stanley-fork/sol-1/general_docs/5.25_floppy_drive/5.25_pinout.png

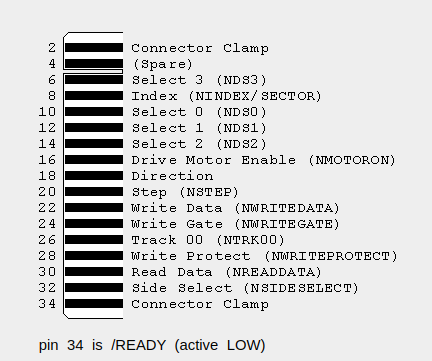
general_docs/5.25_floppy_drive/5.25_pinout.png
