stanley-fork/sol-1/general_docs/5.25_floppy_drive/bbc_master2_floppy_wd1770.gif

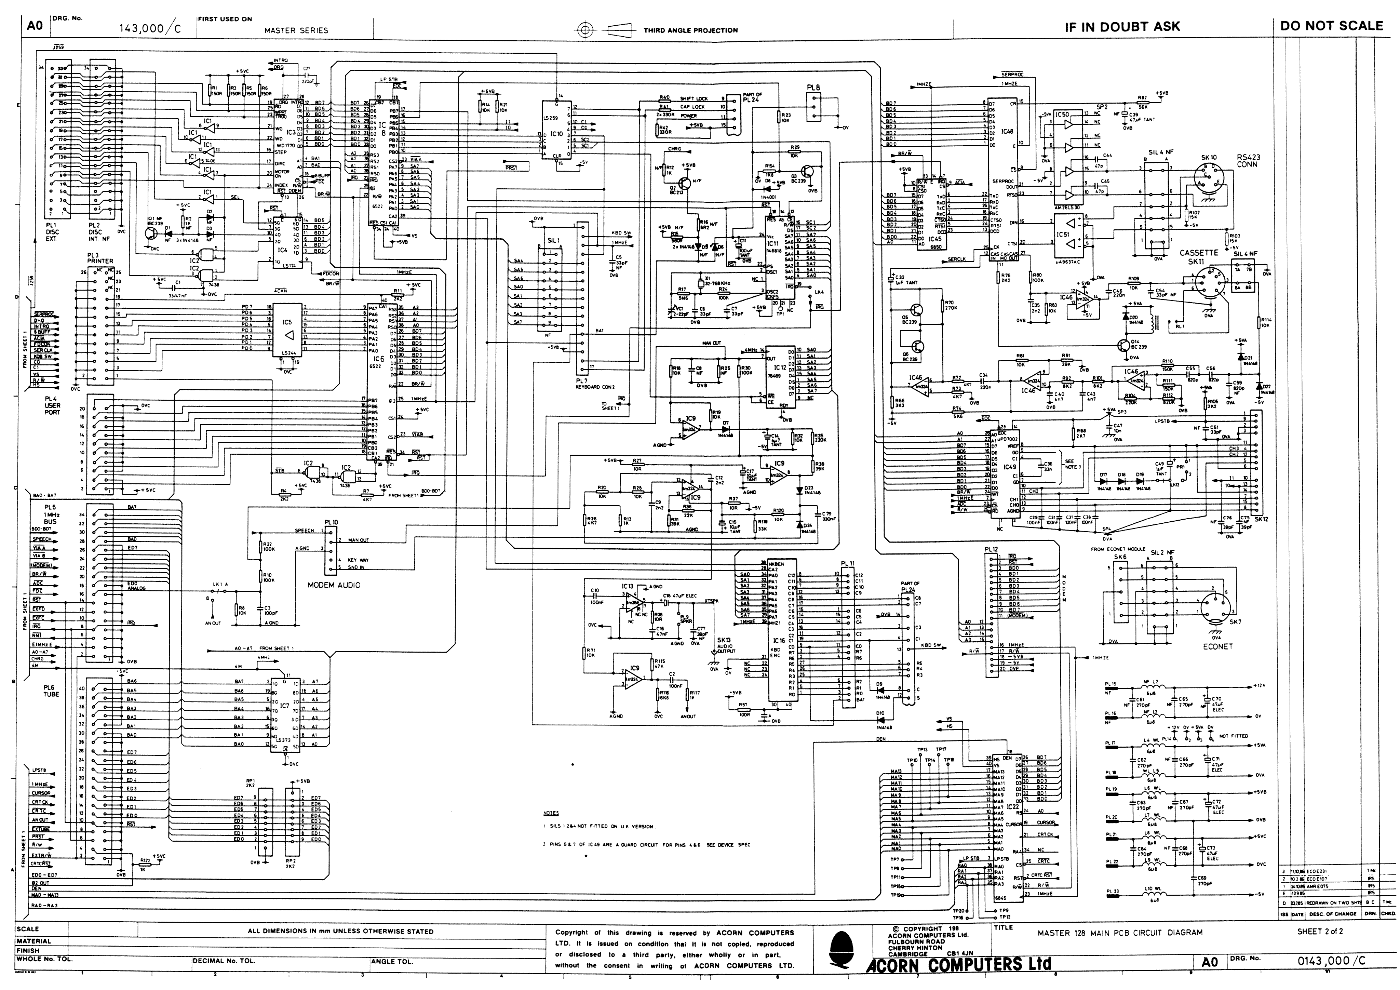
general_docs/5.25_floppy_drive/bbc_master2_floppy_wd1770.gif
