stanley-fork/sol-1/general_docs/5.25_floppy_drive/bbc_wd1772.gif

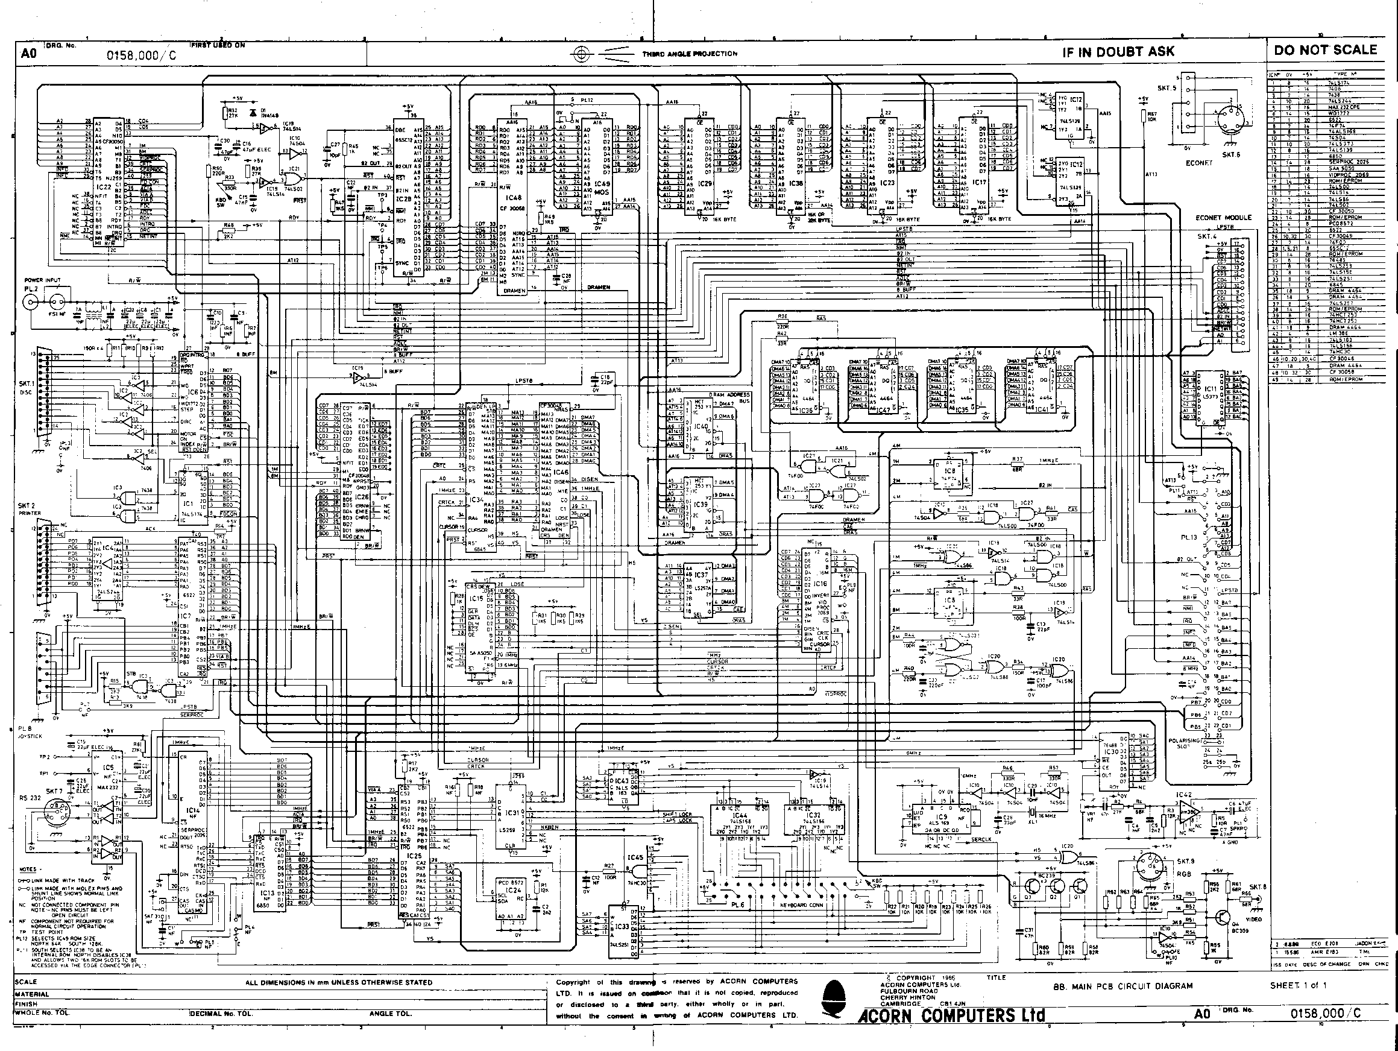
general_docs/5.25_floppy_drive/bbc_wd1772.gif
