stanley-fork/sol-1/general_docs/5.25_floppy_drive/chinon_jumpers.jpg

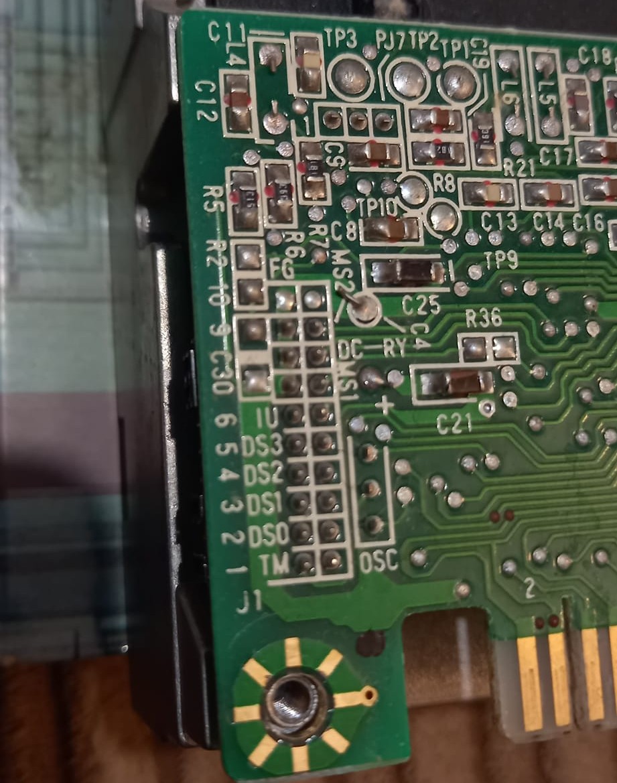
general_docs/5.25_floppy_drive/chinon_jumpers.jpg
