stanley-fork/sol-1/general_docs/5.25_floppy_drive/Floppy Disk Formats_files/hddrive.gif

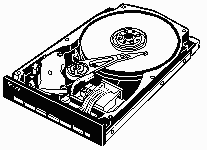
general_docs/5.25_floppy_drive/Floppy Disk Formats_files/hddrive.gif
