stanley-fork/sol-1/general_docs/5.25_floppy_drive/Low-level disk storage_files/disk-1mb.jpg

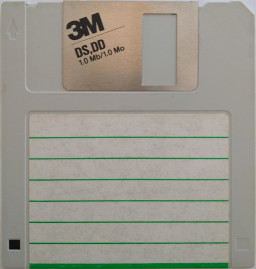
general_docs/5.25_floppy_drive/Low-level disk storage_files/disk-1mb.jpg
