stanley-fork/sol-1/general_docs/5.25_floppy_drive/Low-level disk storage_files/ibm-track-layout.png

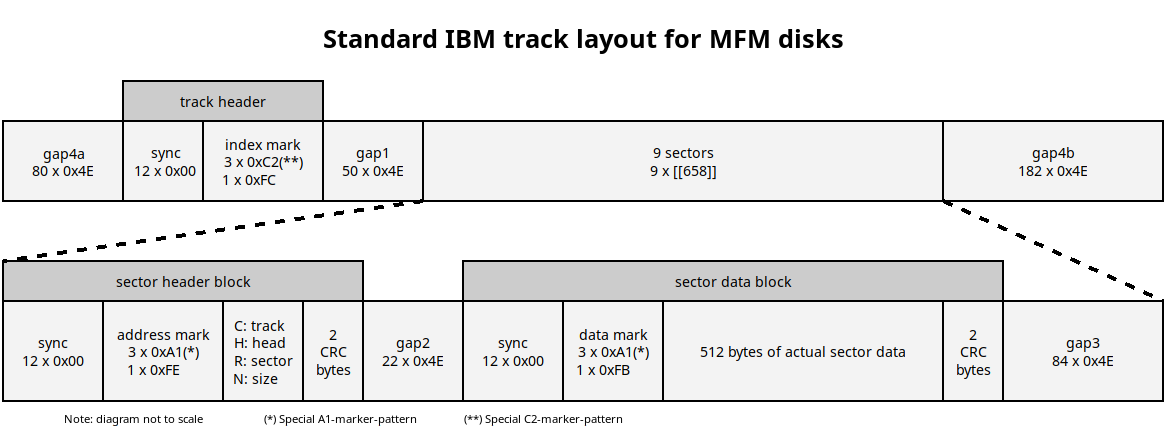
general_docs/5.25_floppy_drive/Low-level disk storage_files/ibm-track-layout.png
