stanley-fork/sol-1/general_docs/5.25_floppy_drive/master1.gif

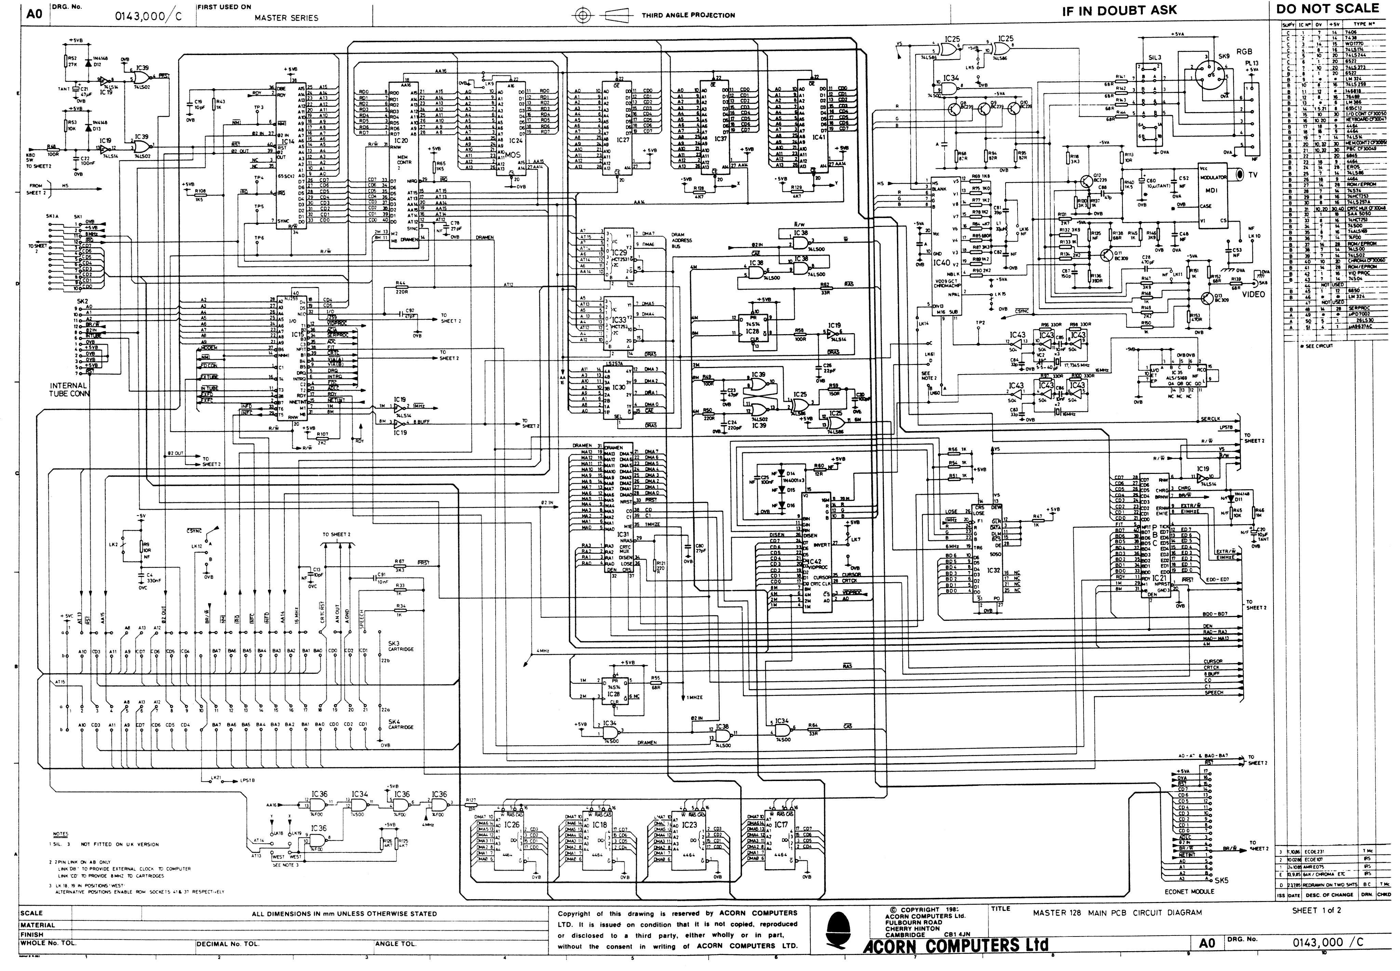
general_docs/5.25_floppy_drive/master1.gif
