stanley-fork/sol-1/general_docs/5.25_floppy_drive/pi-fdc-schematic-0.3.jpg

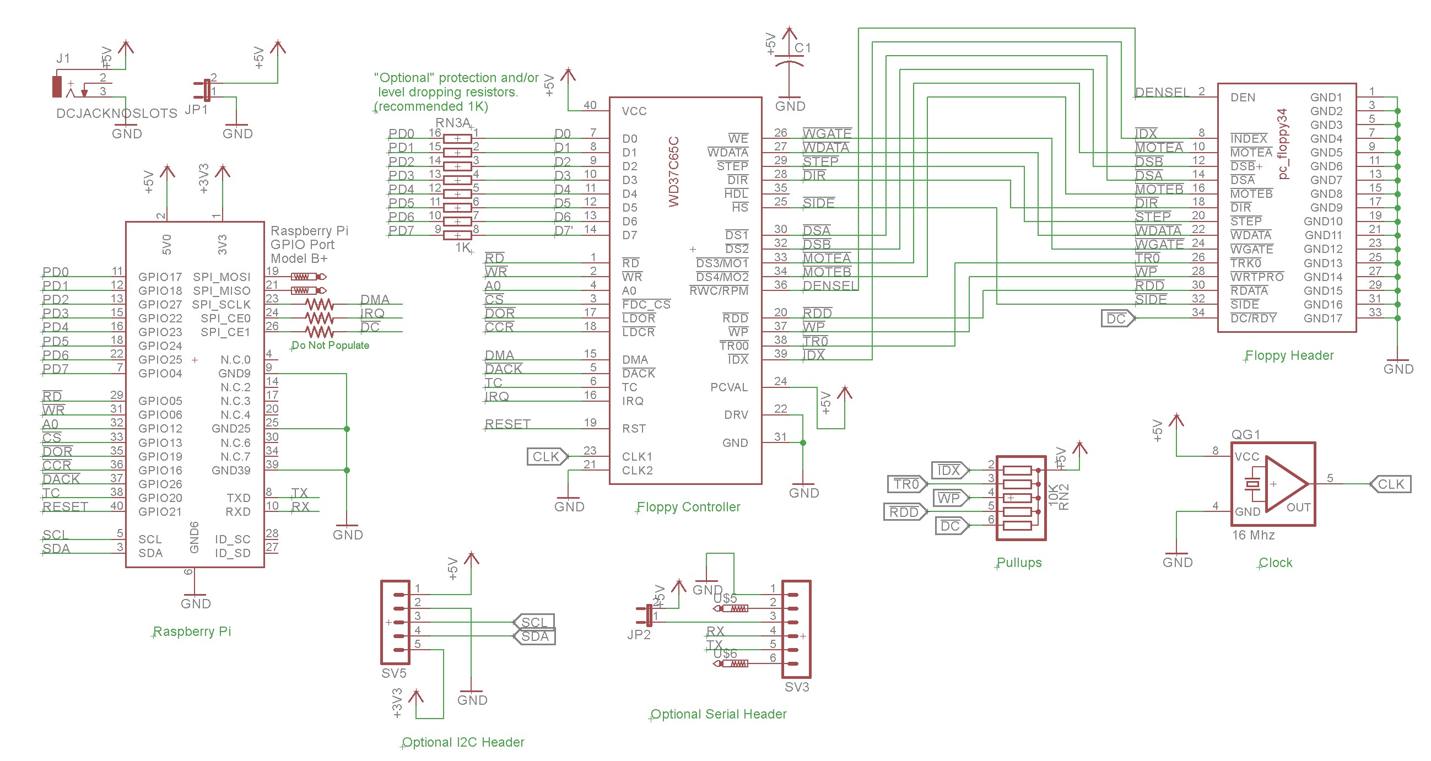
general_docs/5.25_floppy_drive/pi-fdc-schematic-0.3.jpg
