stanley-fork/sol-1/general_docs/5.25_floppy_drive/power_pinout.jpg

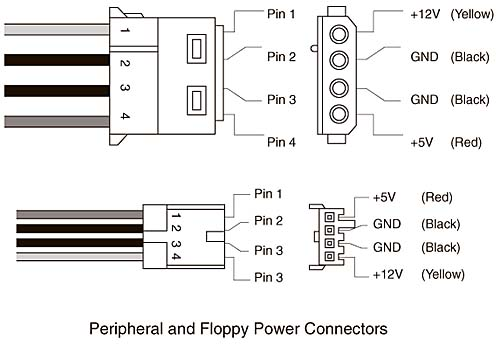
general_docs/5.25_floppy_drive/power_pinout.jpg
