stanley-fork/sol-1/general_docs/5.25_floppy_drive/rc2014-floppy-wd-sch.png

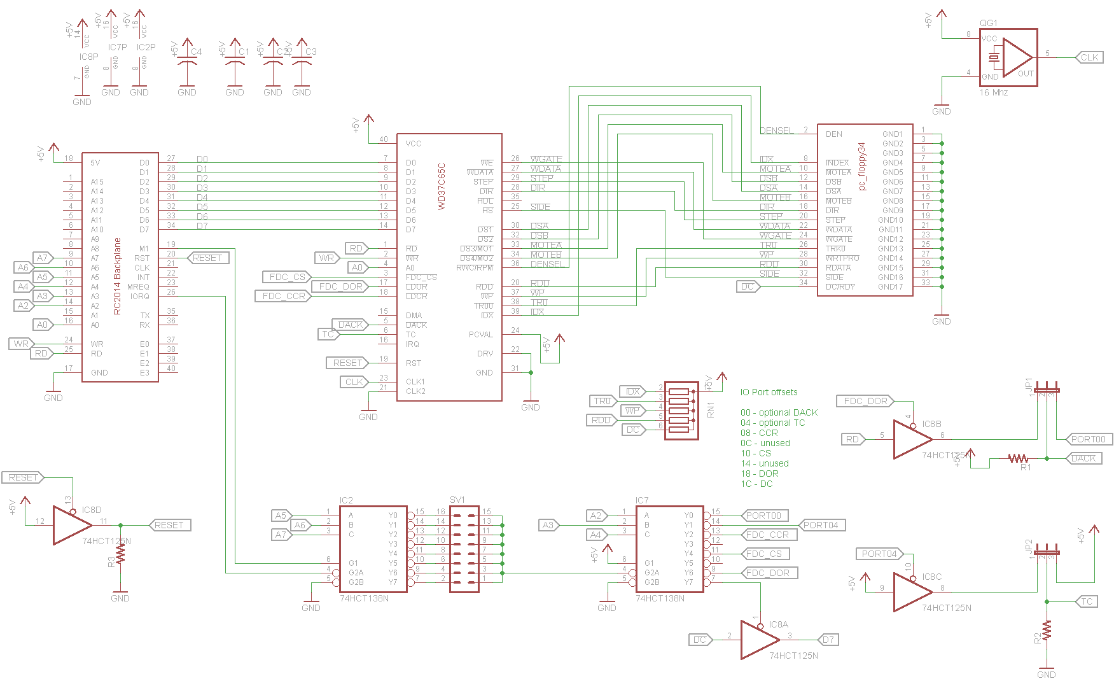
general_docs/5.25_floppy_drive/rc2014-floppy-wd-sch.png
