stanley-fork/sol-1/general_docs/5.25_floppy_drive/S100 Computers  wd1771_files/VersafloppyII RevC.jpg

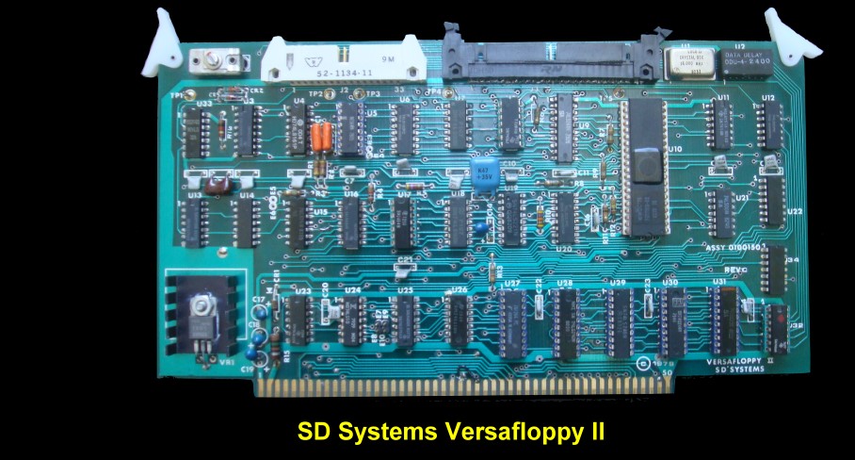
general_docs/5.25_floppy_drive/S100 Computers wd1771_files/VersafloppyII RevC.jpg
