stanley-fork/sol-1/general_docs/5.25_floppy_drive/sol-1_floppy_drives/s-l1600 (5).webp

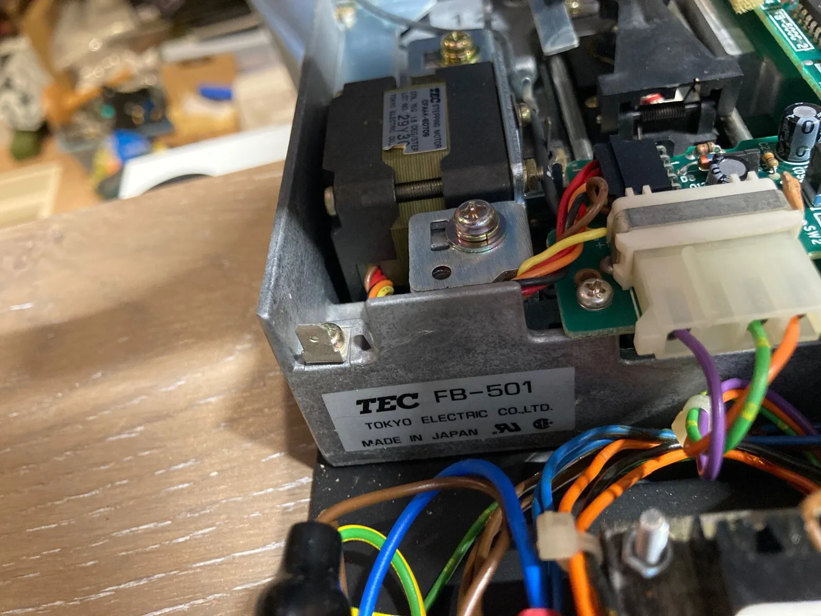
general_docs/5.25_floppy_drive/sol-1_floppy_drives/s-l1600 (5).webp
