stanley-fork/sol-1/general_docs/5.25_floppy_drive/track_format.png

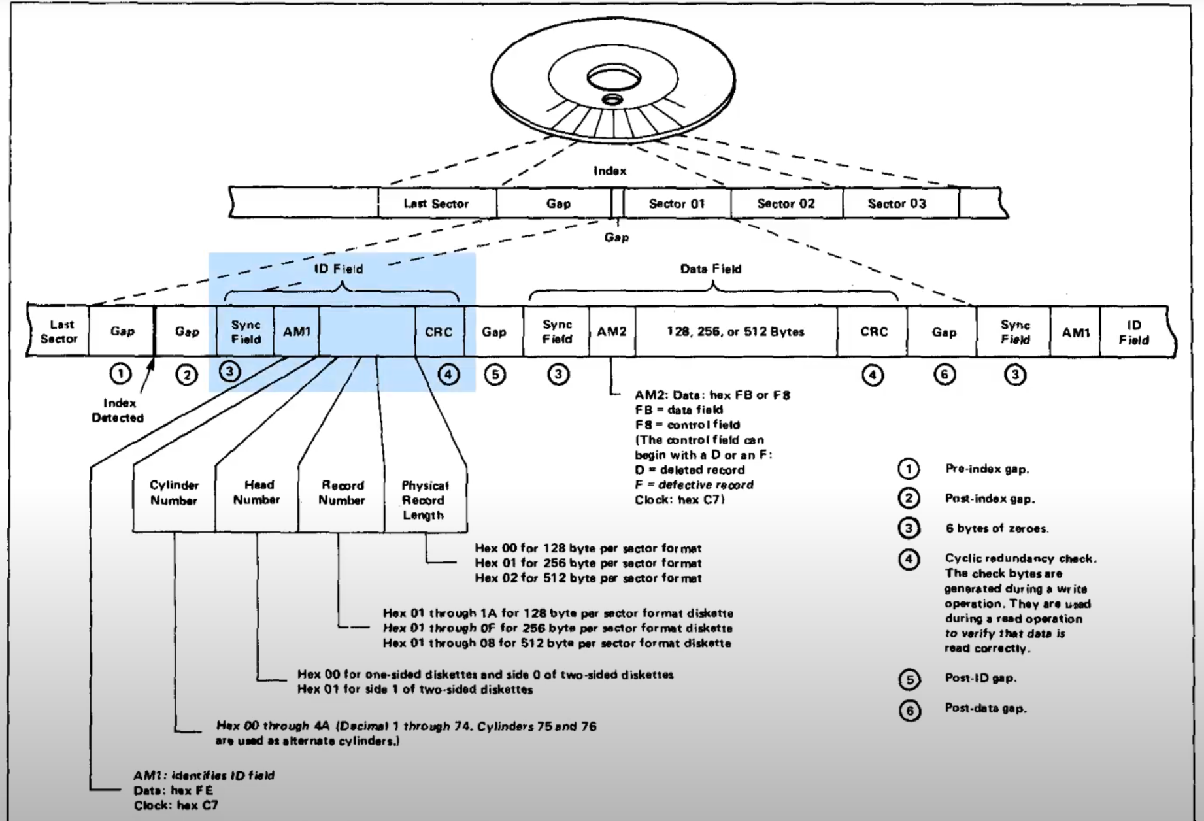
general_docs/5.25_floppy_drive/track_format.png
