stanley-fork/sol-1/general_docs/5.25_floppy_drive/wd1770_formatting.png

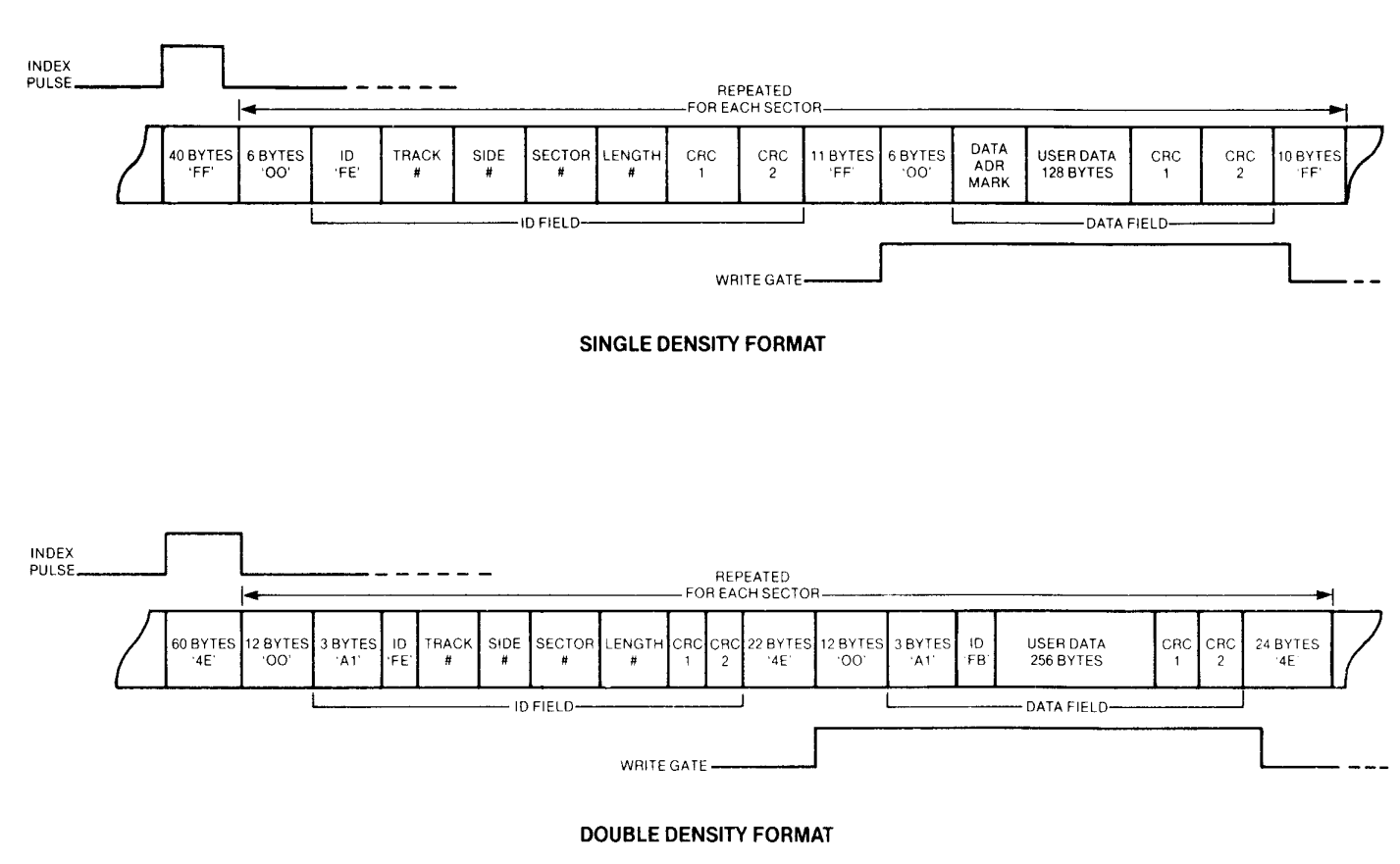
general_docs/5.25_floppy_drive/wd1770_formatting.png
