stanley-fork/sol-1/general_docs/division2.png

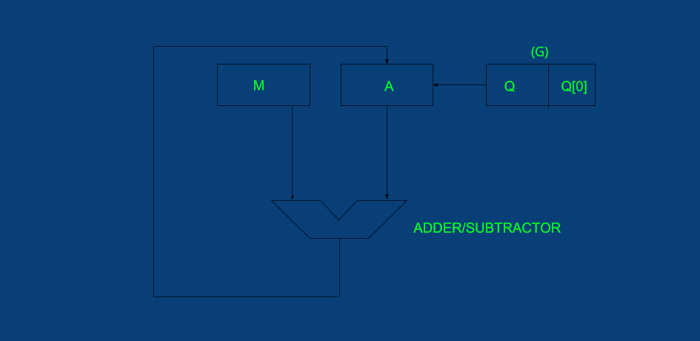
general_docs/division2.png
