stanley-fork/sol-1/hardware/board-images/frontpanel/front_panel_orange.jpg

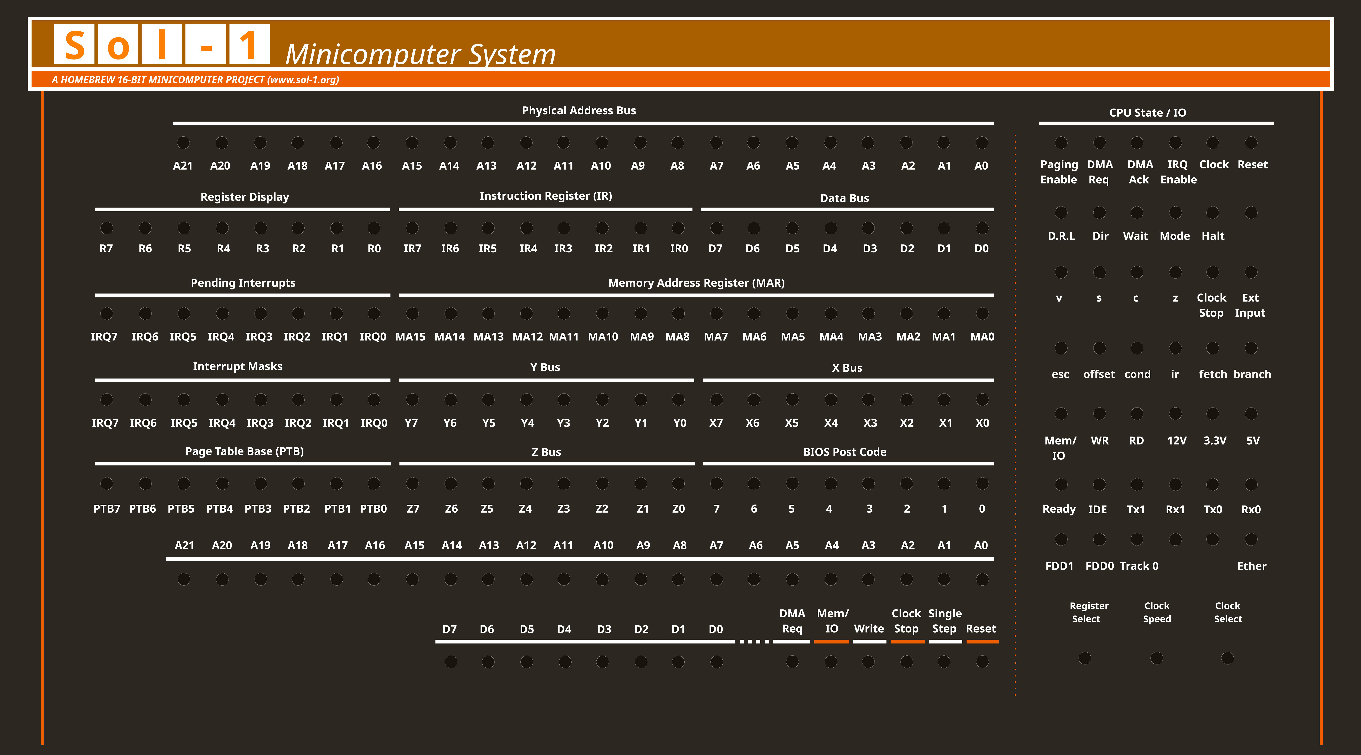
hardware/board-images/frontpanel/front_panel_orange.jpg
