stanley-fork/sol-1/images/513552633_754775293648044_8493645903438543306_n.jpg

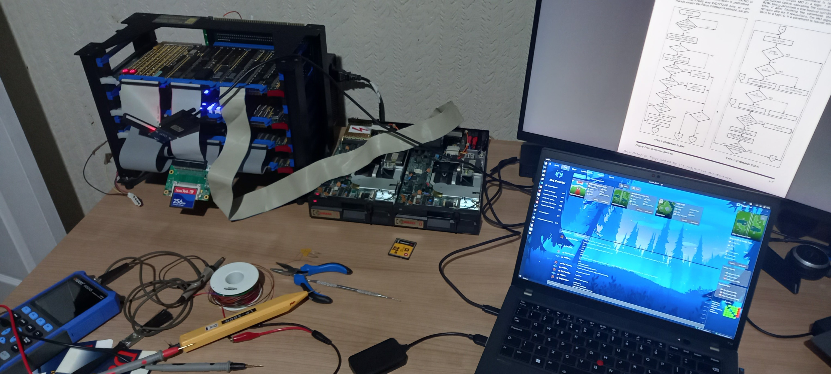
images/513552633_754775293648044_8493645903438543306_n.jpg
