stanley-fork/sol-1/web/images/bg/background.jpg

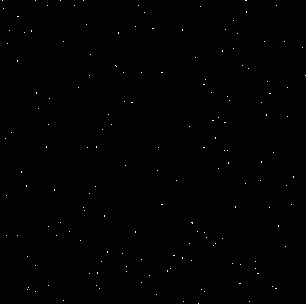
web/images/bg/background.jpg
