stanley-fork/sol-1/general_docs/5.25_floppy_drive/flock-v2-main/images/Flock-V2-Assembled_Board_in_Backplane.jpg

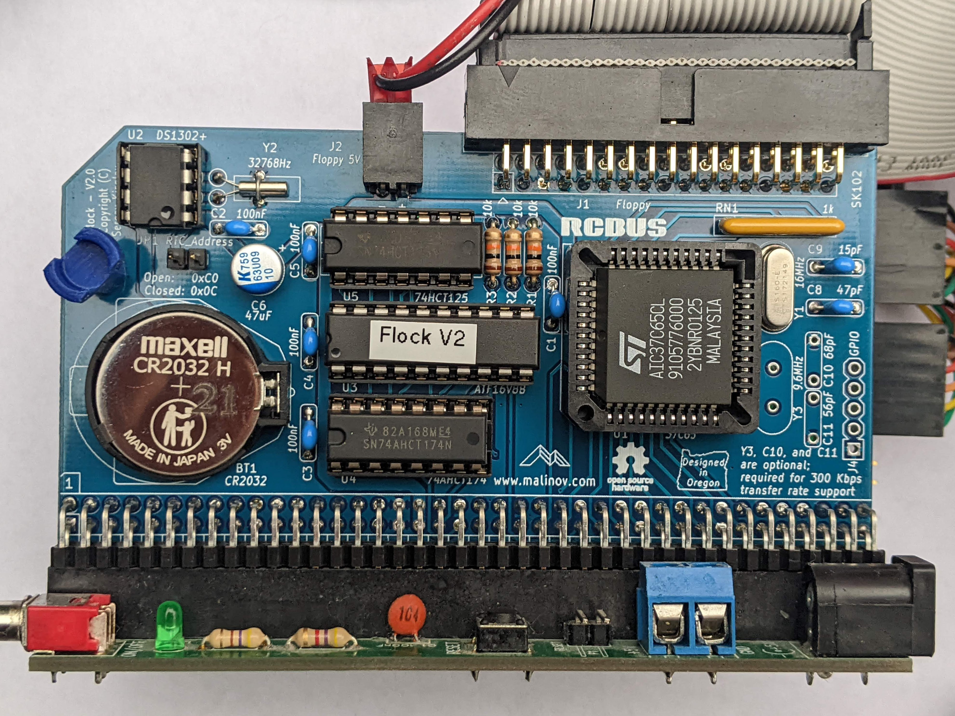
general_docs/5.25_floppy_drive/flock-v2-main/images/Flock-V2-Assembled_Board_in_Backplane.jpg
