stanley-fork/sol-1/general_docs/5.25_floppy_drive/Operating Systems Development Series_files/flpy.png

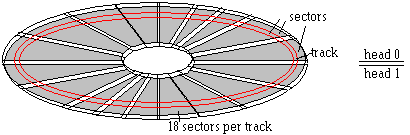
general_docs/5.25_floppy_drive/Operating Systems Development Series_files/flpy.png
