stanley-fork/sol-1/hardware/schematics/kicad/registers_paging_irq.kicad_sch

## KiCad design hardware/schematics/kicad/registers_paging_irq.kicad_sch (2025-10-18)

Schematic: registers_paging_irq.kicad_sch

Parts:
IC43, IC113: 7404N; DIP-14_W7.62mm
IC46, IC52: 7400N; DIP-14_W7.62mm
IC53, IC54, IC55, IC56, IC57, IC58, IC59, IC60, IC61, IC62, IC63, IC64, IC71, IC72, IC73, IC74, IC75, IC84, IC85, IC87, IC88, IC90, IC93, IC191: 74377N; DIP-20_W7.62mm
IC70: 7432N; DIP-14_W7.62mm
IC109: 7427N; DIP-14_W7.62mm
IC111, IC112, IC157, IC158, IC159, IC160, IC180, IC190: 74257N; DIP-16_W7.62mm
IC117, IC118, IC119, IC120, IC178, IC179: 74244N; DIP-20_W7.62mm
IC123, IC124, IC125, IC126, IC127, IC128, IC129, IC130, IC131, IC132, IC133, IC134, IC135, IC136, IC137, IC138, IC141, IC142, IC143, IC144, IC145, IC146, IC147, IC148, IC149, IC150, IC151, IC152, IC153, IC154, IC166, IC167: 74151N; DIP-16_W7.62mm
IC139, IC140, IC168, IC169: 74153N; DIP-16_W7.62mm
IC163, IC177: 58C256P; DIP-28_W15.24mm
IC181, IC182, IC183, IC184: 74157N; DIP-16_W7.62mm
IRQ_0_DFF1, IRQ_1_DFF1, IRQ_2_DFF1, IRQ_3_DFF1: 7474N; DIP-14_W7.62mm
IRQ_AND_1, IRQ_AND_2: 7408N; DIP-14_W7.62mm
IRQ_CODE1: 74377N; DIP-20_W7.62mm
IRQ_ENCODER1: 74148N; DIP-16_W7.62mm
IRQ_RST_DECODER1: 74138N; DIP-16_W7.62mm
IRQ_STATUS_1: 74273N; DIP-20_W7.62mm
MARH1: 74377N; DIP-20_W7.62mm
MARL1: 74377N; DIP-20_W7.62mm
MDRH1: 74377N; DIP-20_W7.62mm
MDRL1: 74377N; DIP-20_W7.62mm
MDR_IN_MUX_1, MDR_IN_MUX_2: 74157N; DIP-16_W7.62mm
MDR_OUT_MUX_1, MDR_OUT_MUX_2: 74157N; DIP-16_W7.62mm
RN2: R_Pack08; DIP-16_W7.62mm
U19: 74HC04; DIP-14_W7.62mm

Connections:
GND: IC109.2 (I1), IC111.15 (G), IC112.5 (2A), IC112.6 (2B), IC112.10 (3B), IC112.11 (3A), IC112.13 (4B), IC112.14 (4A), IC112.15 (G), IC120.4 (A2), IC120.6 (A3), IC120.8 (A4), IC123.7 (G), IC124.7 (G), IC125.7 (G), IC126.7 (G), IC126.12 (D7), IC126.13 (D6), IC126.14 (D5), IC127.7 (G), IC128.7 (G), IC129.7 (G), IC130.7 (G), IC130.12 (D7), IC130.13 (D6), IC130.14 (D5), IC131.7 (G), IC132.7 (G), IC133.7 (G), IC134.7 (G), IC134.12 (D7), IC134.13 (D6), IC134.14 (D5), IC135.7 (G), IC136.7 (G), IC137.7 (G), IC138.7 (G), IC138.12 (D7), IC138.13 (D6), IC138.14 (D5), IC139.1 (1G), IC139.15 (2G), IC140.1 (1G), IC140.15 (2G), IC141.7 (G), IC142.7 (G), IC143.7 (G), IC144.7 (G), IC144.12 (D7), IC144.13 (D6), IC144.14 (D5), IC145.7 (G), IC146.7 (G), IC147.7 (G), IC148.7 (G), IC148.12 (D7), IC148.13 (D6), IC148.14 (D5), IC149.7 (G), IC150.7 (G), IC151.7 (G), IC152.7 (G), IC152.12 (D7), IC152.13 (D6), IC152.14 (D5), IC153.7 (G), IC154.7 (G), IC157.15 (G), IC158.5 (2A), IC158.11 (3A), IC158.14 (4A), IC158.15 (G), IC159.2 (1A), IC159.5 (2A), IC159.11 (3A), IC159.15 (G), IC160.11 (3A), IC160.14 (4A), IC160.15 (G), IC163.1 (A14), IC163.14 (VSS), IC163.20 (~CE), IC163.26 (A13), IC166.7 (G), IC167.7 (G), IC167.12 (D7), IC167.13 (D6), IC167.14 (D5), IC168.1 (1G), IC168.15 (2G), IC169.1 (1G), IC169.15 (2G), IC177.1 (A14), IC177.14 (VSS), IC177.20 (~CE), IC177.26 (A13), IC180.2 (1A), IC180.5 (2A), IC180.11 (3A), IC180.14 (4A), IC180.15 (G), IC181.15 (G), IC182.15 (G), IC183.15 (G), IC184.15 (G), IC190.2 (1A), IC190.5 (2A), IC190.11 (3A), IC190.14 (4A), IC190.15 (G), IRQ_CODE1.3 (1D), IRQ_CODE1.13 (5D), IRQ_CODE1.14 (6D), IRQ_CODE1.17 (7D), IRQ_CODE1.18 (8D), IRQ_ENCODER1.5 (EI), IRQ_RST_DECODER1.4 (G2A), IRQ_RST_DECODER1.5 (G2B), MDR_IN_MUX_1.15 (G), MDR_IN_MUX_2.15 (G), RN2.1 (R1.1), RN2.2 (R2.1), RN2.3 (R3.1), RN2.4 (R4.1), RN2.5 (R5.1), RN2.6 (R6.1), RN2.7 (R7.1), RN2.8 (R8.1)
unnamed: IC46.3 (O), IRQ_ENCODER1.4 (7)
unnamed: IC46.6 (O), IRQ_ENCODER1.3 (6)
unnamed: IC46.8 (O), IRQ_ENCODER1.2 (5)
unnamed: IC46.11 (O), IRQ_ENCODER1.1 (4)
unnamed: IC52.3 (O), IRQ_ENCODER1.13 (3)
unnamed: IC52.6 (O), IRQ_ENCODER1.12 (2)
unnamed: IC52.8 (O), IRQ_ENCODER1.11 (1)
unnamed: IC52.11 (O), IRQ_ENCODER1.10 (0)
unnamed: IC70.3 (O), IC90.1 (G)
unnamed: IC70.6 (O), IC93.1 (G)
unnamed: IC109.12 (O), IC111.1 (~A/B), IC112.1 (~A/B)
unnamed: IC113.8 (O), IC163.27 (~WE), IC177.27 (~WE)
unnamed: IC118.8 (A4), IC157.4 (1Y)
unnamed: IC118.11 (A1), IC157.7 (2Y)
unnamed: IC118.13 (A2), IC157.9 (3Y)
unnamed: IC118.15 (A3), IC157.12 (4Y)
unnamed: IC118.17 (A4), IC158.4 (1Y)
unnamed: IC119.2 (A1), IC158.7 (2Y)
unnamed: IC119.4 (A2), IC158.9 (3Y)
unnamed: IC119.6 (A3), IC158.12 (4Y)
unnamed: IC119.8 (A4), IC159.4 (1Y)
unnamed: IC119.11 (A1), IC159.7 (2Y)
unnamed: IC119.13 (A2), IC159.9 (3Y)
unnamed: IC119.15 (A3), IC159.12 (4Y)
unnamed: IC119.17 (A4), IC160.4 (1Y)
unnamed: IC120.2 (A1), IC160.7 (2Y)
unnamed: IC123.5 (Y), IC139.6 (1C0)
unnamed: IC124.5 (Y), IC139.5 (1C1)
unnamed: IC125.5 (Y), IC139.4 (1C2)
unnamed: IC126.5 (Y), IC139.3 (1C3)
unnamed: IC127.5 (Y), IC139.10 (2C0)
unnamed: IC128.5 (Y), IC139.11 (2C1)
unnamed: IC129.5 (Y), IC139.12 (2C2)
unnamed: IC130.5 (Y), IC139.13 (2C3)
unnamed: IC131.5 (Y), IC140.6 (1C0)
unnamed: IC132.5 (Y), IC140.5 (1C1)
unnamed: IC133.5 (Y), IC140.4 (1C2)
unnamed: IC134.5 (Y), IC140.3 (1C3)
unnamed: IC135.5 (Y), IC140.10 (2C0)
unnamed: IC136.5 (Y), IC140.11 (2C1)
unnamed: IC137.5 (Y), IC140.12 (2C2)
unnamed: IC138.5 (Y), IC140.13 (2C3)
unnamed: IC141.5 (Y), IC168.6 (1C0)
unnamed: IC142.5 (Y), IC168.5 (1C1)
unnamed: IC143.5 (Y), IC168.4 (1C2)
unnamed: IC144.5 (Y), IC168.3 (1C3)
unnamed: IC145.5 (Y), IC168.10 (2C0)
unnamed: IC146.5 (Y), IC168.11 (2C1)
unnamed: IC147.5 (Y), IC168.12 (2C2)
unnamed: IC148.5 (Y), IC168.13 (2C3)
unnamed: IC149.5 (Y), IC169.6 (1C0)
unnamed: IC150.5 (Y), IC169.5 (1C1)
unnamed: IC151.5 (Y), IC169.4 (1C2)
unnamed: IC152.5 (Y), IC169.3 (1C3)
unnamed: IC153.5 (Y), IC169.10 (2C0)
unnamed: IC154.5 (Y), IC169.11 (2C1)
unnamed: IC157.3 (1B), IC163.11 (I/O0), IC178.18 (Y1)
unnamed: IC157.6 (2B), IC163.12 (I/O1), IC178.16 (Y2)
unnamed: IC157.10 (3B), IC163.13 (I/O2), IC178.14 (Y3)
unnamed: IC157.13 (4B), IC163.15 (I/O3), IC178.12 (Y4)
unnamed: IC158.3 (1B), IC163.16 (I/O4), IC178.9 (Y1)
unnamed: IC158.6 (2B), IC163.17 (I/O5), IC178.7 (Y2)
unnamed: IC158.10 (3B), IC163.18 (I/O6), IC178.5 (Y3)
unnamed: IC158.13 (4B), IC163.19 (I/O7), IC178.3 (Y4)
unnamed: IC159.3 (1B), IC177.11 (I/O0), IC179.18 (Y1)
unnamed: IC159.6 (2B), IC177.12 (I/O1), IC179.16 (Y2)
unnamed: IC159.10 (3B), IC177.13 (I/O2), IC179.14 (Y3)
unnamed: IC159.13 (4B), IC177.15 (I/O3), IC179.12 (Y4)
unnamed: IC160.3 (1B), IC177.16 (I/O4), IC179.9 (Y1)
unnamed: IC160.6 (2B), IC177.17 (I/O5), IC179.7 (Y2)
unnamed: IC160.10 (3B), IC177.18 (I/O6), IC179.5 (Y3)
unnamed: IC160.13 (4B), IC177.19 (I/O7), IC179.3 (Y4)
unnamed: IC163.2 (A12), IC177.2 (A12), IC190.12 (4Y)
unnamed: IC163.3 (A7), IC177.3 (A7), IC180.9 (3Y)
unnamed: IC163.4 (A6), IC177.4 (A6), IC180.7 (2Y)
unnamed: IC163.5 (A5), IC177.5 (A5), IC180.4 (1Y)
unnamed: IC163.21 (A10), IC177.21 (A10), IC190.7 (2Y)
unnamed: IC163.23 (A11), IC177.23 (A11), IC190.9 (3Y)
unnamed: IC163.24 (A9), IC177.24 (A9), IC190.4 (1Y)
unnamed: IC163.25 (A8), IC177.25 (A8), IC180.12 (4Y)
unnamed: IC166.5 (Y), IC169.12 (2C2)
unnamed: IC167.5 (Y), IC169.13 (2C3)
unnamed: IC43.8 (O), IC178.1 (G), IC178.19 (G), IC179.1 (G), IC179.19 (G)
unnamed: IC180.3 (1B), IC191.2 (1Q)
unnamed: IC180.6 (2B), IC191.5 (2Q)
unnamed: IC180.10 (3B), IC191.6 (3Q)
unnamed: IC180.13 (4B), IC191.9 (4Q)
unnamed: IC181.4 (1Y), MARL1.3 (1D)
unnamed: IC181.7 (2Y), MARL1.4 (2D)
unnamed: IC181.9 (3Y), MARL1.7 (3D)
unnamed: IC181.12 (4Y), MARL1.8 (4D)
unnamed: IC182.4 (1Y), MARL1.13 (5D)
unnamed: IC182.7 (2Y), MARL1.14 (6D)
unnamed: IC182.9 (3Y), MARL1.17 (7D)
unnamed: IC182.12 (4Y), MARL1.18 (8D)
unnamed: IC183.4 (1Y), MARH1.3 (1D)
unnamed: IC183.7 (2Y), MARH1.4 (2D)
unnamed: IC183.9 (3Y), MARH1.7 (3D)
unnamed: IC183.12 (4Y), MARH1.8 (4D)
unnamed: IC184.4 (1Y), MARH1.13 (5D)
unnamed: IC184.7 (2Y), MARH1.14 (6D)
unnamed: IC184.9 (3Y), MARH1.17 (7D)
unnamed: IC184.12 (4Y), MARH1.18 (8D)
unnamed: IC190.3 (1B), IC191.12 (5Q)
unnamed: IC190.6 (2B), IC191.15 (6Q)
unnamed: IC190.10 (3B), IC191.16 (7Q)
unnamed: IC190.13 (4B), IC191.19 (8Q)
unnamed: IRQ_0_DFF1.1 (CLR), IRQ_AND_1.3 (O)
unnamed: IRQ_0_DFF1.5 (Q), IRQ_STATUS_1.3 (D1)
unnamed: IRQ_0_DFF1.9 (Q), IRQ_STATUS_1.4 (D2)
unnamed: IRQ_0_DFF1.13 (CLR), IRQ_AND_1.6 (O)
unnamed: IRQ_1_DFF1.1 (CLR), IRQ_AND_1.8 (O)
unnamed: IRQ_1_DFF1.5 (Q), IRQ_STATUS_1.7 (D3)
unnamed: IRQ_1_DFF1.9 (Q), IRQ_STATUS_1.8 (D4)
unnamed: IRQ_1_DFF1.13 (CLR), IRQ_AND_1.11 (O)
unnamed: IRQ_2_DFF1.1 (CLR), IRQ_AND_2.3 (O)
unnamed: IRQ_2_DFF1.5 (Q), IRQ_STATUS_1.13 (D5)
unnamed: IRQ_2_DFF1.9 (Q), IRQ_STATUS_1.14 (D6)
unnamed: IRQ_2_DFF1.13 (CLR), IRQ_AND_2.6 (O)
unnamed: IRQ_3_DFF1.1 (CLR), IRQ_AND_2.8 (O)
unnamed: IRQ_3_DFF1.5 (Q), IRQ_STATUS_1.17 (D7)
unnamed: IRQ_3_DFF1.9 (Q), IRQ_STATUS_1.18 (D8)
unnamed: IRQ_3_DFF1.13 (CLR), IRQ_AND_2.11 (O)
unnamed: IRQ_AND_1.2 (I1), IRQ_RST_DECODER1.15 (Y0)
unnamed: IRQ_CODE1.4 (2D), IRQ_ENCODER1.9 (A0)
unnamed: IRQ_CODE1.7 (3D), IRQ_ENCODER1.7 (A1)
unnamed: IRQ_CODE1.8 (4D), IRQ_ENCODER1.6 (A2)
unnamed: MDRH1.3 (1D), MDRL1.3 (1D), MDR_IN_MUX_1.4 (1Y)
unnamed: MDRH1.4 (2D), MDRL1.4 (2D), MDR_IN_MUX_1.7 (2Y)
unnamed: MDRH1.7 (3D), MDRL1.7 (3D), MDR_IN_MUX_1.9 (3Y)
unnamed: MDRH1.8 (4D), MDRL1.8 (4D), MDR_IN_MUX_1.12 (4Y)
unnamed: MDRH1.13 (5D), MDRL1.13 (5D), MDR_IN_MUX_2.4 (1Y)
unnamed: MDRH1.14 (6D), MDRL1.14 (6D), MDR_IN_MUX_2.7 (2Y)
unnamed: MDRH1.17 (7D), MDRL1.17 (7D), MDR_IN_MUX_2.9 (3Y)
unnamed: MDRH1.18 (8D), MDRL1.18 (8D), MDR_IN_MUX_2.12 (4Y)
unnamed: MDR_OUT_MUX_1.15 (G), MDR_OUT_MUX_2.15 (G), U19.2
address_bus0: IC117.18 (Y1)
address_bus1: IC117.16 (Y2)
address_bus2: IC117.14 (Y3)
address_bus3: IC117.12 (Y4)
address_bus4: IC117.9 (Y1)
address_bus5: IC117.7 (Y2)
address_bus6: IC117.5 (Y3)
address_bus7: IC117.3 (Y4)
address_bus8: IC118.18 (Y1)
address_bus9: IC118.16 (Y2)
address_bus10: IC118.14 (Y3)
address_bus11: IC118.12 (Y4)
address_bus12: IC118.9 (Y1)
address_bus13: IC118.7 (Y2)
address_bus14: IC118.5 (Y3)
address_bus15: IC118.3 (Y4)
address_bus16: IC119.18 (Y1)
address_bus17: IC119.16 (Y2)
address_bus18: IC119.14 (Y3)
address_bus19: IC119.12 (Y4)
address_bus20: IC119.9 (Y1)
address_bus21: IC119.7 (Y2)
ah0: IC54.2 (1Q), IC123.3 (D1)
ah1: IC54.5 (2Q), IC127.3 (D1)
ah2: IC54.6 (3Q), IC131.3 (D1)
ah3: IC54.9 (4Q), IC135.3 (D1)
ah4: IC54.12 (5Q), IC141.3 (D1)
ah5: IC54.15 (6Q), IC145.3 (D1)
ah6: IC54.16 (7Q), IC149.3 (D1)
ah7: IC54.19 (8Q), IC153.3 (D1)
ah_wrt: IC54.1 (G)
al0: IC53.2 (1Q), IC123.4 (D0)
al1: IC53.5 (2Q), IC127.4 (D0)
al2: IC53.6 (3Q), IC131.4 (D0)
al3: IC53.9 (4Q), IC135.4 (D0)
al4: IC53.12 (5Q), IC141.4 (D0)
al5: IC53.15 (6Q), IC145.4 (D0)
al6: IC53.16 (7Q), IC149.4 (D0)
al7: IC53.19 (8Q), IC153.4 (D0)
al_wrt: IC53.1 (G)
alu_a_src_0: IC111.3 (1B)
alu_a_src_0_muxed: IC111.4 (1Y), IC123.11 (A), IC124.11 (A), IC125.11 (A), IC126.11 (A), IC127.11 (A), IC128.11 (A), IC129.11 (A), IC130.11 (A), IC131.11 (A), IC132.11 (A), IC133.11 (A), IC134.11 (A), IC135.11 (A), IC136.11 (A), IC137.11 (A), IC138.11 (A), IC141.11 (A), IC142.11 (A), IC143.11 (A), IC144.11 (A), IC145.11 (A), IC146.11 (A), IC147.11 (A), IC148.11 (A), IC149.11 (A), IC150.11 (A), IC151.11 (A), IC152.11 (A), IC153.11 (A), IC154.11 (A), IC166.11 (A), IC167.11 (A)
alu_a_src_1: IC111.6 (2B)
alu_a_src_1_muxed: IC111.7 (2Y), IC123.10 (B), IC124.10 (B), IC125.10 (B), IC126.10 (B), IC127.10 (B), IC128.10 (B), IC129.10 (B), IC130.10 (B), IC131.10 (B), IC132.10 (B), IC133.10 (B), IC134.10 (B), IC135.10 (B), IC136.10 (B), IC137.10 (B), IC138.10 (B), IC141.10 (B), IC142.10 (B), IC143.10 (B), IC144.10 (B), IC145.10 (B), IC146.10 (B), IC147.10 (B), IC148.10 (B), IC149.10 (B), IC150.10 (B), IC151.10 (B), IC152.10 (B), IC153.10 (B), IC154.10 (B), IC166.10 (B), IC167.10 (B)
alu_a_src_2: IC111.10 (3B)
alu_a_src_2_muxed: IC111.9 (3Y), IC123.9 (C), IC124.9 (C), IC125.9 (C), IC126.9 (C), IC127.9 (C), IC128.9 (C), IC129.9 (C), IC130.9 (C), IC131.9 (C), IC132.9 (C), IC133.9 (C), IC134.9 (C), IC135.9 (C), IC136.9 (C), IC137.9 (C), IC138.9 (C), IC141.9 (C), IC142.9 (C), IC143.9 (C), IC144.9 (C), IC145.9 (C), IC146.9 (C), IC147.9 (C), IC148.9 (C), IC149.9 (C), IC150.9 (C), IC151.9 (C), IC152.9 (C), IC153.9 (C), IC154.9 (C), IC166.9 (C), IC167.9 (C)
alu_a_src_3: IC111.13 (4B)
alu_a_src_3_muxed: IC111.12 (4Y), IC139.14 (A), IC140.14 (A), IC168.14 (A), IC169.14 (A)
alu_a_src_4: IC112.3 (1B)
alu_a_src_4_muxed: IC112.4 (1Y), IC139.2 (B), IC140.2 (B), IC168.2 (B), IC169.2 (B)
bh0: IC56.2 (1Q), IC123.1 (D3)
bh1: IC56.5 (2Q), IC127.1 (D3)
bh2: IC56.6 (3Q), IC131.1 (D3)
bh3: IC56.9 (4Q), IC135.1 (D3)
bh4: IC56.12 (5Q), IC141.1 (D3)
bh5: IC56.15 (6Q), IC145.1 (D3)
bh6: IC56.16 (7Q), IC149.1 (D3)
bh7: IC56.19 (8Q), IC153.1 (D3)
bh_wrt: IC56.1 (G)
bl0: IC55.2 (1Q), IC123.2 (D2)
bl1: IC55.5 (2Q), IC127.2 (D2)
bl2: IC55.6 (3Q), IC131.2 (D2)
bl3: IC55.9 (4Q), IC135.2 (D2)
bl4: IC55.12 (5Q), IC141.2 (D2)
bl5: IC55.15 (6Q), IC145.2 (D2)
bl6: IC55.16 (7Q), IC149.2 (D2)
bl7: IC55.19 (8Q), IC153.2 (D2)
bl_wrt: IC55.1 (G)
bph0: IC72.2 (1Q), IC124.1 (D3)
bph1: IC72.5 (2Q), IC128.1 (D3)
bph2: IC72.6 (3Q), IC132.1 (D3)
bph3: IC72.9 (4Q), IC136.1 (D3)
bph4: IC72.12 (5Q), IC142.1 (D3)
bph5: IC72.15 (6Q), IC146.1 (D3)
bph6: IC72.16 (7Q), IC150.1 (D3)
bph7: IC72.19 (8Q), IC154.1 (D3)
bph_wrt: IC72.1 (G)
bpl0: IC71.2 (1Q), IC124.2 (D2)
bpl1: IC71.5 (2Q), IC128.2 (D2)
bpl2: IC71.6 (3Q), IC132.2 (D2)
bpl3: IC71.9 (4Q), IC136.2 (D2)
bpl4: IC71.12 (5Q), IC142.2 (D2)
bpl5: IC71.15 (6Q), IC146.2 (D2)
bpl6: IC71.16 (7Q), IC150.2 (D2)
bpl7: IC71.19 (8Q), IC154.2 (D2)
bpl_wrt: IC71.1 (G)
bus_mem_io: IC119.5 (Y3)
bus_tristate: IC109.1 (I0), IC117.1 (G), IC117.19 (G), IC118.1 (G), IC118.19 (G), IC119.1 (G), IC119.19 (G), IC120.1 (G)
ch0: IC58.2 (1Q), IC123.14 (D5)
ch1: IC58.5 (2Q), IC127.14 (D5)
ch2: IC58.6 (3Q), IC131.14 (D5)
ch3: IC58.9 (4Q), IC135.14 (D5)
ch4: IC58.12 (5Q), IC141.14 (D5)
ch5: IC58.15 (6Q), IC145.14 (D5)
ch6: IC58.16 (7Q), IC149.14 (D5)
ch7: IC58.19 (8Q), IC153.14 (D5)
ch_wrt: IC58.1 (G)
cl0: IC57.2 (1Q), IC123.15 (D4)
cl1: IC57.5 (2Q), IC127.15 (D4)
cl2: IC57.6 (3Q), IC131.15 (D4)
cl3: IC57.9 (4Q), IC135.15 (D4)
cl4: IC57.12 (5Q), IC141.15 (D4)
cl5: IC57.15 (6Q), IC145.15 (D4)
cl6: IC57.16 (7Q), IC149.15 (D4)
cl7: IC57.19 (8Q), IC153.15 (D4)
cl_wrt: IC57.1 (G)
clear_all_irqs: IC43.1 (I)
clk: IC53.11 (CLK), IC54.11 (CLK), IC55.11 (CLK), IC56.11 (CLK), IC57.11 (CLK), IC58.11 (CLK), IC59.11 (CLK), IC60.11 (CLK), IC61.11 (CLK), IC62.11 (CLK), IC63.11 (CLK), IC64.11 (CLK), IC71.11 (CLK), IC72.11 (CLK), IC73.11 (CLK), IC74.11 (CLK), IC75.11 (CLK), IC84.11 (CLK), IC85.11 (CLK), IC87.11 (CLK), IC88.11 (CLK), IC90.11 (CLK), IC93.11 (CLK), IC191.11 (CLK), IRQ_CODE1.11 (CLK), IRQ_STATUS_1.11 (CLK), MARH1.11 (CLK), MARL1.11 (CLK), MDRH1.11 (CLK), MDRL1.11 (CLK)
data_bus0: MDR_IN_MUX_1.3 (1B), MDR_OUT_MUX_1.4 (1Y)
data_bus1: MDR_IN_MUX_1.6 (2B), MDR_OUT_MUX_1.7 (2Y)
data_bus2: MDR_IN_MUX_1.10 (3B), MDR_OUT_MUX_1.9 (3Y)
data_bus3: MDR_IN_MUX_1.13 (4B), MDR_OUT_MUX_1.12 (4Y)
data_bus4: MDR_IN_MUX_2.3 (1B), MDR_OUT_MUX_2.4 (1Y)
data_bus5: MDR_IN_MUX_2.6 (2B), MDR_OUT_MUX_2.7 (2Y)
data_bus6: MDR_IN_MUX_2.10 (3B), MDR_OUT_MUX_2.9 (3Y)
data_bus7: MDR_IN_MUX_2.13 (4B), MDR_OUT_MUX_2.12 (4Y)
dh0: IC60.2 (1Q), IC123.12 (D7)
dh1: IC60.5 (2Q), IC127.12 (D7)
dh2: IC60.6 (3Q), IC131.12 (D7)
dh3: IC60.9 (4Q), IC135.12 (D7)
dh4: IC60.12 (5Q), IC141.12 (D7)
dh5: IC60.15 (6Q), IC145.12 (D7)
dh6: IC60.16 (7Q), IC149.12 (D7)
dh7: IC60.19 (8Q), IC153.12 (D7)
dh_wrt: IC60.1 (G)
dih0: IC84.2 (1Q), IC124.12 (D7)
dih1: IC84.5 (2Q), IC128.12 (D7)
dih2: IC84.6 (3Q), IC132.12 (D7)
dih3: IC84.9 (4Q), IC136.12 (D7)
dih4: IC84.12 (5Q), IC142.12 (D7)
dih5: IC84.15 (6Q), IC146.12 (D7)
dih6: IC84.16 (7Q), IC150.12 (D7)
dih7: IC84.19 (8Q), IC154.12 (D7)
dih_wrt: IC84.1 (G)
dil0: IC75.2 (1Q), IC124.13 (D6)
dil1: IC75.5 (2Q), IC128.13 (D6)
dil2: IC75.6 (3Q), IC132.13 (D6)
dil3: IC75.9 (4Q), IC136.13 (D6)
dil4: IC75.12 (5Q), IC142.13 (D6)
dil5: IC75.15 (6Q), IC146.13 (D6)
dil6: IC75.16 (7Q), IC150.13 (D6)
dil7: IC75.19 (8Q), IC154.13 (D6)
dil_wrt: IC75.1 (G)
display_reg_load: IC109.13 (I2)
dl0: IC59.2 (1Q), IC123.13 (D6)
dl1: IC59.5 (2Q), IC127.13 (D6)
dl2: IC59.6 (3Q), IC131.13 (D6)
dl3: IC59.9 (4Q), IC135.13 (D6)
dl4: IC59.12 (5Q), IC141.13 (D6)
dl5: IC59.15 (6Q), IC145.13 (D6)
dl6: IC59.16 (7Q), IC149.13 (D6)
dl7: IC59.19 (8Q), IC153.13 (D6)
dl_wrt: IC59.1 (G)
int_request: IRQ_ENCODER1.15 (EO)
int_status_0: IC46.2 (I1), IC126.15 (D4), IRQ_STATUS_1.2 (Q1)
int_status_1: IC46.5 (I1), IC130.15 (D4), IRQ_STATUS_1.5 (Q2)
int_status_2: IC46.10 (I1), IC134.15 (D4), IRQ_STATUS_1.6 (Q3)
int_status_3: IC46.13 (I1), IC138.15 (D4), IRQ_STATUS_1.9 (Q4)
int_status_4: IC52.2 (I1), IC144.15 (D4), IRQ_STATUS_1.12 (Q5)
int_status_5: IC52.5 (I1), IC148.15 (D4), IRQ_STATUS_1.15 (Q6)
int_status_6: IC52.10 (I1), IC152.15 (D4), IRQ_STATUS_1.16 (Q7)
int_status_7: IC52.13 (I1), IC167.15 (D4), IRQ_STATUS_1.19 (Q8)
irq0: RN2.16 (R1.2)
irq0_fdc: IRQ_0_DFF1.3 (CLK)
irq1: IRQ_0_DFF1.11 (CLK), RN2.15 (R2.2)
irq2: IRQ_1_DFF1.3 (CLK), RN2.14 (R3.2)
irq3: IRQ_1_DFF1.11 (CLK), RN2.13 (R4.2)
irq4: IRQ_2_DFF1.3 (CLK), RN2.12 (R5.2)
irq5: IRQ_2_DFF1.11 (CLK), RN2.11 (R6.2)
irq6: IRQ_3_DFF1.3 (CLK), RN2.10 (R7.2)
irq7_uart0: IRQ_3_DFF1.11 (CLK), RN2.9 (R8.2)
irq_ack: IRQ_RST_DECODER1.6 (G1)
irq_masks0: IC46.1 (I0), IC88.2 (1Q), IC126.1 (D3)
irq_masks1: IC46.4 (I0), IC88.5 (2Q), IC130.1 (D3)
irq_masks2: IC46.9 (I0), IC88.6 (3Q), IC134.1 (D3)
irq_masks3: IC46.12 (I0), IC88.9 (4Q), IC138.1 (D3)
irq_masks4: IC52.1 (I0), IC88.12 (5Q), IC144.1 (D3)
irq_masks5: IC52.4 (I0), IC88.15 (6Q), IC148.1 (D3)
irq_masks6: IC52.9 (I0), IC88.16 (7Q), IC152.1 (D3)
irq_masks7: IC52.12 (I0), IC88.19 (8Q), IC167.1 (D3)
irq_masks_wrt: IC88.1 (G)
irq_vector_0: IC126.2 (D2), IRQ_CODE1.2 (1Q)
irq_vector_1: IC130.2 (D2), IRQ_CODE1.5 (2Q), IRQ_RST_DECODER1.1 (A)
irq_vector_2: IC134.2 (D2), IRQ_CODE1.6 (3Q), IRQ_RST_DECODER1.2 (B)
irq_vector_3: IC138.2 (D2), IRQ_CODE1.9 (4Q), IRQ_RST_DECODER1.3 (C)
irq_vector_4: IC144.2 (D2), IRQ_CODE1.12 (5Q)
irq_vector_5: IC148.2 (D2), IRQ_CODE1.15 (6Q)
irq_vector_6: IC152.2 (D2), IRQ_CODE1.16 (7Q)
irq_vector_7: IC167.2 (D2), IRQ_CODE1.19 (8Q)
irq_vector_wrt: IRQ_CODE1.1 (G)
ksph0: IC93.2 (1Q), IC126.3 (D1)
ksph1: IC93.5 (2Q), IC130.3 (D1)
ksph2: IC93.6 (3Q), IC134.3 (D1)
ksph3: IC93.9 (4Q), IC138.3 (D1)
ksph4: IC93.12 (5Q), IC144.3 (D1)
ksph5: IC93.15 (6Q), IC148.3 (D1)
ksph6: IC93.16 (7Q), IC152.3 (D1)
ksph7: IC93.19 (8Q), IC167.3 (D1)
kspl0: IC90.2 (1Q), IC126.4 (D0)
kspl1: IC90.5 (2Q), IC130.4 (D0)
kspl2: IC90.6 (3Q), IC134.4 (D0)
kspl3: IC90.9 (4Q), IC138.4 (D0)
kspl4: IC90.12 (5Q), IC144.4 (D0)
kspl5: IC90.15 (6Q), IC148.4 (D0)
kspl6: IC90.16 (7Q), IC152.4 (D0)
kspl7: IC90.19 (8Q), IC167.4 (D0)
mar_in_src: IC181.1 (~A/B), IC182.1 (~A/B), IC183.1 (~A/B), IC184.1 (~A/B)
marh_0: IC118.2 (A1), IC125.1 (D3), MARH1.2 (1Q)
marh_1: IC118.4 (A2), IC129.1 (D3), MARH1.5 (2Q)
marh_2: IC118.6 (A3), IC133.1 (D3), MARH1.6 (3Q)
marh_3: IC137.1 (D3), IC157.2 (1A), IC163.10 (A0), IC177.10 (A0), MARH1.9 (4Q)
marh_4: IC143.1 (D3), IC157.5 (2A), IC163.9 (A1), IC177.9 (A1), MARH1.12 (5Q)
marh_5: IC147.1 (D3), IC157.11 (3A), IC163.8 (A2), IC177.8 (A2), MARH1.15 (6Q)
marh_6: IC151.1 (D3), IC157.14 (4A), IC163.7 (A3), IC177.7 (A3), MARH1.16 (7Q)
marh_7: IC158.2 (1A), IC163.6 (A4), IC166.1 (D3), IC177.6 (A4), MARH1.19 (8Q)
marh_wrt: MARH1.1 (G)
marl_0: IC117.2 (A1), IC125.2 (D2), MARL1.2 (1Q)
marl_1: IC117.4 (A2), IC129.2 (D2), MARL1.5 (2Q)
marl_2: IC117.6 (A3), IC133.2 (D2), MARL1.6 (3Q)
marl_3: IC117.8 (A4), IC137.2 (D2), MARL1.9 (4Q)
marl_4: IC117.11 (A1), IC143.2 (D2), MARL1.12 (5Q)
marl_5: IC117.13 (A2), IC147.2 (D2), MARL1.15 (6Q)
marl_6: IC117.15 (A3), IC151.2 (D2), MARL1.16 (7Q)
marl_7: IC117.17 (A4), IC166.2 (D2), MARL1.19 (8Q)
marl_wrt: MARL1.1 (G)
mdr_in_src: MDR_IN_MUX_1.1 (~A/B), MDR_IN_MUX_2.1 (~A/B)
mdr_out_en: U19.1
mdr_out_src: MDR_OUT_MUX_1.1 (~A/B), MDR_OUT_MUX_2.1 (~A/B)
mdr_to_pagetable_buffer_en: IC43.9 (I), IC163.22 (~OE), IC177.22 (~OE)
mdrh_0: IC125.14 (D5), IC179.2 (A1), MDRH1.2 (1Q), MDR_OUT_MUX_1.3 (1B)
mdrh_1: IC129.14 (D5), IC179.4 (A2), MDRH1.5 (2Q), MDR_OUT_MUX_1.6 (2B)
mdrh_2: IC133.14 (D5), IC179.6 (A3), MDRH1.6 (3Q), MDR_OUT_MUX_1.10 (3B)
mdrh_3: IC137.14 (D5), IC179.8 (A4), MDRH1.9 (4Q), MDR_OUT_MUX_1.13 (4B)
mdrh_4: IC143.14 (D5), IC179.11 (A1), MDRH1.12 (5Q), MDR_OUT_MUX_2.3 (1B)
mdrh_5: IC147.14 (D5), IC179.13 (A2), MDRH1.15 (6Q), MDR_OUT_MUX_2.6 (2B)
mdrh_6: IC151.14 (D5), IC179.15 (A3), MDRH1.16 (7Q), MDR_OUT_MUX_2.10 (3B)
mdrh_7: IC166.14 (D5), IC179.17 (A4), MDRH1.19 (8Q), MDR_OUT_MUX_2.13 (4B)
mdrh_wrt: MDRH1.1 (G)
mdrl_0: IC125.15 (D4), IC178.2 (A1), MDRL1.2 (1Q), MDR_OUT_MUX_1.2 (1A)
mdrl_1: IC129.15 (D4), IC178.4 (A2), MDRL1.5 (2Q), MDR_OUT_MUX_1.5 (2A)
mdrl_2: IC133.15 (D4), IC178.6 (A3), MDRL1.6 (3Q), MDR_OUT_MUX_1.11 (3A)
mdrl_3: IC137.15 (D4), IC178.8 (A4), MDRL1.9 (4Q), MDR_OUT_MUX_1.14 (4A)
mdrl_4: IC143.15 (D4), IC178.11 (A1), MDRL1.12 (5Q), MDR_OUT_MUX_2.2 (1A)
mdrl_5: IC147.15 (D4), IC178.13 (A2), MDRL1.15 (6Q), MDR_OUT_MUX_2.5 (2A)
mdrl_6: IC151.15 (D4), IC178.15 (A3), MDRL1.16 (7Q), MDR_OUT_MUX_2.11 (3A)
mdrl_7: IC166.15 (D4), IC178.17 (A4), MDRL1.19 (8Q), MDR_OUT_MUX_2.14 (4A)
mdrl_wrt: MDRL1.1 (G)
page_present: IC119.3 (Y4)
page_table_addr_source: IC180.1 (~A/B), IC190.1 (~A/B)
page_table_we: IC113.9 (I)
page_writeable: IC120.18 (Y1)
panel_regsel_0: IC111.2 (1A)
panel_regsel_1: IC111.5 (2A)
panel_regsel_2: IC111.11 (3A)
panel_regsel_3: IC111.14 (4A)
panel_regsel_4: IC112.2 (1A)
pch0: IC62.2 (1Q), IC125.3 (D1), IC183.3 (1B)
pch1: IC62.5 (2Q), IC129.3 (D1), IC183.6 (2B)
pch2: IC62.6 (3Q), IC133.3 (D1), IC183.10 (3B)
pch3: IC62.9 (4Q), IC137.3 (D1), IC183.13 (4B)
pch4: IC62.12 (5Q), IC143.3 (D1), IC184.3 (1B)
pch5: IC62.15 (6Q), IC147.3 (D1), IC184.6 (2B)
pch6: IC62.16 (7Q), IC151.3 (D1), IC184.10 (3B)
pch7: IC62.19 (8Q), IC166.3 (D1), IC184.13 (4B)
pch_wrt: IC62.1 (G)
pcl0: IC61.2 (1Q), IC125.4 (D0), IC181.3 (1B)
pcl1: IC61.5 (2Q), IC129.4 (D0), IC181.6 (2B)
pcl2: IC61.6 (3Q), IC133.4 (D0), IC181.10 (3B)
pcl3: IC61.9 (4Q), IC137.4 (D0), IC181.13 (4B)
pcl4: IC61.12 (5Q), IC143.4 (D0), IC182.3 (1B)
pcl5: IC61.15 (6Q), IC147.4 (D0), IC182.6 (2B)
pcl6: IC61.16 (7Q), IC151.4 (D0), IC182.10 (3B)
pcl7: IC61.19 (8Q), IC166.4 (D0), IC182.13 (4B)
pcl_wrt: IC61.1 (G)
ptb_wrt: IC191.1 (G)
sih0: IC74.2 (1Q), IC124.14 (D5)
sih1: IC74.5 (2Q), IC128.14 (D5)
sih2: IC74.6 (3Q), IC132.14 (D5)
sih3: IC74.9 (4Q), IC136.14 (D5)
sih4: IC74.12 (5Q), IC142.14 (D5)
sih5: IC74.15 (6Q), IC146.14 (D5)
sih6: IC74.16 (7Q), IC150.14 (D5)
sih7: IC74.19 (8Q), IC154.14 (D5)
sih_wrt: IC74.1 (G)
sil0: IC73.2 (1Q), IC124.15 (D4)
sil1: IC73.5 (2Q), IC128.15 (D4)
sil2: IC73.6 (3Q), IC132.15 (D4)
sil3: IC73.9 (4Q), IC136.15 (D4)
sil4: IC73.12 (5Q), IC142.15 (D4)
sil5: IC73.15 (6Q), IC146.15 (D4)
sil6: IC73.16 (7Q), IC150.15 (D4)
sil7: IC73.19 (8Q), IC154.15 (D4)
sil_wrt: IC73.1 (G)
sph0: IC64.2 (1Q), IC124.3 (D1)
sph1: IC64.5 (2Q), IC128.3 (D1)
sph2: IC64.6 (3Q), IC132.3 (D1)
sph3: IC64.9 (4Q), IC136.3 (D1)
sph4: IC64.12 (5Q), IC142.3 (D1)
sph5: IC64.15 (6Q), IC146.3 (D1)
sph6: IC64.16 (7Q), IC150.3 (D1)
sph7: IC64.19 (8Q), IC154.3 (D1)
sph_wrt: IC64.1 (G), IC70.5 (I1)
spl0: IC63.2 (1Q), IC124.4 (D0)
spl1: IC63.5 (2Q), IC128.4 (D0)
spl2: IC63.6 (3Q), IC132.4 (D0)
spl3: IC63.9 (4Q), IC136.4 (D0)
spl4: IC63.12 (5Q), IC142.4 (D0)
spl5: IC63.15 (6Q), IC146.4 (D0)
spl6: IC63.16 (7Q), IC150.4 (D0)
spl7: IC63.19 (8Q), IC154.4 (D0)
spl_wrt: IC63.1 (G), IC70.2 (I1)
status_cpu_mode: IC70.1 (I0), IC70.4 (I0)
status_paging_en: IC157.1 (~A/B), IC158.1 (~A/B), IC159.1 (~A/B), IC160.1 (~A/B)
tdrh0: IC87.2 (1Q), IC125.12 (D7)
tdrh1: IC87.5 (2Q), IC129.12 (D7)
tdrh2: IC87.6 (3Q), IC133.12 (D7)
tdrh3: IC87.9 (4Q), IC137.12 (D7)
tdrh4: IC87.12 (5Q), IC143.12 (D7)
tdrh5: IC87.15 (6Q), IC147.12 (D7)
tdrh6: IC87.16 (7Q), IC151.12 (D7)
tdrh7: IC87.19 (8Q), IC166.12 (D7)
tdrh_wrt: IC87.1 (G)
tdrl0: IC85.2 (1Q), IC125.13 (D6)
tdrl1: IC85.5 (2Q), IC129.13 (D6)
tdrl2: IC85.6 (3Q), IC133.13 (D6)
tdrl3: IC85.9 (4Q), IC137.13 (D6)
tdrl4: IC85.12 (5Q), IC143.13 (D6)
tdrl5: IC85.15 (6Q), IC147.13 (D6)
tdrl6: IC85.16 (7Q), IC151.13 (D6)
tdrl7: IC85.19 (8Q), IC166.13 (D6)
tdrl_wrt: IC85.1 (G)
vcc: IC159.14 (4A), IC160.2 (1A), IC160.5 (2A), IC163.28 (VCC), IC177.28 (VCC), IRQ_0_DFF1.2 (D), IRQ_0_DFF1.4 (PRE), IRQ_0_DFF1.10 (PRE), IRQ_0_DFF1.12 (D), IRQ_1_DFF1.2 (D), IRQ_1_DFF1.4 (PRE), IRQ_1_DFF1.10 (PRE), IRQ_1_DFF1.12 (D), IRQ_2_DFF1.2 (D), IRQ_2_DFF1.4 (PRE), IRQ_2_DFF1.10 (PRE), IRQ_2_DFF1.12 (D), IRQ_3_DFF1.2 (D), IRQ_3_DFF1.4 (PRE), IRQ_3_DFF1.10 (PRE), IRQ_3_DFF1.12 (D), IRQ_STATUS_1.1 (CLR)
w0: IC139.7 (1Y)
w1: IC139.9 (2Y)
w2: IC140.7 (1Y)
w3: IC140.9 (2Y)
w4: IC168.7 (1Y)
w5: IC168.9 (2Y)
w6: IC169.7 (1Y)
w7: IC169.9 (2Y)
zbus0: IC53.3 (1D), IC54.3 (1D), IC55.3 (1D), IC56.3 (1D), IC57.3 (1D), IC58.3 (1D), IC59.3 (1D), IC60.3 (1D), IC61.3 (1D), IC62.3 (1D), IC63.3 (1D), IC64.3 (1D), IC71.3 (1D), IC72.3 (1D), IC73.3 (1D), IC74.3 (1D), IC75.3 (1D), IC84.3 (1D), IC85.3 (1D), IC87.3 (1D), IC88.3 (1D), IC90.3 (1D), IC93.3 (1D), IC181.2 (1A), IC183.2 (1A), IC191.3 (1D), MDR_IN_MUX_1.2 (1A)
zbus1: IC53.4 (2D), IC54.4 (2D), IC55.4 (2D), IC56.4 (2D), IC57.4 (2D), IC58.4 (2D), IC59.4 (2D), IC60.4 (2D), IC61.4 (2D), IC62.4 (2D), IC63.4 (2D), IC64.4 (2D), IC71.4 (2D), IC72.4 (2D), IC73.4 (2D), IC74.4 (2D), IC75.4 (2D), IC84.4 (2D), IC85.4 (2D), IC87.4 (2D), IC88.4 (2D), IC90.4 (2D), IC93.4 (2D), IC181.5 (2A), IC183.5 (2A), IC191.4 (2D), MDR_IN_MUX_1.5 (2A)
zbus2: IC53.7 (3D), IC54.7 (3D), IC55.7 (3D), IC56.7 (3D), IC57.7 (3D), IC58.7 (3D), IC59.7 (3D), IC60.7 (3D), IC61.7 (3D), IC62.7 (3D), IC63.7 (3D), IC64.7 (3D), IC71.7 (3D), IC72.7 (3D), IC73.7 (3D), IC74.7 (3D), IC75.7 (3D), IC84.7 (3D), IC85.7 (3D), IC87.7 (3D), IC88.7 (3D), IC90.7 (3D), IC93.7 (3D), IC181.11 (3A), IC183.11 (3A), IC191.7 (3D), MDR_IN_MUX_1.11 (3A)
zbus3: IC53.8 (4D), IC54.8 (4D), IC55.8 (4D), IC56.8 (4D), IC57.8 (4D), IC58.8 (4D), IC59.8 (4D), IC60.8 (4D), IC61.8 (4D), IC62.8 (4D), IC63.8 (4D), IC64.8 (4D), IC71.8 (4D), IC72.8 (4D), IC73.8 (4D), IC74.8 (4D), IC75.8 (4D), IC84.8 (4D), IC85.8 (4D), IC87.8 (4D), IC88.8 (4D), IC90.8 (4D), IC93.8 (4D), IC181.14 (4A), IC183.14 (4A), IC191.8 (4D), MDR_IN_MUX_1.14 (4A)
zbus4: IC53.13 (5D), IC54.13 (5D), IC55.13 (5D), IC56.13 (5D), IC57.13 (5D), IC58.13 (5D), IC59.13 (5D), IC60.13 (5D), IC61.13 (5D), IC62.13 (5D), IC63.13 (5D), IC64.13 (5D), IC71.13 (5D), IC72.13 (5D), IC73.13 (5D), IC74.13 (5D), IC75.13 (5D), IC84.13 (5D), IC85.13 (5D), IC87.13 (5D), IC88.13 (5D), IC90.13 (5D), IC93.13 (5D), IC182.2 (1A), IC184.2 (1A), IC191.13 (5D), MDR_IN_MUX_2.2 (1A)
zbus5: IC53.14 (6D), IC54.14 (6D), IC55.14 (6D), IC56.14 (6D), IC57.14 (6D), IC58.14 (6D), IC59.14 (6D), IC60.14 (6D), IC61.14 (6D), IC62.14 (6D), IC63.14 (6D), IC64.14 (6D), IC71.14 (6D), IC72.14 (6D), IC73.14 (6D), IC74.14 (6D), IC75.14 (6D), IC84.14 (6D), IC85.14 (6D), IC87.14 (6D), IC88.14 (6D), IC90.14 (6D), IC93.14 (6D), IC182.5 (2A), IC184.5 (2A), IC191.14 (6D), MDR_IN_MUX_2.5 (2A)
zbus6: IC53.17 (7D), IC54.17 (7D), IC55.17 (7D), IC56.17 (7D), IC57.17 (7D), IC58.17 (7D), IC59.17 (7D), IC60.17 (7D), IC61.17 (7D), IC62.17 (7D), IC63.17 (7D), IC64.17 (7D), IC71.17 (7D), IC72.17 (7D), IC73.17 (7D), IC74.17 (7D), IC75.17 (7D), IC84.17 (7D), IC85.17 (7D), IC87.17 (7D), IC88.17 (7D), IC90.17 (7D), IC93.17 (7D), IC182.11 (3A), IC184.11 (3A), IC191.17 (7D), MDR_IN_MUX_2.11 (3A)
zbus7: IC53.18 (8D), IC54.18 (8D), IC55.18 (8D), IC56.18 (8D), IC57.18 (8D), IC58.18 (8D), IC59.18 (8D), IC60.18 (8D), IC61.18 (8D), IC62.18 (8D), IC63.18 (8D), IC64.18 (8D), IC71.18 (8D), IC72.18 (8D), IC73.18 (8D), IC74.18 (8D), IC75.18 (8D), IC84.18 (8D), IC85.18 (8D), IC87.18 (8D), IC88.18 (8D), IC90.18 (8D), IC93.18 (8D), IC182.14 (4A), IC184.14 (4A), IC191.18 (8D), MDR_IN_MUX_2.14 (4A)
~clear_all_irqs: IC43.2 (O), IRQ_AND_1.1 (I0), IRQ_AND_1.4 (I0), IRQ_AND_1.5 (I1), IRQ_AND_1.9 (I0), IRQ_AND_1.10 (I1), IRQ_AND_1.12 (I0), IRQ_AND_1.13 (I1), IRQ_AND_2.1 (I0), IRQ_AND_2.2 (I1), IRQ_AND_2.4 (I0), IRQ_AND_2.5 (I1), IRQ_AND_2.9 (I0), IRQ_AND_2.10 (I1), IRQ_AND_2.12 (I0), IRQ_AND_2.13 (I1), IRQ_RST_DECODER1.7 (Y7), IRQ_RST_DECODER1.9 (Y6), IRQ_RST_DECODER1.10 (Y5), IRQ_RST_DECODER1.11 (Y4), IRQ_RST_DECODER1.12 (Y3), IRQ_RST_DECODER1.13 (Y2), IRQ_RST_DECODER1.14 (Y1)

Notes on the sheet:
marl
dil
bpl
bph
244 microcode signals need inverter because they get reset to zero at beginning, and 244 are low active. this causes problems on reset.
this comes from the microcode board but is not a control bit. it is a combination of two bits.
irq masks
dih
ptb
pcl
spl
sih
tdr
pch
mdr mux
sil
might want to feed the external data bus directly into mar as well via a multiplexer. this is to speed-up ram operations
sph
marh
sspl
mdr
ssph
