stanley-fork/sol-1/ccompiler/out/startrek.asm

; --- FILENAME: games/startrek.c
; --- DATE:     08-07-2025 at 11:41:51
.include "lib/asm/kernel.exp"
.include "lib/asm/bios.exp"

; --- BEGIN TEXT SEGMENT
.org text_org
main:
  mov bp, $FFE0 ;
  mov sp, $FFE0 ; Make space for argc(2 bytes) and for 10 pointers in argv (local variables)
; intro(); 
; --- START FUNCTION CALL
  call intro
; new_game(); 
; --- START FUNCTION CALL
  call new_game
; return 0; 
  mov32 cb, $00000000
  leave
  syscall sys_terminate_proc

TO_FIXED:
  enter 0 ; (push bp; mov bp, sp)
; return x * 10; 
  lea d, [bp + 5] ; $x
  mov b, [d]
  mov c, 0
; --- START FACTORS
  push a
  push g
  mov a, b
  mov g, c
  mov32 cb, $0000000a
  push a     ; save left operand
  xor a, b   ; xor sign bits
  swp a      ; swap bytes
  mov cl, al ; save result of xor into 'dl'
  pop a      ; restore left side operator
  push cl    ; save result of xor above
  swp a  
  test al, $80  
  swp a  
  jz skip_invert_a_2  
  neg a 
skip_invert_a_2:   
  swp b
  test bl, $80  
  swp b
  jz skip_invert_b_2  
  neg b 
skip_invert_b_2:   
  mul a, b ; *
  mov g, a
  mov a, b
  pop bl
  test bl, $80
  jz _same_signs_2
  mov bl, al
  not a
  neg b
  adc a, 0
  mov g, a
  mov a, b
_same_signs_2:
  mov c, g
  mov b, a
  pop g
  pop a
; --- END FACTORS
  leave
  ret

FROM_FIXED:
  enter 0 ; (push bp; mov bp, sp)
; return x / 10; 
  lea d, [bp + 5] ; $x
  mov b, [d]
  mov c, 0
; --- START FACTORS
  push a
  push g
  mov a, b
  mov g, c
  mov32 cb, $0000000a
  push g ; save 'g' as the div instruction uses it
  div a, b ; /, a: quotient, b: remainder
  pop g
  mov c, g
  mov b, a
  pop g
  pop a
; --- END FACTORS
  leave
  ret

TO_FIXED00:
  enter 0 ; (push bp; mov bp, sp)
; return x * 100; 
  lea d, [bp + 5] ; $x
  mov b, [d]
  mov c, 0
; --- START FACTORS
  push a
  push g
  mov a, b
  mov g, c
  mov32 cb, $00000064
  push a     ; save left operand
  xor a, b   ; xor sign bits
  swp a      ; swap bytes
  mov cl, al ; save result of xor into 'dl'
  pop a      ; restore left side operator
  push cl    ; save result of xor above
  swp a  
  test al, $80  
  swp a  
  jz skip_invert_a_6  
  neg a 
skip_invert_a_6:   
  swp b
  test bl, $80  
  swp b
  jz skip_invert_b_6  
  neg b 
skip_invert_b_6:   
  mul a, b ; *
  mov g, a
  mov a, b
  pop bl
  test bl, $80
  jz _same_signs_6
  mov bl, al
  not a
  neg b
  adc a, 0
  mov g, a
  mov a, b
_same_signs_6:
  mov c, g
  mov b, a
  pop g
  pop a
; --- END FACTORS
  leave
  ret

FROM_FIXED00:
  enter 0 ; (push bp; mov bp, sp)
; return x / 100; 
  lea d, [bp + 5] ; $x
  mov b, [d]
  mov c, 0
; --- START FACTORS
  push a
  push g
  mov a, b
  mov g, c
  mov32 cb, $00000064
  push g ; save 'g' as the div instruction uses it
  div a, b ; /, a: quotient, b: remainder
  pop g
  mov c, g
  mov b, a
  pop g
  pop a
; --- END FACTORS
  leave
  ret

get_rand:
  enter 0 ; (push bp; mov bp, sp)
; unsigned int         r ; 
  sub sp, 2
; r = rand(); 
  lea d, [bp + -1] ; $r
  push d
; --- START FUNCTION CALL
  call rand
  pop d
  mov [d], b
; r = (r >> 8) | (r << 8); 
  lea d, [bp + -1] ; $r
  push d
  lea d, [bp + -1] ; $r
  mov b, [d]
  mov c, 0
; --- START SHIFT
  push a
  mov a, b
  mov32 cb, $00000008
  mov c, b
  shr a, cl
  mov b, a
  pop a
; --- END SHIFT
  push a
  mov a, b
  lea d, [bp + -1] ; $r
  mov b, [d]
  mov c, 0
; --- START SHIFT
  push a
  mov a, b
  mov32 cb, $00000008
  mov c, b
  shl a, cl
  mov b, a
  pop a
; --- END SHIFT
  or b, a ; |
  pop a
  pop d
  mov [d], b
; return ((r % spread) + 1); 
  lea d, [bp + -1] ; $r
  mov b, [d]
  mov c, 0
; --- START FACTORS
  push a
  push g
  mov a, b
  mov g, c
  lea d, [bp + 5] ; $spread
  mov b, [d]
  mov c, 0
  push g ; save 'g' as the div instruction uses it
  div a, b ; %, a: quotient, b: remainder
  mov a, b
  pop g
  mov c, g
  mov b, a
  pop g
  pop a
; --- END FACTORS
; --- START TERMS
  push a
  mov a, b
  mov32 cb, $00000001
  add b, a
  pop a
; --- END TERMS
  leave
  ret

rand8:
  enter 0 ; (push bp; mov bp, sp)
; return (get_rand(8)); 
; --- START FUNCTION CALL
  mov32 cb, $00000008
  swp b
  push b
  call get_rand
  add sp, 2
; --- END FUNCTION CALL
  leave
  ret

input:
  enter 0 ; (push bp; mov bp, sp)
; int c; 
  sub sp, 2
; while((c = getchar()) != '\n') { 
_while17_cond:
  lea d, [bp + -1] ; $c
  push d
; --- START FUNCTION CALL
  call getchar
  pop d
  mov [d], b
; --- START RELATIONAL
  push a
  mov a, b
  mov32 cb, $0000000a
  cmp a, b
  sneq ; !=
  pop a
; --- END RELATIONAL
  cmp b, 0
  je _while17_exit
_while17_block:
; if (c == -1) 
_if18_cond:
  lea d, [bp + -1] ; $c
  mov b, [d]
  mov c, 0
; --- START RELATIONAL
  push a
  mov a, b
  mov32 cb, $ffffffff
  cmp a, b
  seq ; ==
  pop a
; --- END RELATIONAL
  cmp b, 0
  je _if18_exit
_if18_TRUE:
; exit(1); 
; --- START FUNCTION CALL
  mov32 cb, $00000001
  swp b
  push b
  call exit
  add sp, 2
; --- END FUNCTION CALL
  jmp _if18_exit
_if18_exit:
; if (l > 1) { 
_if19_cond:
  lea d, [bp + 7] ; $l
  mov bl, [d]
  mov bh, 0
  mov c, 0
; --- START RELATIONAL
  push a
  mov a, b
  mov32 cb, $00000001
  cmp a, b
  sgu ; > (unsigned)
  pop a
; --- END RELATIONAL
  cmp b, 0
  je _if19_exit
_if19_TRUE:
; *b++ = c; 
  lea d, [bp + 5] ; $b
  mov b, [d]
  mov c, 0
  inc b
  lea d, [bp + 5] ; $b
  mov [d], b
  dec b
  push b
  lea d, [bp + -1] ; $c
  mov b, [d]
  mov c, 0
  pop d
  mov [d], bl
; l--; 
  lea d, [bp + 7] ; $l
  mov bl, [d]
  mov bh, 0
  mov c, 0
  dec b
  lea d, [bp + 7] ; $l
  mov [d], bl
  inc b
  jmp _if19_exit
_if19_exit:
  jmp _while17_cond
_while17_exit:
; *b = 0; 
  lea d, [bp + 5] ; $b
  mov b, [d]
  mov c, 0
  push b
  mov32 cb, $00000000
  pop d
  mov [d], bl
  leave
  ret

yesno:
  enter 0 ; (push bp; mov bp, sp)
; char b[2]; 
  sub sp, 2
; input(b,2); 
; --- START FUNCTION CALL
  mov32 cb, $00000002
  push bl
  lea d, [bp + -1] ; $b
  mov b, d
  mov c, 0
  swp b
  push b
  call input
  add sp, 3
; --- END FUNCTION CALL
; tolower(*b); 
; --- START FUNCTION CALL
  lea d, [bp + -1] ; $b
  mov b, d
  mov c, 0
  mov d, b
  mov bl, [d]
  mov bh, 0
  mov c, 0
  push bl
  call tolower
  add sp, 1
; --- END FUNCTION CALL
; return 1; 
  mov32 cb, $00000001
  leave
  ret
; return 0; 
  mov32 cb, $00000000
  leave
  ret

input_f00:
  enter 0 ; (push bp; mov bp, sp)
; int        v; 
  sub sp, 2
; char buf[8]; 
  sub sp, 8
; char *x; 
  sub sp, 2
; input(buf, 8); 
; --- START FUNCTION CALL
  mov32 cb, $00000008
  push bl
  lea d, [bp + -9] ; $buf
  mov b, d
  mov c, 0
  swp b
  push b
  call input
  add sp, 3
; --- END FUNCTION CALL
; x = buf; 
  lea d, [bp + -11] ; $x
  push d
  lea d, [bp + -9] ; $buf
  mov b, d
  mov c, 0
  pop d
  mov [d], b
; if (!is_digit(*x)) 
_if20_cond:
; --- START FUNCTION CALL
  lea d, [bp + -11] ; $x
  mov b, [d]
  mov c, 0
  mov d, b
  mov bl, [d]
  mov bh, 0
  mov c, 0
  push bl
  call is_digit
  add sp, 1
; --- END FUNCTION CALL
  cmp b, 0
  je _if20_exit
_if20_TRUE:
; return -1; 
  mov32 cb, $ffffffff
  leave
  ret
  jmp _if20_exit
_if20_exit:
; v = 100 * (*x++ - '0'); 
  lea d, [bp + -1] ; $v
  push d
  mov32 cb, $00000064
; --- START FACTORS
  push a
  push g
  mov a, b
  mov g, c
  lea d, [bp + -11] ; $x
  mov b, [d]
  mov c, 0
  inc b
  lea d, [bp + -11] ; $x
  mov [d], b
  dec b
  mov d, b
  mov bl, [d]
  mov bh, 0
  mov c, 0
; --- START TERMS
  push a
  mov a, b
  mov32 cb, $00000030
  sub a, b
  mov b, a
  pop a
; --- END TERMS
  push a     ; save left operand
  xor a, b   ; xor sign bits
  swp a      ; swap bytes
  mov cl, al ; save result of xor into 'dl'
  pop a      ; restore left side operator
  push cl    ; save result of xor above
  swp a  
  test al, $80  
  swp a  
  jz skip_invert_a_22  
  neg a 
skip_invert_a_22:   
  swp b
  test bl, $80  
  swp b
  jz skip_invert_b_22  
  neg b 
skip_invert_b_22:   
  mul a, b ; *
  mov g, a
  mov a, b
  pop bl
  test bl, $80
  jz _same_signs_22
  mov bl, al
  not a
  neg b
  adc a, 0
  mov g, a
  mov a, b
_same_signs_22:
  mov c, g
  mov b, a
  pop g
  pop a
; --- END FACTORS
  pop d
  mov [d], b
; if (*x == 0) 
_if23_cond:
  lea d, [bp + -11] ; $x
  mov b, [d]
  mov c, 0
  mov d, b
  mov bl, [d]
  mov bh, 0
  mov c, 0
; --- START RELATIONAL
  push a
  mov a, b
  mov32 cb, $00000000
  cmp a, b
  seq ; ==
  pop a
; --- END RELATIONAL
  cmp b, 0
  je _if23_exit
_if23_TRUE:
; return v; 
  lea d, [bp + -1] ; $v
  mov b, [d]
  mov c, 0
  leave
  ret
  jmp _if23_exit
_if23_exit:
; if (*x++ != '.') 
_if24_cond:
  lea d, [bp + -11] ; $x
  mov b, [d]
  mov c, 0
  inc b
  lea d, [bp + -11] ; $x
  mov [d], b
  dec b
  mov d, b
  mov bl, [d]
  mov bh, 0
  mov c, 0
; --- START RELATIONAL
  push a
  mov a, b
  mov32 cb, $0000002e
  cmp a, b
  sneq ; !=
  pop a
; --- END RELATIONAL
  cmp b, 0
  je _if24_exit
_if24_TRUE:
; return -1; 
  mov32 cb, $ffffffff
  leave
  ret
  jmp _if24_exit
_if24_exit:
; if (!is_digit(*x)) 
_if25_cond:
; --- START FUNCTION CALL
  lea d, [bp + -11] ; $x
  mov b, [d]
  mov c, 0
  mov d, b
  mov bl, [d]
  mov bh, 0
  mov c, 0
  push bl
  call is_digit
  add sp, 1
; --- END FUNCTION CALL
  cmp b, 0
  je _if25_exit
_if25_TRUE:
; return -1; 
  mov32 cb, $ffffffff
  leave
  ret
  jmp _if25_exit
_if25_exit:
; v = v + 10 * (*x++ - '0'); 
  lea d, [bp + -1] ; $v
  push d
  lea d, [bp + -1] ; $v
  mov b, [d]
  mov c, 0
; --- START TERMS
  push a
  mov a, b
  mov32 cb, $0000000a
; --- START FACTORS
  push a
  push g
  mov a, b
  mov g, c
  lea d, [bp + -11] ; $x
  mov b, [d]
  mov c, 0
  inc b
  lea d, [bp + -11] ; $x
  mov [d], b
  dec b
  mov d, b
  mov bl, [d]
  mov bh, 0
  mov c, 0
; --- START TERMS
  push a
  mov a, b
  mov32 cb, $00000030
  sub a, b
  mov b, a
  pop a
; --- END TERMS
  push a     ; save left operand
  xor a, b   ; xor sign bits
  swp a      ; swap bytes
  mov cl, al ; save result of xor into 'dl'
  pop a      ; restore left side operator
  push cl    ; save result of xor above
  swp a  
  test al, $80  
  swp a  
  jz skip_invert_a_27  
  neg a 
skip_invert_a_27:   
  swp b
  test bl, $80  
  swp b
  jz skip_invert_b_27  
  neg b 
skip_invert_b_27:   
  mul a, b ; *
  mov g, a
  mov a, b
  pop bl
  test bl, $80
  jz _same_signs_27
  mov bl, al
  not a
  neg b
  adc a, 0
  mov g, a
  mov a, b
_same_signs_27:
  mov c, g
  mov b, a
  pop g
  pop a
; --- END FACTORS
  add b, a
  pop a
; --- END TERMS
  pop d
  mov [d], b
; if (!*x) 
_if28_cond:
  lea d, [bp + -11] ; $x
  mov b, [d]
  mov c, 0
  mov d, b
  mov bl, [d]
  mov bh, 0
  mov c, 0
  cmp b, 0
  seq ; !
  cmp b, 0
  je _if28_exit
_if28_TRUE:
; return v; 
  lea d, [bp + -1] ; $v
  mov b, [d]
  mov c, 0
  leave
  ret
  jmp _if28_exit
_if28_exit:
; if (!is_digit(*x)) 
_if29_cond:
; --- START FUNCTION CALL
  lea d, [bp + -11] ; $x
  mov b, [d]
  mov c, 0
  mov d, b
  mov bl, [d]
  mov bh, 0
  mov c, 0
  push bl
  call is_digit
  add sp, 1
; --- END FUNCTION CALL
  cmp b, 0
  je _if29_exit
_if29_TRUE:
; return -1; 
  mov32 cb, $ffffffff
  leave
  ret
  jmp _if29_exit
_if29_exit:
; v = v + *x++ - '0'; 
  lea d, [bp + -1] ; $v
  push d
  lea d, [bp + -1] ; $v
  mov b, [d]
  mov c, 0
; --- START TERMS
  push a
  mov a, b
  lea d, [bp + -11] ; $x
  mov b, [d]
  mov c, 0
  inc b
  lea d, [bp + -11] ; $x
  mov [d], b
  dec b
  mov d, b
  mov bl, [d]
  mov bh, 0
  mov c, 0
  add b, a
  mov a, b
  mov32 cb, $00000030
  sub a, b
  mov b, a
  pop a
; --- END TERMS
  pop d
  mov [d], b
; return v; 
  lea d, [bp + -1] ; $v
  mov b, [d]
  mov c, 0
  leave
  ret

input_int:
  enter 0 ; (push bp; mov bp, sp)
; char x[8]; 
  sub sp, 8
; input(x, 8); 
; --- START FUNCTION CALL
  mov32 cb, $00000008
  push bl
  lea d, [bp + -7] ; $x
  mov b, d
  mov c, 0
  swp b
  push b
  call input
  add sp, 3
; --- END FUNCTION CALL
; if (!is_digit(*x)) 
_if30_cond:
; --- START FUNCTION CALL
  lea d, [bp + -7] ; $x
  mov b, d
  mov c, 0
  mov d, b
  mov bl, [d]
  mov bh, 0
  mov c, 0
  push bl
  call is_digit
  add sp, 1
; --- END FUNCTION CALL
  cmp b, 0
  je _if30_exit
_if30_TRUE:
; return -1; 
  mov32 cb, $ffffffff
  leave
  ret
  jmp _if30_exit
_if30_exit:
; return atoi(x); 
; --- START FUNCTION CALL
  lea d, [bp + -7] ; $x
  mov b, d
  mov c, 0
  swp b
  push b
  call atoi
  add sp, 2
; --- END FUNCTION CALL
  leave
  ret

print100:
  enter 0 ; (push bp; mov bp, sp)
; static char buf[16]; 
  sub sp, 16
; char *p; 
  sub sp, 2
; *p = buf; 
  lea d, [bp + -1] ; $p
  mov b, [d]
  mov c, 0
  push b
  mov d, st_print100_buf_dt ; static buf
  mov b, d
  mov c, 0
  pop d
  mov [d], bl
; if (v < 0) { 
_if31_cond:
  lea d, [bp + 5] ; $v
  mov b, [d]
  mov c, 0
; --- START RELATIONAL
  push a
  mov a, b
  mov32 cb, $00000000
  cmp a, b
  slt ; < (signed)
  pop a
; --- END RELATIONAL
  cmp b, 0
  je _if31_exit
_if31_TRUE:
; v = -v; 
  lea d, [bp + 5] ; $v
  push d
  lea d, [bp + 5] ; $v
  mov b, [d]
  mov c, 0
  neg b
  pop d
  mov [d], b
; *p++ = '-'; 
  lea d, [bp + -1] ; $p
  mov b, [d]
  mov c, 0
  inc b
  lea d, [bp + -1] ; $p
  mov [d], b
  dec b
  push b
  mov32 cb, $0000002d
  pop d
  mov [d], bl
  jmp _if31_exit
_if31_exit:
; return buf; 
  mov d, st_print100_buf_dt ; static buf
  mov b, d
  mov c, 0
  leave
  ret

inoperable:
  enter 0 ; (push bp; mov bp, sp)
; if (damage[u] < 0) { 
_if32_cond:
  mov d, _damage_data ; $damage
  push a
  push d
  lea d, [bp + 5] ; $u
  mov bl, [d]
  mov bh, 0
  mov c, 0
  pop d
  mma 2 ; mov a, 2; mul a, b; add d, b
  pop a
  mov b, [d]
  mov c, 0
; --- START RELATIONAL
  push a
  mov a, b
  mov32 cb, $00000000
  cmp a, b
  slt ; < (signed)
  pop a
; --- END RELATIONAL
  cmp b, 0
  je _if32_exit
_if32_TRUE:
; printf("%s %s inoperable.\n", 
; --- START FUNCTION CALL
_ternary34_cond:
  lea d, [bp + 5] ; $u
  mov bl, [d]
  mov bh, 0
  mov c, 0
; --- START RELATIONAL
  push a
  mov a, b
  mov32 cb, $00000005
  cmp a, b
  seq ; ==
  pop a
; --- END RELATIONAL
  cmp b, 0
  je _ternary34_FALSE
_ternary34_TRUE:
  mov b, _s30 ; "are"
  jmp _ternary34_exit
_ternary34_FALSE:
  mov b, _s31 ; "is"
_ternary34_exit:
  swp b
  push b
; --- START FUNCTION CALL
  lea d, [bp + 5] ; $u
  mov bl, [d]
  mov bh, 0
  mov c, 0
  snex b
  swp b
  push b
  call get_device_name
  add sp, 2
; --- END FUNCTION CALL
  swp b
  push b
  mov b, _s32 ; "%s %s inoperable.\n"
  swp b
  push b
  call printf
  add sp, 6
; --- END FUNCTION CALL
; return 1; 
  mov32 cb, $00000001
  leave
  ret
  jmp _if32_exit
_if32_exit:
; return 0; 
  mov32 cb, $00000000
  leave
  ret

intro:
  enter 0 ; (push bp; mov bp, sp)
; showfile("startrek.intro"); 
; --- START FUNCTION CALL
  mov b, _s33 ; "startrek.intro"
  swp b
  push b
  call showfile
  add sp, 2
; --- END FUNCTION CALL
; if (yesno()) 
_if35_cond:
; --- START FUNCTION CALL
  call yesno
  cmp b, 0
  je _if35_exit
_if35_TRUE:
; showfile("startrek.doc"); 
; --- START FUNCTION CALL
  mov b, _s34 ; "startrek.doc"
  swp b
  push b
  call showfile
  add sp, 2
; --- END FUNCTION CALL
  jmp _if35_exit
_if35_exit:
; showfile("startrek.logo"); 
; --- START FUNCTION CALL
  mov b, _s35 ; "startrek.logo"
  swp b
  push b
  call showfile
  add sp, 2
; --- END FUNCTION CALL
; stardate = TO_FIXED((get_rand(20) + 20) * 100); 
  mov d, _stardate ; $stardate
  push d
; --- START FUNCTION CALL
; --- START FUNCTION CALL
  mov32 cb, $00000014
  swp b
  push b
  call get_rand
  add sp, 2
; --- END FUNCTION CALL
; --- START TERMS
  push a
  mov a, b
  mov32 cb, $00000014
  add b, a
  pop a
; --- END TERMS
; --- START FACTORS
  push a
  push g
  mov a, b
  mov g, c
  mov32 cb, $00000064
  push a     ; save left operand
  xor a, b   ; xor sign bits
  swp a      ; swap bytes
  mov cl, al ; save result of xor into 'dl'
  pop a      ; restore left side operator
  push cl    ; save result of xor above
  swp a  
  test al, $80  
  swp a  
  jz skip_invert_a_39  
  neg a 
skip_invert_a_39:   
  swp b
  test bl, $80  
  swp b
  jz skip_invert_b_39  
  neg b 
skip_invert_b_39:   
  mul a, b ; *
  mov g, a
  mov a, b
  pop bl
  test bl, $80
  jz _same_signs_39
  mov bl, al
  not a
  neg b
  adc a, 0
  mov g, a
  mov a, b
_same_signs_39:
  mov c, g
  mov b, a
  pop g
  pop a
; --- END FACTORS
  swp b
  push b
  call TO_FIXED
  add sp, 2
; --- END FUNCTION CALL
  pop d
  mov [d], b
  leave
  ret

new_game:
  enter 0 ; (push bp; mov bp, sp)
; char cmd[4]; 
  sub sp, 4
; initialize(); 
; --- START FUNCTION CALL
  call initialize
; new_quadrant(); 
; --- START FUNCTION CALL
  call new_quadrant
; short_range_scan(); 
; --- START FUNCTION CALL
  call short_range_scan
; while (1) { 
_while40_cond:
  mov32 cb, $00000001
  cmp b, 0
  je _while40_exit
_while40_block:
; if (shield + energy <= 10 && (energy < 10 || damage[7] < 0)) { 
_if41_cond:
  mov d, _shield ; $shield
  mov b, [d]
  mov c, 0
; --- START TERMS
  push a
  mov a, b
  mov d, _energy ; $energy
  mov b, [d]
  mov c, 0
  add b, a
  pop a
; --- END TERMS
; --- START RELATIONAL
  push a
  mov a, b
  mov32 cb, $0000000a
  cmp a, b
  sle ; <= (signed)
  pop a
; --- END RELATIONAL
; --- START LOGICAL AND
  push a
  mov a, b
  mov d, _energy ; $energy
  mov b, [d]
  mov c, 0
; --- START RELATIONAL
  push a
  mov a, b
  mov32 cb, $0000000a
  cmp a, b
  slt ; < (signed)
  pop a
; --- END RELATIONAL
; --- START LOGICAL OR
  push a
  mov a, b
  mov d, _damage_data ; $damage
  push a
  push d
  mov32 cb, $00000007
  pop d
  mma 2 ; mov a, 2; mul a, b; add d, b
  pop a
  mov b, [d]
  mov c, 0
; --- START RELATIONAL
  push a
  mov a, b
  mov32 cb, $00000000
  cmp a, b
  slt ; < (signed)
  pop a
; --- END RELATIONAL
  sor a, b ; ||
  pop a
; --- END LOGICAL OR
  sand a, b
  pop a
; --- END LOGICAL AND
  cmp b, 0
  je _if41_exit
_if41_TRUE:
; showfile("startrek.fatal"); 
; --- START FUNCTION CALL
  mov b, _s36 ; "startrek.fatal"
  swp b
  push b
  call showfile
  add sp, 2
; --- END FUNCTION CALL
; end_of_time(); 
; --- START FUNCTION CALL
  call end_of_time
  jmp _if41_exit
_if41_exit:
; puts("Command? "); 
; --- START FUNCTION CALL
  mov b, _s37 ; "Command? "
  swp b
  push b
  call puts
  add sp, 2
; --- END FUNCTION CALL
; input(cmd, 4); 
; --- START FUNCTION CALL
  mov32 cb, $00000004
  push bl
  lea d, [bp + -3] ; $cmd
  mov b, d
  mov c, 0
  swp b
  push b
  call input
  add sp, 3
; --- END FUNCTION CALL
; putchar('\n'); 
; --- START FUNCTION CALL
  mov32 cb, $0000000a
  push bl
  call putchar
  add sp, 1
; --- END FUNCTION CALL
; if (!strncmp(cmd, "nav", 3)) 
_if42_cond:
; --- START FUNCTION CALL
  mov32 cb, $00000003
  swp b
  push b
  mov b, _s38 ; "nav"
  swp b
  push b
  lea d, [bp + -3] ; $cmd
  mov b, d
  mov c, 0
  swp b
  push b
  call strncmp
  add sp, 6
; --- END FUNCTION CALL
  cmp b, 0
  je _if42_else
_if42_TRUE:
; course_control(); 
; --- START FUNCTION CALL
  call course_control
  jmp _if42_exit
_if42_else:
; if (!strncmp(cmd, "srs", 3)) 
_if43_cond:
; --- START FUNCTION CALL
  mov32 cb, $00000003
  swp b
  push b
  mov b, _s39 ; "srs"
  swp b
  push b
  lea d, [bp + -3] ; $cmd
  mov b, d
  mov c, 0
  swp b
  push b
  call strncmp
  add sp, 6
; --- END FUNCTION CALL
  cmp b, 0
  je _if43_else
_if43_TRUE:
; short_range_scan(); 
; --- START FUNCTION CALL
  call short_range_scan
  jmp _if43_exit
_if43_else:
; if (!strncmp(cmd, "lrs", 3)) 
_if44_cond:
; --- START FUNCTION CALL
  mov32 cb, $00000003
  swp b
  push b
  mov b, _s40 ; "lrs"
  swp b
  push b
  lea d, [bp + -3] ; $cmd
  mov b, d
  mov c, 0
  swp b
  push b
  call strncmp
  add sp, 6
; --- END FUNCTION CALL
  cmp b, 0
  je _if44_else
_if44_TRUE:
; long_range_scan(); 
; --- START FUNCTION CALL
  call long_range_scan
  jmp _if44_exit
_if44_else:
; if (!strncmp(cmd, "pha", 3)) 
_if45_cond:
; --- START FUNCTION CALL
  mov32 cb, $00000003
  swp b
  push b
  mov b, _s41 ; "pha"
  swp b
  push b
  lea d, [bp + -3] ; $cmd
  mov b, d
  mov c, 0
  swp b
  push b
  call strncmp
  add sp, 6
; --- END FUNCTION CALL
  cmp b, 0
  je _if45_else
_if45_TRUE:
; phaser_control(); 
; --- START FUNCTION CALL
  call phaser_control
  jmp _if45_exit
_if45_else:
; if (!strncmp(cmd, "tor", 3)) 
_if46_cond:
; --- START FUNCTION CALL
  mov32 cb, $00000003
  swp b
  push b
  mov b, _s42 ; "tor"
  swp b
  push b
  lea d, [bp + -3] ; $cmd
  mov b, d
  mov c, 0
  swp b
  push b
  call strncmp
  add sp, 6
; --- END FUNCTION CALL
  cmp b, 0
  je _if46_else
_if46_TRUE:
; photon_torpedoes(); 
; --- START FUNCTION CALL
  call photon_torpedoes
  jmp _if46_exit
_if46_else:
; if (!strncmp(cmd, "shi", 3)) 
_if47_cond:
; --- START FUNCTION CALL
  mov32 cb, $00000003
  swp b
  push b
  mov b, _s43 ; "shi"
  swp b
  push b
  lea d, [bp + -3] ; $cmd
  mov b, d
  mov c, 0
  swp b
  push b
  call strncmp
  add sp, 6
; --- END FUNCTION CALL
  cmp b, 0
  je _if47_else
_if47_TRUE:
; shield_control(); 
; --- START FUNCTION CALL
  call shield_control
  jmp _if47_exit
_if47_else:
; if (!strncmp(cmd, "dam", 3)) 
_if48_cond:
; --- START FUNCTION CALL
  mov32 cb, $00000003
  swp b
  push b
  mov b, _s44 ; "dam"
  swp b
  push b
  lea d, [bp + -3] ; $cmd
  mov b, d
  mov c, 0
  swp b
  push b
  call strncmp
  add sp, 6
; --- END FUNCTION CALL
  cmp b, 0
  je _if48_else
_if48_TRUE:
; damage_control(); 
; --- START FUNCTION CALL
  call damage_control
  jmp _if48_exit
_if48_else:
; if (!strncmp(cmd, "com", 3)) 
_if49_cond:
; --- START FUNCTION CALL
  mov32 cb, $00000003
  swp b
  push b
  mov b, _s45 ; "com"
  swp b
  push b
  lea d, [bp + -3] ; $cmd
  mov b, d
  mov c, 0
  swp b
  push b
  call strncmp
  add sp, 6
; --- END FUNCTION CALL
  cmp b, 0
  je _if49_else
_if49_TRUE:
; library_computer(); 
; --- START FUNCTION CALL
  call library_computer
  jmp _if49_exit
_if49_else:
; if (!strncmp(cmd, "xxx", 3)) 
_if50_cond:
; --- START FUNCTION CALL
  mov32 cb, $00000003
  swp b
  push b
  mov b, _s46 ; "xxx"
  swp b
  push b
  lea d, [bp + -3] ; $cmd
  mov b, d
  mov c, 0
  swp b
  push b
  call strncmp
  add sp, 6
; --- END FUNCTION CALL
  cmp b, 0
  je _if50_else
_if50_TRUE:
; resign_commision(); 
; --- START FUNCTION CALL
  call resign_commision
  jmp _if50_exit
_if50_else:
; puts("Enter one of the following:\n"); 
; --- START FUNCTION CALL
  mov b, _s47 ; "Enter one of the following:\n"
  swp b
  push b
  call puts
  add sp, 2
; --- END FUNCTION CALL
; puts("  nav - To Set Course"); 
; --- START FUNCTION CALL
  mov b, _s48 ; "  nav - To Set Course"
  swp b
  push b
  call puts
  add sp, 2
; --- END FUNCTION CALL
; puts("  srs - Short Range Sensors"); 
; --- START FUNCTION CALL
  mov b, _s49 ; "  srs - Short Range Sensors"
  swp b
  push b
  call puts
  add sp, 2
; --- END FUNCTION CALL
; puts("  lrs - Long Range Sensors"); 
; --- START FUNCTION CALL
  mov b, _s50 ; "  lrs - Long Range Sensors"
  swp b
  push b
  call puts
  add sp, 2
; --- END FUNCTION CALL
; puts("  pha - Phasers"); 
; --- START FUNCTION CALL
  mov b, _s51 ; "  pha - Phasers"
  swp b
  push b
  call puts
  add sp, 2
; --- END FUNCTION CALL
; puts("  tor - Photon Torpedoes"); 
; --- START FUNCTION CALL
  mov b, _s52 ; "  tor - Photon Torpedoes"
  swp b
  push b
  call puts
  add sp, 2
; --- END FUNCTION CALL
; puts("  shi - Shield Control"); 
; --- START FUNCTION CALL
  mov b, _s53 ; "  shi - Shield Control"
  swp b
  push b
  call puts
  add sp, 2
; --- END FUNCTION CALL
; puts("  dam - Damage Control"); 
; --- START FUNCTION CALL
  mov b, _s54 ; "  dam - Damage Control"
  swp b
  push b
  call puts
  add sp, 2
; --- END FUNCTION CALL
; puts("  com - Library Computer"); 
; --- START FUNCTION CALL
  mov b, _s55 ; "  com - Library Computer"
  swp b
  push b
  call puts
  add sp, 2
; --- END FUNCTION CALL
; puts("  xxx - Resign Command\n"); 
; --- START FUNCTION CALL
  mov b, _s56 ; "  xxx - Resign Command\n"
  swp b
  push b
  call puts
  add sp, 2
; --- END FUNCTION CALL
_if50_exit:
_if49_exit:
_if48_exit:
_if47_exit:
_if46_exit:
_if45_exit:
_if44_exit:
_if43_exit:
_if42_exit:
  jmp _while40_cond
_while40_exit:
  leave
  ret

initialize:
  enter 0 ; (push bp; mov bp, sp)
; int i, j; 
  sub sp, 2
  sub sp, 2
; unsigned char        yp, xp; 
  sub sp, 1
  sub sp, 1
; unsigned char        r; 
  sub sp, 1
; time_start = FROM_FIXED(stardate); 
  mov d, _time_start ; $time_start
  push d
; --- START FUNCTION CALL
  mov d, _stardate ; $stardate
  mov b, [d]
  mov c, 0
  swp b
  push b
  call FROM_FIXED
  add sp, 2
; --- END FUNCTION CALL
  pop d
  mov [d], b
; time_up = 25 + get_rand(10); 
  mov d, _time_up ; $time_up
  push d
  mov32 cb, $00000019
; --- START TERMS
  push a
  mov a, b
; --- START FUNCTION CALL
  mov32 cb, $0000000a
  swp b
  push b
  call get_rand
  add sp, 2
; --- END FUNCTION CALL
  add b, a
  pop a
; --- END TERMS
  pop d
  mov [d], b
; docked = 0; 
  mov d, _docked ; $docked
  push d
  mov32 cb, $00000000
  pop d
  mov [d], bl
; energy = energy0; 
  mov d, _energy ; $energy
  push d
  mov d, _energy0 ; $energy0
  mov b, [d]
  mov c, 0
  pop d
  mov [d], b
; torps = torps0; 
  mov d, _torps ; $torps
  push d
  mov d, _torps0 ; $torps0
  mov bl, [d]
  mov bh, 0
  mov c, 0
  pop d
  mov [d], bl
; shield = 0; 
  mov d, _shield ; $shield
  push d
  mov32 cb, $00000000
  pop d
  mov [d], b
; quad_y = rand8(); 
  mov d, _quad_y ; $quad_y
  push d
; --- START FUNCTION CALL
  call rand8
  pop d
  mov [d], b
; quad_x = rand8(); 
  mov d, _quad_x ; $quad_x
  push d
; --- START FUNCTION CALL
  call rand8
  pop d
  mov [d], b
; ship_y = TO_FIXED00(rand8()); 
  mov d, _ship_y ; $ship_y
  push d
; --- START FUNCTION CALL
; --- START FUNCTION CALL
  call rand8
  snex b
  swp b
  push b
  call TO_FIXED00
  add sp, 2
; --- END FUNCTION CALL
  pop d
  mov [d], b
; ship_x = TO_FIXED00(rand8()); 
  mov d, _ship_x ; $ship_x
  push d
; --- START FUNCTION CALL
; --- START FUNCTION CALL
  call rand8
  snex b
  swp b
  push b
  call TO_FIXED00
  add sp, 2
; --- END FUNCTION CALL
  pop d
  mov [d], b
; for (i = 1; i <= 8; i++) 
_for51_init:
  lea d, [bp + -1] ; $i
  push d
  mov32 cb, $00000001
  pop d
  mov [d], b
_for51_cond:
  lea d, [bp + -1] ; $i
  mov b, [d]
  mov c, 0
; --- START RELATIONAL
  push a
  mov a, b
  mov32 cb, $00000008
  cmp a, b
  sle ; <= (signed)
  pop a
; --- END RELATIONAL
  cmp b, 0
  je _for51_exit
_for51_block:
; damage[i] = 0; 
  mov d, _damage_data ; $damage
  push a
  push d
  lea d, [bp + -1] ; $i
  mov b, [d]
  mov c, 0
  pop d
  mma 2 ; mov a, 2; mul a, b; add d, b
  pop a
  push d
  mov32 cb, $00000000
  pop d
  mov [d], b
_for51_update:
  lea d, [bp + -1] ; $i
  mov b, [d]
  mov c, 0
  mov a, b
  inc b
  lea d, [bp + -1] ; $i
  mov [d], b
  mov b, a
  jmp _for51_cond
_for51_exit:
; for (i = 1; i <= 8; i++) { 
_for52_init:
  lea d, [bp + -1] ; $i
  push d
  mov32 cb, $00000001
  pop d
  mov [d], b
_for52_cond:
  lea d, [bp + -1] ; $i
  mov b, [d]
  mov c, 0
; --- START RELATIONAL
  push a
  mov a, b
  mov32 cb, $00000008
  cmp a, b
  sle ; <= (signed)
  pop a
; --- END RELATIONAL
  cmp b, 0
  je _for52_exit
_for52_block:
; for (j = 1; j <= 8; j++) { 
_for53_init:
  lea d, [bp + -3] ; $j
  push d
  mov32 cb, $00000001
  pop d
  mov [d], b
_for53_cond:
  lea d, [bp + -3] ; $j
  mov b, [d]
  mov c, 0
; --- START RELATIONAL
  push a
  mov a, b
  mov32 cb, $00000008
  cmp a, b
  sle ; <= (signed)
  pop a
; --- END RELATIONAL
  cmp b, 0
  je _for53_exit
_for53_block:
; r = get_rand(100); 
  lea d, [bp + -6] ; $r
  push d
; --- START FUNCTION CALL
  mov32 cb, $00000064
  swp b
  push b
  call get_rand
  add sp, 2
; --- END FUNCTION CALL
  pop d
  mov [d], bl
; klingons = 0; 
  mov d, _klingons ; $klingons
  push d
  mov32 cb, $00000000
  pop d
  mov [d], bl
; if (r > 98) 
_if54_cond:
  lea d, [bp + -6] ; $r
  mov bl, [d]
  mov bh, 0
  mov c, 0
; --- START RELATIONAL
  push a
  mov a, b
  mov32 cb, $00000062
  cmp a, b
  sgu ; > (unsigned)
  pop a
; --- END RELATIONAL
  cmp b, 0
  je _if54_else
_if54_TRUE:
; klingons = 3; 
  mov d, _klingons ; $klingons
  push d
  mov32 cb, $00000003
  pop d
  mov [d], bl
  jmp _if54_exit
_if54_else:
; if (r > 95) 
_if55_cond:
  lea d, [bp + -6] ; $r
  mov bl, [d]
  mov bh, 0
  mov c, 0
; --- START RELATIONAL
  push a
  mov a, b
  mov32 cb, $0000005f
  cmp a, b
  sgu ; > (unsigned)
  pop a
; --- END RELATIONAL
  cmp b, 0
  je _if55_else
_if55_TRUE:
; klingons = 2; 
  mov d, _klingons ; $klingons
  push d
  mov32 cb, $00000002
  pop d
  mov [d], bl
  jmp _if55_exit
_if55_else:
; if (r > 80) 
_if56_cond:
  lea d, [bp + -6] ; $r
  mov bl, [d]
  mov bh, 0
  mov c, 0
; --- START RELATIONAL
  push a
  mov a, b
  mov32 cb, $00000050
  cmp a, b
  sgu ; > (unsigned)
  pop a
; --- END RELATIONAL
  cmp b, 0
  je _if56_exit
_if56_TRUE:
; klingons = 1; 
  mov d, _klingons ; $klingons
  push d
  mov32 cb, $00000001
  pop d
  mov [d], bl
  jmp _if56_exit
_if56_exit:
_if55_exit:
_if54_exit:
; klingons_left = klingons_left + klingons; 
  mov d, _klingons_left ; $klingons_left
  push d
  mov d, _klingons_left ; $klingons_left
  mov bl, [d]
  mov bh, 0
  mov c, 0
; --- START TERMS
  push a
  mov a, b
  mov d, _klingons ; $klingons
  mov bl, [d]
  mov bh, 0
  mov c, 0
  add b, a
  pop a
; --- END TERMS
  pop d
  mov [d], bl
; starbases = 0; 
  mov d, _starbases ; $starbases
  push d
  mov32 cb, $00000000
  pop d
  mov [d], bl
; if (get_rand(100) > 96) 
_if57_cond:
; --- START FUNCTION CALL
  mov32 cb, $00000064
  swp b
  push b
  call get_rand
  add sp, 2
; --- END FUNCTION CALL
; --- START RELATIONAL
  push a
  mov a, b
  mov32 cb, $00000060
  cmp a, b
  sgt ; >
  pop a
; --- END RELATIONAL
  cmp b, 0
  je _if57_exit
_if57_TRUE:
; starbases = 1; 
  mov d, _starbases ; $starbases
  push d
  mov32 cb, $00000001
  pop d
  mov [d], bl
  jmp _if57_exit
_if57_exit:
; starbases_left = starbases_left + starbases; 
  mov d, _starbases_left ; $starbases_left
  push d
  mov d, _starbases_left ; $starbases_left
  mov bl, [d]
  mov bh, 0
  mov c, 0
; --- START TERMS
  push a
  mov a, b
  mov d, _starbases ; $starbases
  mov bl, [d]
  mov bh, 0
  mov c, 0
  add b, a
  pop a
; --- END TERMS
  pop d
  mov [d], bl
; map[i][j] = (klingons << 8) + (starbases << 4) + rand8(); 
  mov d, _map_data ; $map
  push a
  push d
  lea d, [bp + -1] ; $i
  mov b, [d]
  mov c, 0
  pop d
  mma 18 ; mov a, 18; mul a, b; add d, b
  push d
  lea d, [bp + -3] ; $j
  mov b, [d]
  mov c, 0
  pop d
  mma 2 ; mov a, 2; mul a, b; add d, b
  pop a
  push d
  mov d, _klingons ; $klingons
  mov bl, [d]
  mov bh, 0
  mov c, 0
; --- START SHIFT
  push a
  mov a, b
  mov32 cb, $00000008
  mov c, b
  shl a, cl
  mov b, a
  pop a
; --- END SHIFT
; --- START TERMS
  push a
  mov a, b
  mov d, _starbases ; $starbases
  mov bl, [d]
  mov bh, 0
  mov c, 0
; --- START SHIFT
  push a
  mov a, b
  mov32 cb, $00000004
  mov c, b
  shl a, cl
  mov b, a
  pop a
; --- END SHIFT
  add b, a
  mov a, b
; --- START FUNCTION CALL
  call rand8
  add b, a
  pop a
; --- END TERMS
  pop d
  mov [d], b
_for53_update:
  lea d, [bp + -3] ; $j
  mov b, [d]
  mov c, 0
  mov a, b
  inc b
  lea d, [bp + -3] ; $j
  mov [d], b
  mov b, a
  jmp _for53_cond
_for53_exit:
_for52_update:
  lea d, [bp + -1] ; $i
  mov b, [d]
  mov c, 0
  mov a, b
  inc b
  lea d, [bp + -1] ; $i
  mov [d], b
  mov b, a
  jmp _for52_cond
_for52_exit:
; if (klingons_left > time_up) 
_if58_cond:
  mov d, _klingons_left ; $klingons_left
  mov bl, [d]
  mov bh, 0
  mov c, 0
; --- START RELATIONAL
  push a
  mov a, b
  mov d, _time_up ; $time_up
  mov b, [d]
  mov c, 0
  cmp a, b
  sgu ; > (unsigned)
  pop a
; --- END RELATIONAL
  cmp b, 0
  je _if58_exit
_if58_TRUE:
; time_up = klingons_left + 1; 
  mov d, _time_up ; $time_up
  push d
  mov d, _klingons_left ; $klingons_left
  mov bl, [d]
  mov bh, 0
  mov c, 0
; --- START TERMS
  push a
  mov a, b
  mov32 cb, $00000001
  add b, a
  pop a
; --- END TERMS
  pop d
  mov [d], b
  jmp _if58_exit
_if58_exit:
; if (starbases_left == 0) { 
_if59_cond:
  mov d, _starbases_left ; $starbases_left
  mov bl, [d]
  mov bh, 0
  mov c, 0
; --- START RELATIONAL
  push a
  mov a, b
  mov32 cb, $00000000
  cmp a, b
  seq ; ==
  pop a
; --- END RELATIONAL
  cmp b, 0
  je _if59_exit
_if59_TRUE:
; yp = rand8(); 
  lea d, [bp + -4] ; $yp
  push d
; --- START FUNCTION CALL
  call rand8
  pop d
  mov [d], bl
; xp = rand8(); 
  lea d, [bp + -5] ; $xp
  push d
; --- START FUNCTION CALL
  call rand8
  pop d
  mov [d], bl
; if (map[yp][xp] < 0x200) { 
_if60_cond:
  mov d, _map_data ; $map
  push a
  push d
  lea d, [bp + -4] ; $yp
  mov bl, [d]
  mov bh, 0
  mov c, 0
  pop d
  mma 18 ; mov a, 18; mul a, b; add d, b
  push d
  lea d, [bp + -5] ; $xp
  mov bl, [d]
  mov bh, 0
  mov c, 0
  pop d
  mma 2 ; mov a, 2; mul a, b; add d, b
  pop a
  mov b, [d]
  mov c, 0
; --- START RELATIONAL
  push a
  mov a, b
  mov32 cb, $00000200
  cmp a, b
  slu ; < (unsigned)
  pop a
; --- END RELATIONAL
  cmp b, 0
  je _if60_exit
_if60_TRUE:
; map[yp][xp] = map[yp][xp] + (1 << 8); 
  mov d, _map_data ; $map
  push a
  push d
  lea d, [bp + -4] ; $yp
  mov bl, [d]
  mov bh, 0
  mov c, 0
  pop d
  mma 18 ; mov a, 18; mul a, b; add d, b
  push d
  lea d, [bp + -5] ; $xp
  mov bl, [d]
  mov bh, 0
  mov c, 0
  pop d
  mma 2 ; mov a, 2; mul a, b; add d, b
  pop a
  push d
  mov d, _map_data ; $map
  push a
  push d
  lea d, [bp + -4] ; $yp
  mov bl, [d]
  mov bh, 0
  mov c, 0
  pop d
  mma 18 ; mov a, 18; mul a, b; add d, b
  push d
  lea d, [bp + -5] ; $xp
  mov bl, [d]
  mov bh, 0
  mov c, 0
  pop d
  mma 2 ; mov a, 2; mul a, b; add d, b
  pop a
  mov b, [d]
  mov c, 0
; --- START TERMS
  push a
  mov a, b
  mov32 cb, $00000001
; --- START SHIFT
  push a
  mov a, b
  mov32 cb, $00000008
  mov c, b
  shl a, cl
  mov b, a
  pop a
; --- END SHIFT
  add b, a
  pop a
; --- END TERMS
  pop d
  mov [d], b
; klingons_left++; 
  mov d, _klingons_left ; $klingons_left
  mov bl, [d]
  mov bh, 0
  mov c, 0
  inc b
  mov d, _klingons_left ; $klingons_left
  mov [d], bl
  dec b
  jmp _if60_exit
_if60_exit:
; map[yp][xp] = map[yp][xp] + (1 << 4); 
  mov d, _map_data ; $map
  push a
  push d
  lea d, [bp + -4] ; $yp
  mov bl, [d]
  mov bh, 0
  mov c, 0
  pop d
  mma 18 ; mov a, 18; mul a, b; add d, b
  push d
  lea d, [bp + -5] ; $xp
  mov bl, [d]
  mov bh, 0
  mov c, 0
  pop d
  mma 2 ; mov a, 2; mul a, b; add d, b
  pop a
  push d
  mov d, _map_data ; $map
  push a
  push d
  lea d, [bp + -4] ; $yp
  mov bl, [d]
  mov bh, 0
  mov c, 0
  pop d
  mma 18 ; mov a, 18; mul a, b; add d, b
  push d
  lea d, [bp + -5] ; $xp
  mov bl, [d]
  mov bh, 0
  mov c, 0
  pop d
  mma 2 ; mov a, 2; mul a, b; add d, b
  pop a
  mov b, [d]
  mov c, 0
; --- START TERMS
  push a
  mov a, b
  mov32 cb, $00000001
; --- START SHIFT
  push a
  mov a, b
  mov32 cb, $00000004
  mov c, b
  shl a, cl
  mov b, a
  pop a
; --- END SHIFT
  add b, a
  pop a
; --- END TERMS
  pop d
  mov [d], b
; starbases_left++; 
  mov d, _starbases_left ; $starbases_left
  mov bl, [d]
  mov bh, 0
  mov c, 0
  inc b
  mov d, _starbases_left ; $starbases_left
  mov [d], bl
  dec b
  jmp _if59_exit
_if59_exit:
; total_klingons = klingons_left; 
  mov d, _total_klingons ; $total_klingons
  push d
  mov d, _klingons_left ; $klingons_left
  mov bl, [d]
  mov bh, 0
  mov c, 0
  pop d
  mov [d], bl
; if (starbases_left != 1) { 
_if61_cond:
  mov d, _starbases_left ; $starbases_left
  mov bl, [d]
  mov bh, 0
  mov c, 0
; --- START RELATIONAL
  push a
  mov a, b
  mov32 cb, $00000001
  cmp a, b
  sneq ; !=
  pop a
; --- END RELATIONAL
  cmp b, 0
  je _if61_exit
_if61_TRUE:
; strcpy(plural_2, "s"); 
; --- START FUNCTION CALL
  mov b, _s57 ; "s"
  swp b
  push b
  mov d, _plural_2_data ; $plural_2
  mov b, d
  mov c, 0
  swp b
  push b
  call strcpy
  add sp, 4
; --- END FUNCTION CALL
; strcpy(plural, "are"); 
; --- START FUNCTION CALL
  mov b, _s30 ; "are"
  swp b
  push b
  mov d, _plural_data ; $plural
  mov b, d
  mov c, 0
  swp b
  push b
  call strcpy
  add sp, 4
; --- END FUNCTION CALL
  jmp _if61_exit
_if61_exit:
; getchar(); 
; --- START FUNCTION CALL
  call getchar
  leave
  ret

place_ship:
  enter 0 ; (push bp; mov bp, sp)
; quad[FROM_FIXED00(ship_y) - 1][FROM_FIXED00(ship_x) - 1] = 		4      ; 
  mov d, _quad_data ; $quad
  push a
  push d
; --- START FUNCTION CALL
  mov d, _ship_y ; $ship_y
  mov b, [d]
  mov c, 0
  swp b
  push b
  call FROM_FIXED00
  add sp, 2
; --- END FUNCTION CALL
; --- START TERMS
  push a
  mov a, b
  mov32 cb, $00000001
  sub a, b
  mov b, a
  pop a
; --- END TERMS
  pop d
  mma 8 ; mov a, 8; mul a, b; add d, b
  push d
; --- START FUNCTION CALL
  mov d, _ship_x ; $ship_x
  mov b, [d]
  mov c, 0
  swp b
  push b
  call FROM_FIXED00
  add sp, 2
; --- END FUNCTION CALL
; --- START TERMS
  push a
  mov a, b
  mov32 cb, $00000001
  sub a, b
  mov b, a
  pop a
; --- END TERMS
  pop d
  add d, b
  pop a
  push d
  mov32 cb, $00000004
  pop d
  mov [d], bl
  leave
  ret

new_quadrant:
  enter 0 ; (push bp; mov bp, sp)
; int i; 
  sub sp, 2
; unsigned int         tmp; 
  sub sp, 2
; struct klingon *k; 
  sub sp, 2
; k = &kdata; 
  lea d, [bp + -5] ; $k
  push d
  mov d, _kdata_data ; $kdata
  mov b, d
  pop d
  mov [d], b
; klingons = 0; 
  mov d, _klingons ; $klingons
  push d
  mov32 cb, $00000000
  pop d
  mov [d], bl
; starbases = 0; 
  mov d, _starbases ; $starbases
  push d
  mov32 cb, $00000000
  pop d
  mov [d], bl
; stars = 0; 
  mov d, _stars ; $stars
  push d
  mov32 cb, $00000000
  pop d
  mov [d], bl
; d4 = get_rand(50) - 1; 
  mov d, _d4 ; $d4
  push d
; --- START FUNCTION CALL
  mov32 cb, $00000032
  swp b
  push b
  call get_rand
  add sp, 2
; --- END FUNCTION CALL
; --- START TERMS
  push a
  mov a, b
  mov32 cb, $00000001
  sub a, b
  mov b, a
  pop a
; --- END TERMS
  pop d
  mov [d], b
; map[quad_y][quad_x] = map[quad_y][quad_x] |  0x1000		           ; 
  mov d, _map_data ; $map
  push a
  push d
  mov d, _quad_y ; $quad_y
  mov b, [d]
  mov c, 0
  pop d
  mma 18 ; mov a, 18; mul a, b; add d, b
  push d
  mov d, _quad_x ; $quad_x
  mov b, [d]
  mov c, 0
  pop d
  mma 2 ; mov a, 2; mul a, b; add d, b
  pop a
  push d
  mov d, _map_data ; $map
  push a
  push d
  mov d, _quad_y ; $quad_y
  mov b, [d]
  mov c, 0
  pop d
  mma 18 ; mov a, 18; mul a, b; add d, b
  push d
  mov d, _quad_x ; $quad_x
  mov b, [d]
  mov c, 0
  pop d
  mma 2 ; mov a, 2; mul a, b; add d, b
  pop a
  mov b, [d]
  mov c, 0
  push a
  mov a, b
  mov32 cb, $00001000
  or b, a ; |
  pop a
  pop d
  mov [d], b
; if (quad_y >= 1 && quad_y <= 8 && quad_x >= 1 && quad_x <= 8) { 
_if62_cond:
  mov d, _quad_y ; $quad_y
  mov b, [d]
  mov c, 0
; --- START RELATIONAL
  push a
  mov a, b
  mov32 cb, $00000001
  cmp a, b
  sge ; >=
  pop a
; --- END RELATIONAL
; --- START LOGICAL AND
  push a
  mov a, b
  mov d, _quad_y ; $quad_y
  mov b, [d]
  mov c, 0
; --- START RELATIONAL
  push a
  mov a, b
  mov32 cb, $00000008
  cmp a, b
  sle ; <= (signed)
  pop a
; --- END RELATIONAL
  sand a, b
  mov a, b
  mov d, _quad_x ; $quad_x
  mov b, [d]
  mov c, 0
; --- START RELATIONAL
  push a
  mov a, b
  mov32 cb, $00000001
  cmp a, b
  sge ; >=
  pop a
; --- END RELATIONAL
  sand a, b
  mov a, b
  mov d, _quad_x ; $quad_x
  mov b, [d]
  mov c, 0
; --- START RELATIONAL
  push a
  mov a, b
  mov32 cb, $00000008
  cmp a, b
  sle ; <= (signed)
  pop a
; --- END RELATIONAL
  sand a, b
  pop a
; --- END LOGICAL AND
  cmp b, 0
  je _if62_exit
_if62_TRUE:
; quadrant_name(0, quad_y, quad_x); 
; --- START FUNCTION CALL
  mov d, _quad_x ; $quad_x
  mov b, [d]
  mov c, 0
  push bl
  mov d, _quad_y ; $quad_y
  mov b, [d]
  mov c, 0
  push bl
  mov32 cb, $00000000
  push bl
  call quadrant_name
  add sp, 3
; --- END FUNCTION CALL
; if (TO_FIXED(time_start) != stardate) 
_if63_cond:
; --- START FUNCTION CALL
  mov d, _time_start ; $time_start
  mov b, [d]
  mov c, 0
  swp b
  push b
  call TO_FIXED
  add sp, 2
; --- END FUNCTION CALL
; --- START RELATIONAL
  push a
  mov a, b
  mov d, _stardate ; $stardate
  mov b, [d]
  mov c, 0
  cmp a, b
  sneq ; !=
  pop a
; --- END RELATIONAL
  cmp b, 0
  je _if63_else
_if63_TRUE:
; printf("Now entering %s quadrant...\n\n", quadname); 
; --- START FUNCTION CALL
  mov d, _quadname_data ; $quadname
  mov b, d
  mov c, 0
  swp b
  push b
  mov b, _s58 ; "Now entering %s quadrant...\n\n"
  swp b
  push b
  call printf
  add sp, 4
; --- END FUNCTION CALL
  jmp _if63_exit
_if63_else:
; puts("\nYour mission begins with your starship located"); 
; --- START FUNCTION CALL
  mov b, _s59 ; "\nYour mission begins with your starship located"
  swp b
  push b
  call puts
  add sp, 2
; --- END FUNCTION CALL
; printf("in the galactic quadrant %s.\n\n", quadname); 
; --- START FUNCTION CALL
  mov d, _quadname_data ; $quadname
  mov b, d
  mov c, 0
  swp b
  push b
  mov b, _s60 ; "in the galactic quadrant %s.\n\n"
  swp b
  push b
  call printf
  add sp, 4
; --- END FUNCTION CALL
_if63_exit:
  jmp _if62_exit
_if62_exit:
; tmp = map[quad_y][quad_x]; 
  lea d, [bp + -3] ; $tmp
  push d
  mov d, _map_data ; $map
  push a
  push d
  mov d, _quad_y ; $quad_y
  mov b, [d]
  mov c, 0
  pop d
  mma 18 ; mov a, 18; mul a, b; add d, b
  push d
  mov d, _quad_x ; $quad_x
  mov b, [d]
  mov c, 0
  pop d
  mma 2 ; mov a, 2; mul a, b; add d, b
  pop a
  mov b, [d]
  mov c, 0
  pop d
  mov [d], b
; klingons = (tmp >> 8) & 0x0F; 
  mov d, _klingons ; $klingons
  push d
  lea d, [bp + -3] ; $tmp
  mov b, [d]
  mov c, 0
; --- START SHIFT
  push a
  mov a, b
  mov32 cb, $00000008
  mov c, b
  shr a, cl
  mov b, a
  pop a
; --- END SHIFT
  push a
  mov a, b
  mov32 cb, $0000000f
  and b, a ; &
  pop a
  pop d
  mov [d], bl
; starbases = (tmp >> 4) & 0x0F; 
  mov d, _starbases ; $starbases
  push d
  lea d, [bp + -3] ; $tmp
  mov b, [d]
  mov c, 0
; --- START SHIFT
  push a
  mov a, b
  mov32 cb, $00000004
  mov c, b
  shr a, cl
  mov b, a
  pop a
; --- END SHIFT
  push a
  mov a, b
  mov32 cb, $0000000f
  and b, a ; &
  pop a
  pop d
  mov [d], bl
; stars = tmp & 0x0F; 
  mov d, _stars ; $stars
  push d
  lea d, [bp + -3] ; $tmp
  mov b, [d]
  mov c, 0
  push a
  mov a, b
  mov32 cb, $0000000f
  and b, a ; &
  pop a
  pop d
  mov [d], bl
; if (klingons > 0) { 
_if64_cond:
  mov d, _klingons ; $klingons
  mov bl, [d]
  mov bh, 0
  mov c, 0
; --- START RELATIONAL
  push a
  mov a, b
  mov32 cb, $00000000
  cmp a, b
  sgu ; > (unsigned)
  pop a
; --- END RELATIONAL
  cmp b, 0
  je _if64_exit
_if64_TRUE:
; printf("Combat Area  Condition Red\n"); 
; --- START FUNCTION CALL
  mov b, _s61 ; "Combat Area  Condition Red\n"
  swp b
  push b
  call printf
  add sp, 2
; --- END FUNCTION CALL
; if (shield < 200) 
_if65_cond:
  mov d, _shield ; $shield
  mov b, [d]
  mov c, 0
; --- START RELATIONAL
  push a
  mov a, b
  mov32 cb, $000000c8
  cmp a, b
  slt ; < (signed)
  pop a
; --- END RELATIONAL
  cmp b, 0
  je _if65_exit
_if65_TRUE:
; printf("Shields Dangerously Low\n"); 
; --- START FUNCTION CALL
  mov b, _s62 ; "Shields Dangerously Low\n"
  swp b
  push b
  call printf
  add sp, 2
; --- END FUNCTION CALL
  jmp _if65_exit
_if65_exit:
  jmp _if64_exit
_if64_exit:
; for (i = 1; i <= 3; i++) { 
_for66_init:
  lea d, [bp + -1] ; $i
  push d
  mov32 cb, $00000001
  pop d
  mov [d], b
_for66_cond:
  lea d, [bp + -1] ; $i
  mov b, [d]
  mov c, 0
; --- START RELATIONAL
  push a
  mov a, b
  mov32 cb, $00000003
  cmp a, b
  sle ; <= (signed)
  pop a
; --- END RELATIONAL
  cmp b, 0
  je _for66_exit
_for66_block:
; k->y = 0; 
  lea d, [bp + -5] ; $k
  mov d, [d]
  add d, 0
  push d
  mov32 cb, $00000000
  pop d
  mov [d], bl
; k->x = 0; 
  lea d, [bp + -5] ; $k
  mov d, [d]
  add d, 1
  push d
  mov32 cb, $00000000
  pop d
  mov [d], bl
; k->energy = 0; 
  lea d, [bp + -5] ; $k
  mov d, [d]
  add d, 2
  push d
  mov32 cb, $00000000
  pop d
  mov [d], b
; k++; 
  lea d, [bp + -5] ; $k
  mov b, [d]
  mov c, 0
  mov a, b
  inc b
  inc b
  lea d, [bp + -5] ; $k
  mov [d], b
  mov b, a
_for66_update:
  lea d, [bp + -1] ; $i
  mov b, [d]
  mov c, 0
  mov a, b
  inc b
  lea d, [bp + -1] ; $i
  mov [d], b
  mov b, a
  jmp _for66_cond
_for66_exit:
; memset(quad, 		0       , 64); 
; --- START FUNCTION CALL
  mov32 cb, $00000040
  swp b
  push b
  mov32 cb, $00000000
  push bl
  mov d, _quad_data ; $quad
  mov b, d
  mov c, 0
  swp b
  push b
  call memset
  add sp, 5
; --- END FUNCTION CALL
; place_ship(); 
; --- START FUNCTION CALL
  call place_ship
; if (klingons > 0) { 
_if67_cond:
  mov d, _klingons ; $klingons
  mov bl, [d]
  mov bh, 0
  mov c, 0
; --- START RELATIONAL
  push a
  mov a, b
  mov32 cb, $00000000
  cmp a, b
  sgu ; > (unsigned)
  pop a
; --- END RELATIONAL
  cmp b, 0
  je _if67_exit
_if67_TRUE:
; k = kdata; 
  lea d, [bp + -5] ; $k
  push d
  mov d, _kdata_data ; $kdata
  mov b, d
  mov c, 0
  pop d
  mov [d], b
; for (i = 0; i < klingons; i++) { 
_for68_init:
  lea d, [bp + -1] ; $i
  push d
  mov32 cb, $00000000
  pop d
  mov [d], b
_for68_cond:
  lea d, [bp + -1] ; $i
  mov b, [d]
  mov c, 0
; --- START RELATIONAL
  push a
  mov a, b
  mov d, _klingons ; $klingons
  mov bl, [d]
  mov bh, 0
  mov c, 0
  cmp a, b
  slt ; < (signed)
  pop a
; --- END RELATIONAL
  cmp b, 0
  je _for68_exit
_for68_block:
; find_set_empty_place(	3         , k->y, k->x); 
; --- START FUNCTION CALL
  lea d, [bp + -5] ; $k
  mov d, [d]
  add d, 1
  mov bl, [d]
  mov bh, 0
  mov c, 0
  swp b
  push b
  lea d, [bp + -5] ; $k
  mov d, [d]
  add d, 0
  mov bl, [d]
  mov bh, 0
  mov c, 0
  swp b
  push b
  mov32 cb, $00000003
  push bl
  call find_set_empty_place
  add sp, 5
; --- END FUNCTION CALL
; k->energy = 100 + get_rand(200); 
  lea d, [bp + -5] ; $k
  mov d, [d]
  add d, 2
  push d
  mov32 cb, $00000064
; --- START TERMS
  push a
  mov a, b
; --- START FUNCTION CALL
  mov32 cb, $000000c8
  swp b
  push b
  call get_rand
  add sp, 2
; --- END FUNCTION CALL
  add b, a
  pop a
; --- END TERMS
  pop d
  mov [d], b
; k++; 
  lea d, [bp + -5] ; $k
  mov b, [d]
  mov c, 0
  mov a, b
  inc b
  inc b
  lea d, [bp + -5] ; $k
  mov [d], b
  mov b, a
_for68_update:
  lea d, [bp + -1] ; $i
  mov b, [d]
  mov c, 0
  mov a, b
  inc b
  lea d, [bp + -1] ; $i
  mov [d], b
  mov b, a
  jmp _for68_cond
_for68_exit:
  jmp _if67_exit
_if67_exit:
; if (starbases > 0) 
_if69_cond:
  mov d, _starbases ; $starbases
  mov bl, [d]
  mov bh, 0
  mov c, 0
; --- START RELATIONAL
  push a
  mov a, b
  mov32 cb, $00000000
  cmp a, b
  sgt ; >
  pop a
; --- END RELATIONAL
  cmp b, 0
  je _if69_exit
_if69_TRUE:
; find_set_empty_place(		2      , &base_y, &base_x); 
; --- START FUNCTION CALL
  mov d, _base_x ; $base_x
  mov b, d
  swp b
  push b
  mov d, _base_y ; $base_y
  mov b, d
  swp b
  push b
  mov32 cb, $00000002
  push bl
  call find_set_empty_place
  add sp, 5
; --- END FUNCTION CALL
  jmp _if69_exit
_if69_exit:
; for (i = 1; i <= stars; i++) 
_for70_init:
  lea d, [bp + -1] ; $i
  push d
  mov32 cb, $00000001
  pop d
  mov [d], b
_for70_cond:
  lea d, [bp + -1] ; $i
  mov b, [d]
  mov c, 0
; --- START RELATIONAL
  push a
  mov a, b
  mov d, _stars ; $stars
  mov bl, [d]
  mov bh, 0
  mov c, 0
  cmp a, b
  sle ; <= (signed)
  pop a
; --- END RELATIONAL
  cmp b, 0
  je _for70_exit
_for70_block:
; find_set_empty_place(		1      ,  0    ,  0    ); 
; --- START FUNCTION CALL
  mov32 cb, $00000000
  swp b
  push b
  mov32 cb, $00000000
  swp b
  push b
  mov32 cb, $00000001
  push bl
  call find_set_empty_place
  add sp, 5
; --- END FUNCTION CALL
_for70_update:
  lea d, [bp + -1] ; $i
  mov b, [d]
  mov c, 0
  mov a, b
  inc b
  lea d, [bp + -1] ; $i
  mov [d], b
  mov b, a
  jmp _for70_cond
_for70_exit:
  leave
  ret

course_control:
  enter 0 ; (push bp; mov bp, sp)
; int i; 
  sub sp, 2
; int        c1; 
  sub sp, 2
; int        warp; 
  sub sp, 2
; unsigned int         n; 
  sub sp, 2
; int c2, c3, c4; 
  sub sp, 2
  sub sp, 2
  sub sp, 2
; int        z1, z2; 
  sub sp, 2
  sub sp, 2
; int        x1, x2; 
  sub sp, 2
  sub sp, 2
; int        x, y; 
  sub sp, 2
  sub sp, 2
; unsigned char        outside = 0;		/* Outside galaxy flag */ 
  sub sp, 1
; --- START LOCAL VAR INITIALIZATION
  lea d, [bp + -26] ; $outside
  push d
  mov32 cb, $00000000
  pop d
  mov [d], bl
; --- END LOCAL VAR INITIALIZATION
; unsigned char        quad_y_old; 
  sub sp, 1
; unsigned char        quad_x_old; 
  sub sp, 1
; puts("Course (0-9): " ); 
; --- START FUNCTION CALL
  mov b, _s63 ; "Course (0-9): "
  swp b
  push b
  call puts
  add sp, 2
; --- END FUNCTION CALL
; c1 = input_f00(); 
  lea d, [bp + -3] ; $c1
  push d
; --- START FUNCTION CALL
  call input_f00
  pop d
  mov [d], b
; if (c1 == 900) 
_if71_cond:
  lea d, [bp + -3] ; $c1
  mov b, [d]
  mov c, 0
; --- START RELATIONAL
  push a
  mov a, b
  mov32 cb, $00000384
  cmp a, b
  seq ; ==
  pop a
; --- END RELATIONAL
  cmp b, 0
  je _if71_exit
_if71_TRUE:
; c1 = 100; 
  lea d, [bp + -3] ; $c1
  push d
  mov32 cb, $00000064
  pop d
  mov [d], b
  jmp _if71_exit
_if71_exit:
; if (c1 < 0 || c1 > 900) { 
_if72_cond:
  lea d, [bp + -3] ; $c1
  mov b, [d]
  mov c, 0
; --- START RELATIONAL
  push a
  mov a, b
  mov32 cb, $00000000
  cmp a, b
  slt ; < (signed)
  pop a
; --- END RELATIONAL
; --- START LOGICAL OR
  push a
  mov a, b
  lea d, [bp + -3] ; $c1
  mov b, [d]
  mov c, 0
; --- START RELATIONAL
  push a
  mov a, b
  mov32 cb, $00000384
  cmp a, b
  sgt ; >
  pop a
; --- END RELATIONAL
  sor a, b ; ||
  pop a
; --- END LOGICAL OR
  cmp b, 0
  je _if72_exit
_if72_TRUE:
; printf("Lt. Sulu%s", inc_1); 
; --- START FUNCTION CALL
  mov d, _inc_1 ; $inc_1
  mov b, [d]
  mov c, 0
  swp b
  push b
  mov b, _s64 ; "Lt. Sulu%s"
  swp b
  push b
  call printf
  add sp, 4
; --- END FUNCTION CALL
; return; 
  leave
  ret
  jmp _if72_exit
_if72_exit:
; if (damage[1] < 0) 
_if73_cond:
  mov d, _damage_data ; $damage
  push a
  push d
  mov32 cb, $00000001
  pop d
  mma 2 ; mov a, 2; mul a, b; add d, b
  pop a
  mov b, [d]
  mov c, 0
; --- START RELATIONAL
  push a
  mov a, b
  mov32 cb, $00000000
  cmp a, b
  slt ; < (signed)
  pop a
; --- END RELATIONAL
  cmp b, 0
  je _if73_exit
_if73_TRUE:
; strcpy(warpmax, "0.2"); 
; --- START FUNCTION CALL
  mov b, _s65 ; "0.2"
  swp b
  push b
  mov d, _warpmax_data ; $warpmax
  mov b, d
  mov c, 0
  swp b
  push b
  call strcpy
  add sp, 4
; --- END FUNCTION CALL
  jmp _if73_exit
_if73_exit:
; printf("Warp Factor (0-%s): ", warpmax); 
; --- START FUNCTION CALL
  mov d, _warpmax_data ; $warpmax
  mov b, d
  mov c, 0
  swp b
  push b
  mov b, _s66 ; "Warp Factor (0-%s): "
  swp b
  push b
  call printf
  add sp, 4
; --- END FUNCTION CALL
; warp = input_f00(); 
  lea d, [bp + -5] ; $warp
  push d
; --- START FUNCTION CALL
  call input_f00
  pop d
  mov [d], b
; if (damage[1] < 0 && warp > 20) { 
_if74_cond:
  mov d, _damage_data ; $damage
  push a
  push d
  mov32 cb, $00000001
  pop d
  mma 2 ; mov a, 2; mul a, b; add d, b
  pop a
  mov b, [d]
  mov c, 0
; --- START RELATIONAL
  push a
  mov a, b
  mov32 cb, $00000000
  cmp a, b
  slt ; < (signed)
  pop a
; --- END RELATIONAL
; --- START LOGICAL AND
  push a
  mov a, b
  lea d, [bp + -5] ; $warp
  mov b, [d]
  mov c, 0
; --- START RELATIONAL
  push a
  mov a, b
  mov32 cb, $00000014
  cmp a, b
  sgt ; >
  pop a
; --- END RELATIONAL
  sand a, b
  pop a
; --- END LOGICAL AND
  cmp b, 0
  je _if74_exit
_if74_TRUE:
; printf("Warp Engines are damaged. Maximum speed = Warp 0.2.\n\n"); 
; --- START FUNCTION CALL
  mov b, _s67 ; "Warp Engines are damaged. Maximum speed = Warp 0.2.\n\n"
  swp b
  push b
  call printf
  add sp, 2
; --- END FUNCTION CALL
; return; 
  leave
  ret
  jmp _if74_exit
_if74_exit:
; if (warp <= 0) 
_if75_cond:
  lea d, [bp + -5] ; $warp
  mov b, [d]
  mov c, 0
; --- START RELATIONAL
  push a
  mov a, b
  mov32 cb, $00000000
  cmp a, b
  sle ; <= (signed)
  pop a
; --- END RELATIONAL
  cmp b, 0
  je _if75_exit
_if75_TRUE:
; return; 
  leave
  ret
  jmp _if75_exit
_if75_exit:
; if (warp > 800) { 
_if76_cond:
  lea d, [bp + -5] ; $warp
  mov b, [d]
  mov c, 0
; --- START RELATIONAL
  push a
  mov a, b
  mov32 cb, $00000320
  cmp a, b
  sgt ; >
  pop a
; --- END RELATIONAL
  cmp b, 0
  je _if76_exit
_if76_TRUE:
; printf("Chief Engineer Scott reports:\n  The engines won't take warp %s!\n\n", print100(warp)); 
; --- START FUNCTION CALL
; --- START FUNCTION CALL
  lea d, [bp + -5] ; $warp
  mov b, [d]
  mov c, 0
  swp b
  push b
  call print100
  add sp, 2
; --- END FUNCTION CALL
  swp b
  push b
  mov b, _s68 ; "Chief Engineer Scott reports:\n  The engines won't take warp %s!\n\n"
  swp b
  push b
  call printf
  add sp, 4
; --- END FUNCTION CALL
; return; 
  leave
  ret
  jmp _if76_exit
_if76_exit:
; n = warp * 8; 
  lea d, [bp + -7] ; $n
  push d
  lea d, [bp + -5] ; $warp
  mov b, [d]
  mov c, 0
; --- START FACTORS
  push a
  push g
  mov a, b
  mov g, c
  mov32 cb, $00000008
  push a     ; save left operand
  xor a, b   ; xor sign bits
  swp a      ; swap bytes
  mov cl, al ; save result of xor into 'dl'
  pop a      ; restore left side operator
  push cl    ; save result of xor above
  swp a  
  test al, $80  
  swp a  
  jz skip_invert_a_78  
  neg a 
skip_invert_a_78:   
  swp b
  test bl, $80  
  swp b
  jz skip_invert_b_78  
  neg b 
skip_invert_b_78:   
  mul a, b ; *
  mov g, a
  mov a, b
  pop bl
  test bl, $80
  jz _same_signs_78
  mov bl, al
  not a
  neg b
  adc a, 0
  mov g, a
  mov a, b
_same_signs_78:
  mov c, g
  mov b, a
  pop g
  pop a
; --- END FACTORS
  pop d
  mov [d], b
; n = cint100(n);	 
  lea d, [bp + -7] ; $n
  push d
; --- START FUNCTION CALL
  lea d, [bp + -7] ; $n
  mov b, [d]
  mov c, 0
  swp b
  push b
  call cint100
  add sp, 2
; --- END FUNCTION CALL
  pop d
  mov [d], b
; if (energy - n < 0) { 
_if79_cond:
  mov d, _energy ; $energy
  mov b, [d]
  mov c, 0
; --- START TERMS
  push a
  mov a, b
  lea d, [bp + -7] ; $n
  mov b, [d]
  mov c, 0
  sub a, b
  mov b, a
  pop a
; --- END TERMS
; --- START RELATIONAL
  push a
  mov a, b
  mov32 cb, $00000000
  cmp a, b
  slu ; < (unsigned)
  pop a
; --- END RELATIONAL
  cmp b, 0
  je _if79_exit
_if79_TRUE:
; printf("Engineering reports:\n  Insufficient energy available for maneuvering at warp %s!\n\n", print100(warp)); 
; --- START FUNCTION CALL
; --- START FUNCTION CALL
  lea d, [bp + -5] ; $warp
  mov b, [d]
  mov c, 0
  swp b
  push b
  call print100
  add sp, 2
; --- END FUNCTION CALL
  swp b
  push b
  mov b, _s69 ; "Engineering reports:\n  Insufficient energy available for maneuvering at warp %s!\n\n"
  swp b
  push b
  call printf
  add sp, 4
; --- END FUNCTION CALL
; if (shield >= n && damage[7] >= 0) { 
_if80_cond:
  mov d, _shield ; $shield
  mov b, [d]
  mov c, 0
; --- START RELATIONAL
  push a
  mov a, b
  lea d, [bp + -7] ; $n
  mov b, [d]
  mov c, 0
  cmp a, b
  sge ; >=
  pop a
; --- END RELATIONAL
; --- START LOGICAL AND
  push a
  mov a, b
  mov d, _damage_data ; $damage
  push a
  push d
  mov32 cb, $00000007
  pop d
  mma 2 ; mov a, 2; mul a, b; add d, b
  pop a
  mov b, [d]
  mov c, 0
; --- START RELATIONAL
  push a
  mov a, b
  mov32 cb, $00000000
  cmp a, b
  sge ; >=
  pop a
; --- END RELATIONAL
  sand a, b
  pop a
; --- END LOGICAL AND
  cmp b, 0
  je _if80_exit
_if80_TRUE:
; printf("Deflector Control Room acknowledges:\n  %d units of energy presently deployed to shields.\n", shield); 
; --- START FUNCTION CALL
  mov d, _shield ; $shield
  mov b, [d]
  mov c, 0
  swp b
  push b
  mov b, _s70 ; "Deflector Control Room acknowledges:\n  %d units of energy presently deployed to shields.\n"
  swp b
  push b
  call printf
  add sp, 4
; --- END FUNCTION CALL
  jmp _if80_exit
_if80_exit:
; return; 
  leave
  ret
  jmp _if79_exit
_if79_exit:
; klingons_move(); 
; --- START FUNCTION CALL
  call klingons_move
; repair_damage(warp); 
; --- START FUNCTION CALL
  lea d, [bp + -5] ; $warp
  mov b, [d]
  mov c, 0
  swp b
  push b
  call repair_damage
  add sp, 2
; --- END FUNCTION CALL
; z1 = FROM_FIXED00(ship_y); 
  lea d, [bp + -15] ; $z1
  push d
; --- START FUNCTION CALL
  mov d, _ship_y ; $ship_y
  mov b, [d]
  mov c, 0
  swp b
  push b
  call FROM_FIXED00
  add sp, 2
; --- END FUNCTION CALL
  pop d
  mov [d], b
; z2 = FROM_FIXED00(ship_x); 
  lea d, [bp + -17] ; $z2
  push d
; --- START FUNCTION CALL
  mov d, _ship_x ; $ship_x
  mov b, [d]
  mov c, 0
  swp b
  push b
  call FROM_FIXED00
  add sp, 2
; --- END FUNCTION CALL
  pop d
  mov [d], b
; quad[z1+-1][z2+-1] = 		0       ; 
  mov d, _quad_data ; $quad
  push a
  push d
  lea d, [bp + -15] ; $z1
  mov b, [d]
  mov c, 0
; --- START TERMS
  push a
  mov a, b
  mov32 cb, $ffffffff
  add b, a
  pop a
; --- END TERMS
  pop d
  mma 8 ; mov a, 8; mul a, b; add d, b
  push d
  lea d, [bp + -17] ; $z2
  mov b, [d]
  mov c, 0
; --- START TERMS
  push a
  mov a, b
  mov32 cb, $ffffffff
  add b, a
  pop a
; --- END TERMS
  pop d
  add d, b
  pop a
  push d
  mov32 cb, $00000000
  pop d
  mov [d], bl
; c2 = FROM_FIXED00(c1);	/* Integer part */ 
  lea d, [bp + -9] ; $c2
  push d
; --- START FUNCTION CALL
  lea d, [bp + -3] ; $c1
  mov b, [d]
  mov c, 0
  swp b
  push b
  call FROM_FIXED00
  add sp, 2
; --- END FUNCTION CALL
  pop d
  mov [d], b
; c3 = c2 + 1;		/* Next integer part */ 
  lea d, [bp + -11] ; $c3
  push d
  lea d, [bp + -9] ; $c2
  mov b, [d]
  mov c, 0
; --- START TERMS
  push a
  mov a, b
  mov32 cb, $00000001
  add b, a
  pop a
; --- END TERMS
  pop d
  mov [d], b
; c4 = (c1 - TO_FIXED00(c2));	/* Fractional element in fixed point */ 
  lea d, [bp + -13] ; $c4
  push d
  lea d, [bp + -3] ; $c1
  mov b, [d]
  mov c, 0
; --- START TERMS
  push a
  mov a, b
; --- START FUNCTION CALL
  lea d, [bp + -9] ; $c2
  mov b, [d]
  mov c, 0
  swp b
  push b
  call TO_FIXED00
  add sp, 2
; --- END FUNCTION CALL
  sub a, b
  mov b, a
  pop a
; --- END TERMS
  pop d
  mov [d], b
; x1 = 100 * c[1][c2] + (c[1][c3] - c[1][c2]) * c4; 
  lea d, [bp + -19] ; $x1
  push d
  mov32 cb, $00000064
; --- START FACTORS
  push a
  push g
  mov a, b
  mov g, c
  mov d, _c_data ; $c
  push a
  push d
  mov32 cb, $00000001
  pop d
  mma 10 ; mov a, 10; mul a, b; add d, b
  push d
  lea d, [bp + -9] ; $c2
  mov b, [d]
  mov c, 0
  pop d
  add d, b
  pop a
  mov bl, [d]
  mov bh, 0
  mov c, 0
  push a     ; save left operand
  xor a, b   ; xor sign bits
  swp a      ; swap bytes
  mov cl, al ; save result of xor into 'dl'
  pop a      ; restore left side operator
  push cl    ; save result of xor above
  swp a  
  test al, $80  
  swp a  
  jz skip_invert_a_83  
  neg a 
skip_invert_a_83:   
  swp b
  test bl, $80  
  swp b
  jz skip_invert_b_83  
  neg b 
skip_invert_b_83:   
  mul a, b ; *
  mov g, a
  mov a, b
  pop bl
  test bl, $80
  jz _same_signs_83
  mov bl, al
  not a
  neg b
  adc a, 0
  mov g, a
  mov a, b
_same_signs_83:
  mov c, g
  mov b, a
  pop g
  pop a
; --- END FACTORS
; --- START TERMS
  push a
  push g
  mov a, b
  mov g, c
  mov d, _c_data ; $c
  push a
  push d
  mov32 cb, $00000001
  pop d
  mma 10 ; mov a, 10; mul a, b; add d, b
  push d
  lea d, [bp + -11] ; $c3
  mov b, [d]
  mov c, 0
  pop d
  add d, b
  pop a
  mov bl, [d]
  mov bh, 0
  mov c, 0
; --- START TERMS
  push a
  mov a, b
  mov d, _c_data ; $c
  push a
  push d
  mov32 cb, $00000001
  pop d
  mma 10 ; mov a, 10; mul a, b; add d, b
  push d
  lea d, [bp + -9] ; $c2
  mov b, [d]
  mov c, 0
  pop d
  add d, b
  pop a
  mov bl, [d]
  mov bh, 0
  mov c, 0
  sub a, b
  mov b, a
  pop a
; --- END TERMS
; --- START FACTORS
  push a
  push g
  mov a, b
  mov g, c
  lea d, [bp + -13] ; $c4
  mov b, [d]
  mov c, 0
  push a     ; save left operand
  xor a, b   ; xor sign bits
  swp a      ; swap bytes
  mov cl, al ; save result of xor into 'dl'
  pop a      ; restore left side operator
  push cl    ; save result of xor above
  swp a  
  test al, $80  
  swp a  
  jz skip_invert_a_84  
  neg a 
skip_invert_a_84:   
  swp b
  test bl, $80  
  swp b
  jz skip_invert_b_84  
  neg b 
skip_invert_b_84:   
  mul a, b ; *
  mov g, a
  mov a, b
  pop bl
  test bl, $80
  jz _same_signs_84
  mov bl, al
  not a
  neg b
  adc a, 0
  mov g, a
  mov a, b
_same_signs_84:
  mov c, g
  mov b, a
  pop g
  pop a
; --- END FACTORS
  add32 cb, ga
  pop g
  pop a
; --- END TERMS
  pop d
  mov [d], b
; x2 = 100 * c[2][c2] + (c[2][c3] - c[2][c2]) * c4; 
  lea d, [bp + -21] ; $x2
  push d
  mov32 cb, $00000064
; --- START FACTORS
  push a
  push g
  mov a, b
  mov g, c
  mov d, _c_data ; $c
  push a
  push d
  mov32 cb, $00000002
  pop d
  mma 10 ; mov a, 10; mul a, b; add d, b
  push d
  lea d, [bp + -9] ; $c2
  mov b, [d]
  mov c, 0
  pop d
  add d, b
  pop a
  mov bl, [d]
  mov bh, 0
  mov c, 0
  push a     ; save left operand
  xor a, b   ; xor sign bits
  swp a      ; swap bytes
  mov cl, al ; save result of xor into 'dl'
  pop a      ; restore left side operator
  push cl    ; save result of xor above
  swp a  
  test al, $80  
  swp a  
  jz skip_invert_a_87  
  neg a 
skip_invert_a_87:   
  swp b
  test bl, $80  
  swp b
  jz skip_invert_b_87  
  neg b 
skip_invert_b_87:   
  mul a, b ; *
  mov g, a
  mov a, b
  pop bl
  test bl, $80
  jz _same_signs_87
  mov bl, al
  not a
  neg b
  adc a, 0
  mov g, a
  mov a, b
_same_signs_87:
  mov c, g
  mov b, a
  pop g
  pop a
; --- END FACTORS
; --- START TERMS
  push a
  push g
  mov a, b
  mov g, c
  mov d, _c_data ; $c
  push a
  push d
  mov32 cb, $00000002
  pop d
  mma 10 ; mov a, 10; mul a, b; add d, b
  push d
  lea d, [bp + -11] ; $c3
  mov b, [d]
  mov c, 0
  pop d
  add d, b
  pop a
  mov bl, [d]
  mov bh, 0
  mov c, 0
; --- START TERMS
  push a
  mov a, b
  mov d, _c_data ; $c
  push a
  push d
  mov32 cb, $00000002
  pop d
  mma 10 ; mov a, 10; mul a, b; add d, b
  push d
  lea d, [bp + -9] ; $c2
  mov b, [d]
  mov c, 0
  pop d
  add d, b
  pop a
  mov bl, [d]
  mov bh, 0
  mov c, 0
  sub a, b
  mov b, a
  pop a
; --- END TERMS
; --- START FACTORS
  push a
  push g
  mov a, b
  mov g, c
  lea d, [bp + -13] ; $c4
  mov b, [d]
  mov c, 0
  push a     ; save left operand
  xor a, b   ; xor sign bits
  swp a      ; swap bytes
  mov cl, al ; save result of xor into 'dl'
  pop a      ; restore left side operator
  push cl    ; save result of xor above
  swp a  
  test al, $80  
  swp a  
  jz skip_invert_a_88  
  neg a 
skip_invert_a_88:   
  swp b
  test bl, $80  
  swp b
  jz skip_invert_b_88  
  neg b 
skip_invert_b_88:   
  mul a, b ; *
  mov g, a
  mov a, b
  pop bl
  test bl, $80
  jz _same_signs_88
  mov bl, al
  not a
  neg b
  adc a, 0
  mov g, a
  mov a, b
_same_signs_88:
  mov c, g
  mov b, a
  pop g
  pop a
; --- END FACTORS
  add32 cb, ga
  pop g
  pop a
; --- END TERMS
  pop d
  mov [d], b
; x = ship_y; 
  lea d, [bp + -23] ; $x
  push d
  mov d, _ship_y ; $ship_y
  mov b, [d]
  mov c, 0
  pop d
  mov [d], b
; y = ship_x; 
  lea d, [bp + -25] ; $y
  push d
  mov d, _ship_x ; $ship_x
  mov b, [d]
  mov c, 0
  pop d
  mov [d], b
; for (i = 1; i <= n; i++) { 
_for89_init:
  lea d, [bp + -1] ; $i
  push d
  mov32 cb, $00000001
  pop d
  mov [d], b
_for89_cond:
  lea d, [bp + -1] ; $i
  mov b, [d]
  mov c, 0
; --- START RELATIONAL
  push a
  mov a, b
  lea d, [bp + -7] ; $n
  mov b, [d]
  mov c, 0
  cmp a, b
  sle ; <= (signed)
  pop a
; --- END RELATIONAL
  cmp b, 0
  je _for89_exit
_for89_block:
; ship_y = ship_y + x1; 
  mov d, _ship_y ; $ship_y
  push d
  mov d, _ship_y ; $ship_y
  mov b, [d]
  mov c, 0
; --- START TERMS
  push a
  mov a, b
  lea d, [bp + -19] ; $x1
  mov b, [d]
  mov c, 0
  add b, a
  pop a
; --- END TERMS
  pop d
  mov [d], b
; ship_x = ship_x + x2; 
  mov d, _ship_x ; $ship_x
  push d
  mov d, _ship_x ; $ship_x
  mov b, [d]
  mov c, 0
; --- START TERMS
  push a
  mov a, b
  lea d, [bp + -21] ; $x2
  mov b, [d]
  mov c, 0
  add b, a
  pop a
; --- END TERMS
  pop d
  mov [d], b
; z1 = FROM_FIXED00(ship_y); 
  lea d, [bp + -15] ; $z1
  push d
; --- START FUNCTION CALL
  mov d, _ship_y ; $ship_y
  mov b, [d]
  mov c, 0
  swp b
  push b
  call FROM_FIXED00
  add sp, 2
; --- END FUNCTION CALL
  pop d
  mov [d], b
; z2 = FROM_FIXED00(ship_x);	/* ?? cint100 ?? */ 
  lea d, [bp + -17] ; $z2
  push d
; --- START FUNCTION CALL
  mov d, _ship_x ; $ship_x
  mov b, [d]
  mov c, 0
  swp b
  push b
  call FROM_FIXED00
  add sp, 2
; --- END FUNCTION CALL
  pop d
  mov [d], b
; if (z1 < 1 || z1 >= 9 || z2 < 1 || z2 >= 9) { 
_if90_cond:
  lea d, [bp + -15] ; $z1
  mov b, [d]
  mov c, 0
; --- START RELATIONAL
  push a
  mov a, b
  mov32 cb, $00000001
  cmp a, b
  slt ; < (signed)
  pop a
; --- END RELATIONAL
; --- START LOGICAL OR
  push a
  mov a, b
  lea d, [bp + -15] ; $z1
  mov b, [d]
  mov c, 0
; --- START RELATIONAL
  push a
  mov a, b
  mov32 cb, $00000009
  cmp a, b
  sge ; >=
  pop a
; --- END RELATIONAL
  sor a, b ; ||
  mov a, b
  lea d, [bp + -17] ; $z2
  mov b, [d]
  mov c, 0
; --- START RELATIONAL
  push a
  mov a, b
  mov32 cb, $00000001
  cmp a, b
  slt ; < (signed)
  pop a
; --- END RELATIONAL
  sor a, b ; ||
  mov a, b
  lea d, [bp + -17] ; $z2
  mov b, [d]
  mov c, 0
; --- START RELATIONAL
  push a
  mov a, b
  mov32 cb, $00000009
  cmp a, b
  sge ; >=
  pop a
; --- END RELATIONAL
  sor a, b ; ||
  pop a
; --- END LOGICAL OR
  cmp b, 0
  je _if90_exit
_if90_TRUE:
; outside = 0;		/* Outside galaxy flag */ 
  lea d, [bp + -26] ; $outside
  push d
  mov32 cb, $00000000
  pop d
  mov [d], bl
; quad_y_old = quad_y; 
  lea d, [bp + -27] ; $quad_y_old
  push d
  mov d, _quad_y ; $quad_y
  mov b, [d]
  mov c, 0
  pop d
  mov [d], bl
; quad_x_old = quad_x; 
  lea d, [bp + -28] ; $quad_x_old
  push d
  mov d, _quad_x ; $quad_x
  mov b, [d]
  mov c, 0
  pop d
  mov [d], bl
; x = (800 * quad_y) + x + (n * x1); 
  lea d, [bp + -23] ; $x
  push d
  mov32 cb, $00000320
; --- START FACTORS
  push a
  push g
  mov a, b
  mov g, c
  mov d, _quad_y ; $quad_y
  mov b, [d]
  mov c, 0
  push a     ; save left operand
  xor a, b   ; xor sign bits
  swp a      ; swap bytes
  mov cl, al ; save result of xor into 'dl'
  pop a      ; restore left side operator
  push cl    ; save result of xor above
  swp a  
  test al, $80  
  swp a  
  jz skip_invert_a_96  
  neg a 
skip_invert_a_96:   
  swp b
  test bl, $80  
  swp b
  jz skip_invert_b_96  
  neg b 
skip_invert_b_96:   
  mul a, b ; *
  mov g, a
  mov a, b
  pop bl
  test bl, $80
  jz _same_signs_96
  mov bl, al
  not a
  neg b
  adc a, 0
  mov g, a
  mov a, b
_same_signs_96:
  mov c, g
  mov b, a
  pop g
  pop a
; --- END FACTORS
; --- START TERMS
  push a
  push g
  mov a, b
  mov g, c
  lea d, [bp + -23] ; $x
  mov b, [d]
  mov c, 0
  mov c, 0
  add32 cb, ga
  mov a, b
  mov g, c
  lea d, [bp + -7] ; $n
  mov b, [d]
  mov c, 0
; --- START FACTORS
  push a
  push g
  mov a, b
  mov g, c
  lea d, [bp + -19] ; $x1
  mov b, [d]
  mov c, 0
  push a     ; save left operand
  xor a, b   ; xor sign bits
  swp a      ; swap bytes
  mov cl, al ; save result of xor into 'dl'
  pop a      ; restore left side operator
  push cl    ; save result of xor above
  swp a  
  test al, $80  
  swp a  
  jz skip_invert_a_98  
  neg a 
skip_invert_a_98:   
  swp b
  test bl, $80  
  swp b
  jz skip_invert_b_98  
  neg b 
skip_invert_b_98:   
  mul a, b ; *
  mov g, a
  mov a, b
  pop bl
  test bl, $80
  jz _same_signs_98
  mov bl, al
  not a
  neg b
  adc a, 0
  mov g, a
  mov a, b
_same_signs_98:
  mov c, g
  mov b, a
  pop g
  pop a
; --- END FACTORS
  add32 cb, ga
  pop g
  pop a
; --- END TERMS
  pop d
  mov [d], b
; y = (800 * quad_x) + y + (n * x2); 
  lea d, [bp + -25] ; $y
  push d
  mov32 cb, $00000320
; --- START FACTORS
  push a
  push g
  mov a, b
  mov g, c
  mov d, _quad_x ; $quad_x
  mov b, [d]
  mov c, 0
  push a     ; save left operand
  xor a, b   ; xor sign bits
  swp a      ; swap bytes
  mov cl, al ; save result of xor into 'dl'
  pop a      ; restore left side operator
  push cl    ; save result of xor above
  swp a  
  test al, $80  
  swp a  
  jz skip_invert_a_104  
  neg a 
skip_invert_a_104:   
  swp b
  test bl, $80  
  swp b
  jz skip_invert_b_104  
  neg b 
skip_invert_b_104:   
  mul a, b ; *
  mov g, a
  mov a, b
  pop bl
  test bl, $80
  jz _same_signs_104
  mov bl, al
  not a
  neg b
  adc a, 0
  mov g, a
  mov a, b
_same_signs_104:
  mov c, g
  mov b, a
  pop g
  pop a
; --- END FACTORS
; --- START TERMS
  push a
  push g
  mov a, b
  mov g, c
  lea d, [bp + -25] ; $y
  mov b, [d]
  mov c, 0
  mov c, 0
  add32 cb, ga
  mov a, b
  mov g, c
  lea d, [bp + -7] ; $n
  mov b, [d]
  mov c, 0
; --- START FACTORS
  push a
  push g
  mov a, b
  mov g, c
  lea d, [bp + -21] ; $x2
  mov b, [d]
  mov c, 0
  push a     ; save left operand
  xor a, b   ; xor sign bits
  swp a      ; swap bytes
  mov cl, al ; save result of xor into 'dl'
  pop a      ; restore left side operator
  push cl    ; save result of xor above
  swp a  
  test al, $80  
  swp a  
  jz skip_invert_a_106  
  neg a 
skip_invert_a_106:   
  swp b
  test bl, $80  
  swp b
  jz skip_invert_b_106  
  neg b 
skip_invert_b_106:   
  mul a, b ; *
  mov g, a
  mov a, b
  pop bl
  test bl, $80
  jz _same_signs_106
  mov bl, al
  not a
  neg b
  adc a, 0
  mov g, a
  mov a, b
_same_signs_106:
  mov c, g
  mov b, a
  pop g
  pop a
; --- END FACTORS
  add32 cb, ga
  pop g
  pop a
; --- END TERMS
  pop d
  mov [d], b
; quad_y = x / 800;	/* Fixed point to int and divide by 8 */ 
  mov d, _quad_y ; $quad_y
  push d
  lea d, [bp + -23] ; $x
  mov b, [d]
  mov c, 0
; --- START FACTORS
  push a
  push g
  mov a, b
  mov g, c
  mov32 cb, $00000320
  push g ; save 'g' as the div instruction uses it
  div a, b ; /, a: quotient, b: remainder
  pop g
  mov c, g
  mov b, a
  pop g
  pop a
; --- END FACTORS
  pop d
  mov [d], b
; quad_x = y / 800;	/* Ditto */ 
  mov d, _quad_x ; $quad_x
  push d
  lea d, [bp + -25] ; $y
  mov b, [d]
  mov c, 0
; --- START FACTORS
  push a
  push g
  mov a, b
  mov g, c
  mov32 cb, $00000320
  push g ; save 'g' as the div instruction uses it
  div a, b ; /, a: quotient, b: remainder
  pop g
  mov c, g
  mov b, a
  pop g
  pop a
; --- END FACTORS
  pop d
  mov [d], b
; ship_y = x - (quad_y * 800); 
  mov d, _ship_y ; $ship_y
  push d
  lea d, [bp + -23] ; $x
  mov b, [d]
  mov c, 0
; --- START TERMS
  push a
  mov a, b
  mov d, _quad_y ; $quad_y
  mov b, [d]
  mov c, 0
; --- START FACTORS
  push a
  push g
  mov a, b
  mov g, c
  mov32 cb, $00000320
  push a     ; save left operand
  xor a, b   ; xor sign bits
  swp a      ; swap bytes
  mov cl, al ; save result of xor into 'dl'
  pop a      ; restore left side operator
  push cl    ; save result of xor above
  swp a  
  test al, $80  
  swp a  
  jz skip_invert_a_114  
  neg a 
skip_invert_a_114:   
  swp b
  test bl, $80  
  swp b
  jz skip_invert_b_114  
  neg b 
skip_invert_b_114:   
  mul a, b ; *
  mov g, a
  mov a, b
  pop bl
  test bl, $80
  jz _same_signs_114
  mov bl, al
  not a
  neg b
  adc a, 0
  mov g, a
  mov a, b
_same_signs_114:
  mov c, g
  mov b, a
  pop g
  pop a
; --- END FACTORS
  mov g, 0
  sub32 ga, cb
  mov b, a
  mov c, g
  pop a
; --- END TERMS
  pop d
  mov [d], b
; ship_x = y - (quad_x * 800); 
  mov d, _ship_x ; $ship_x
  push d
  lea d, [bp + -25] ; $y
  mov b, [d]
  mov c, 0
; --- START TERMS
  push a
  mov a, b
  mov d, _quad_x ; $quad_x
  mov b, [d]
  mov c, 0
; --- START FACTORS
  push a
  push g
  mov a, b
  mov g, c
  mov32 cb, $00000320
  push a     ; save left operand
  xor a, b   ; xor sign bits
  swp a      ; swap bytes
  mov cl, al ; save result of xor into 'dl'
  pop a      ; restore left side operator
  push cl    ; save result of xor above
  swp a  
  test al, $80  
  swp a  
  jz skip_invert_a_118  
  neg a 
skip_invert_a_118:   
  swp b
  test bl, $80  
  swp b
  jz skip_invert_b_118  
  neg b 
skip_invert_b_118:   
  mul a, b ; *
  mov g, a
  mov a, b
  pop bl
  test bl, $80
  jz _same_signs_118
  mov bl, al
  not a
  neg b
  adc a, 0
  mov g, a
  mov a, b
_same_signs_118:
  mov c, g
  mov b, a
  pop g
  pop a
; --- END FACTORS
  mov g, 0
  sub32 ga, cb
  mov b, a
  mov c, g
  pop a
; --- END TERMS
  pop d
  mov [d], b
; if (ship_y < 100) { 
_if119_cond:
  mov d, _ship_y ; $ship_y
  mov b, [d]
  mov c, 0
; --- START RELATIONAL
  push a
  mov a, b
  mov32 cb, $00000064
  cmp a, b
  slt ; < (signed)
  pop a
; --- END RELATIONAL
  cmp b, 0
  je _if119_exit
_if119_TRUE:
; quad_y = quad_y - 1; 
  mov d, _quad_y ; $quad_y
  push d
  mov d, _quad_y ; $quad_y
  mov b, [d]
  mov c, 0
; --- START TERMS
  push a
  mov a, b
  mov32 cb, $00000001
  sub a, b
  mov b, a
  pop a
; --- END TERMS
  pop d
  mov [d], b
; ship_y = ship_y + 800; 
  mov d, _ship_y ; $ship_y
  push d
  mov d, _ship_y ; $ship_y
  mov b, [d]
  mov c, 0
; --- START TERMS
  push a
  mov a, b
  mov32 cb, $00000320
  add b, a
  pop a
; --- END TERMS
  pop d
  mov [d], b
  jmp _if119_exit
_if119_exit:
; if (ship_x < 100) { 
_if120_cond:
  mov d, _ship_x ; $ship_x
  mov b, [d]
  mov c, 0
; --- START RELATIONAL
  push a
  mov a, b
  mov32 cb, $00000064
  cmp a, b
  slt ; < (signed)
  pop a
; --- END RELATIONAL
  cmp b, 0
  je _if120_exit
_if120_TRUE:
; quad_x = quad_x - 1; 
  mov d, _quad_x ; $quad_x
  push d
  mov d, _quad_x ; $quad_x
  mov b, [d]
  mov c, 0
; --- START TERMS
  push a
  mov a, b
  mov32 cb, $00000001
  sub a, b
  mov b, a
  pop a
; --- END TERMS
  pop d
  mov [d], b
; ship_x = ship_x + 800; 
  mov d, _ship_x ; $ship_x
  push d
  mov d, _ship_x ; $ship_x
  mov b, [d]
  mov c, 0
; --- START TERMS
  push a
  mov a, b
  mov32 cb, $00000320
  add b, a
  pop a
; --- END TERMS
  pop d
  mov [d], b
  jmp _if120_exit
_if120_exit:
; if (quad_y < 1) { 
_if121_cond:
  mov d, _quad_y ; $quad_y
  mov b, [d]
  mov c, 0
; --- START RELATIONAL
  push a
  mov a, b
  mov32 cb, $00000001
  cmp a, b
  slt ; < (signed)
  pop a
; --- END RELATIONAL
  cmp b, 0
  je _if121_exit
_if121_TRUE:
; outside = 1; 
  lea d, [bp + -26] ; $outside
  push d
  mov32 cb, $00000001
  pop d
  mov [d], bl
; quad_y = 1; 
  mov d, _quad_y ; $quad_y
  push d
  mov32 cb, $00000001
  pop d
  mov [d], b
; ship_y = 100; 
  mov d, _ship_y ; $ship_y
  push d
  mov32 cb, $00000064
  pop d
  mov [d], b
  jmp _if121_exit
_if121_exit:
; if (quad_y > 8) { 
_if122_cond:
  mov d, _quad_y ; $quad_y
  mov b, [d]
  mov c, 0
; --- START RELATIONAL
  push a
  mov a, b
  mov32 cb, $00000008
  cmp a, b
  sgt ; >
  pop a
; --- END RELATIONAL
  cmp b, 0
  je _if122_exit
_if122_TRUE:
; outside = 1; 
  lea d, [bp + -26] ; $outside
  push d
  mov32 cb, $00000001
  pop d
  mov [d], bl
; quad_y = 8; 
  mov d, _quad_y ; $quad_y
  push d
  mov32 cb, $00000008
  pop d
  mov [d], b
; ship_y = 800; 
  mov d, _ship_y ; $ship_y
  push d
  mov32 cb, $00000320
  pop d
  mov [d], b
  jmp _if122_exit
_if122_exit:
; if (quad_x < 1) { 
_if123_cond:
  mov d, _quad_x ; $quad_x
  mov b, [d]
  mov c, 0
; --- START RELATIONAL
  push a
  mov a, b
  mov32 cb, $00000001
  cmp a, b
  slt ; < (signed)
  pop a
; --- END RELATIONAL
  cmp b, 0
  je _if123_exit
_if123_TRUE:
; outside = 1; 
  lea d, [bp + -26] ; $outside
  push d
  mov32 cb, $00000001
  pop d
  mov [d], bl
; quad_x = 1; 
  mov d, _quad_x ; $quad_x
  push d
  mov32 cb, $00000001
  pop d
  mov [d], b
; ship_x = 100; 
  mov d, _ship_x ; $ship_x
  push d
  mov32 cb, $00000064
  pop d
  mov [d], b
  jmp _if123_exit
_if123_exit:
; if (quad_x > 8) { 
_if124_cond:
  mov d, _quad_x ; $quad_x
  mov b, [d]
  mov c, 0
; --- START RELATIONAL
  push a
  mov a, b
  mov32 cb, $00000008
  cmp a, b
  sgt ; >
  pop a
; --- END RELATIONAL
  cmp b, 0
  je _if124_exit
_if124_TRUE:
; outside = 1; 
  lea d, [bp + -26] ; $outside
  push d
  mov32 cb, $00000001
  pop d
  mov [d], bl
; quad_x = 8; 
  mov d, _quad_x ; $quad_x
  push d
  mov32 cb, $00000008
  pop d
  mov [d], b
; ship_x = 800; 
  mov d, _ship_x ; $ship_x
  push d
  mov32 cb, $00000320
  pop d
  mov [d], b
  jmp _if124_exit
_if124_exit:
; if (outside == 1) { 
_if125_cond:
  lea d, [bp + -26] ; $outside
  mov bl, [d]
  mov bh, 0
  mov c, 0
; --- START RELATIONAL
  push a
  mov a, b
  mov32 cb, $00000001
  cmp a, b
  seq ; ==
  pop a
; --- END RELATIONAL
  cmp b, 0
  je _if125_exit
_if125_TRUE:
; printf("LT. Uhura reports:\n Message from Starfleet Command:\n\n Permission to attempt crossing of galactic perimeter\n is hereby *denied*. Shut down your engines.\n\n Chief Engineer Scott reports:\n Warp Engines shut down at sector %d, %d of quadrant %d, %d.\n\n", FROM_FIXED00(ship_y), 
; --- START FUNCTION CALL
  mov d, _quad_x ; $quad_x
  mov b, [d]
  mov c, 0
  swp b
  push b
  mov d, _quad_y ; $quad_y
  mov b, [d]
  mov c, 0
  swp b
  push b
; --- START FUNCTION CALL
  mov d, _ship_x ; $ship_x
  mov b, [d]
  mov c, 0
  swp b
  push b
  call FROM_FIXED00
  add sp, 2
; --- END FUNCTION CALL
  swp b
  push b
; --- START FUNCTION CALL
  mov d, _ship_y ; $ship_y
  mov b, [d]
  mov c, 0
  swp b
  push b
  call FROM_FIXED00
  add sp, 2
; --- END FUNCTION CALL
  swp b
  push b
  mov b, _s71 ; "LT. Uhura reports:\n Message from Starfleet Command:\n\n Permission to attempt crossing of galactic perimeter\n is hereby *denied*. Shut down your engines.\n\n Chief Engineer Scott reports:\n Warp Engines shut down at sector %d, %d of quadrant %d, %d.\n\n"
  swp b
  push b
  call printf
  add sp, 10
; --- END FUNCTION CALL
  jmp _if125_exit
_if125_exit:
; maneuver_energy(n); 
; --- START FUNCTION CALL
  lea d, [bp + -7] ; $n
  mov b, [d]
  mov c, 0
  swp b
  push b
  call maneuver_energy
  add sp, 2
; --- END FUNCTION CALL
; if (FROM_FIXED(stardate) > time_start + time_up) 
_if126_cond:
; --- START FUNCTION CALL
  mov d, _stardate ; $stardate
  mov b, [d]
  mov c, 0
  swp b
  push b
  call FROM_FIXED
  add sp, 2
; --- END FUNCTION CALL
; --- START RELATIONAL
  push a
  mov a, b
  mov d, _time_start ; $time_start
  mov b, [d]
  mov c, 0
; --- START TERMS
  push a
  mov a, b
  mov d, _time_up ; $time_up
  mov b, [d]
  mov c, 0
  add b, a
  pop a
; --- END TERMS
  cmp a, b
  sgt ; >
  pop a
; --- END RELATIONAL
  cmp b, 0
  je _if126_exit
_if126_TRUE:
; end_of_time(); 
; --- START FUNCTION CALL
  call end_of_time
  jmp _if126_exit
_if126_exit:
; if (quad_y != quad_y_old || quad_x != quad_x_old) { 
_if127_cond:
  mov d, _quad_y ; $quad_y
  mov b, [d]
  mov c, 0
; --- START RELATIONAL
  push a
  mov a, b
  lea d, [bp + -27] ; $quad_y_old
  mov bl, [d]
  mov bh, 0
  mov c, 0
  cmp a, b
  sneq ; !=
  pop a
; --- END RELATIONAL
; --- START LOGICAL OR
  push a
  mov a, b
  mov d, _quad_x ; $quad_x
  mov b, [d]
  mov c, 0
; --- START RELATIONAL
  push a
  mov a, b
  lea d, [bp + -28] ; $quad_x_old
  mov bl, [d]
  mov bh, 0
  mov c, 0
  cmp a, b
  sneq ; !=
  pop a
; --- END RELATIONAL
  sor a, b ; ||
  pop a
; --- END LOGICAL OR
  cmp b, 0
  je _if127_exit
_if127_TRUE:
; stardate = stardate + TO_FIXED(1); 
  mov d, _stardate ; $stardate
  push d
  mov d, _stardate ; $stardate
  mov b, [d]
  mov c, 0
; --- START TERMS
  push a
  mov a, b
; --- START FUNCTION CALL
  mov32 cb, $00000001
  swp b
  push b
  call TO_FIXED
  add sp, 2
; --- END FUNCTION CALL
  add b, a
  pop a
; --- END TERMS
  pop d
  mov [d], b
; new_quadrant(); 
; --- START FUNCTION CALL
  call new_quadrant
  jmp _if127_exit
_if127_exit:
; complete_maneuver(warp, n); 
; --- START FUNCTION CALL
  lea d, [bp + -7] ; $n
  mov b, [d]
  mov c, 0
  swp b
  push b
  lea d, [bp + -5] ; $warp
  mov b, [d]
  mov c, 0
  swp b
  push b
  call complete_maneuver
  add sp, 4
; --- END FUNCTION CALL
; return; 
  leave
  ret
  jmp _if90_exit
_if90_exit:
; if (quad[z1+-1][z2+-1] != 		0       ) {	/* Sector not empty */ 
_if128_cond:
  mov d, _quad_data ; $quad
  push a
  push d
  lea d, [bp + -15] ; $z1
  mov b, [d]
  mov c, 0
; --- START TERMS
  push a
  mov a, b
  mov32 cb, $ffffffff
  add b, a
  pop a
; --- END TERMS
  pop d
  mma 8 ; mov a, 8; mul a, b; add d, b
  push d
  lea d, [bp + -17] ; $z2
  mov b, [d]
  mov c, 0
; --- START TERMS
  push a
  mov a, b
  mov32 cb, $ffffffff
  add b, a
  pop a
; --- END TERMS
  pop d
  add d, b
  pop a
  mov bl, [d]
  mov bh, 0
  mov c, 0
; --- START RELATIONAL
  push a
  mov a, b
  mov32 cb, $00000000
  cmp a, b
  sneq ; !=
  pop a
; --- END RELATIONAL
  cmp b, 0
  je _if128_exit
_if128_TRUE:
; ship_y = ship_y - x1; 
  mov d, _ship_y ; $ship_y
  push d
  mov d, _ship_y ; $ship_y
  mov b, [d]
  mov c, 0
; --- START TERMS
  push a
  mov a, b
  lea d, [bp + -19] ; $x1
  mov b, [d]
  mov c, 0
  sub a, b
  mov b, a
  pop a
; --- END TERMS
  pop d
  mov [d], b
; ship_x = ship_x - x2; 
  mov d, _ship_x ; $ship_x
  push d
  mov d, _ship_x ; $ship_x
  mov b, [d]
  mov c, 0
; --- START TERMS
  push a
  mov a, b
  lea d, [bp + -21] ; $x2
  mov b, [d]
  mov c, 0
  sub a, b
  mov b, a
  pop a
; --- END TERMS
  pop d
  mov [d], b
; printf("Warp Engines shut down at sector %d, %d due to bad navigation.\n\n", z1, z2); 
; --- START FUNCTION CALL
  lea d, [bp + -17] ; $z2
  mov b, [d]
  mov c, 0
  swp b
  push b
  lea d, [bp + -15] ; $z1
  mov b, [d]
  mov c, 0
  swp b
  push b
  mov b, _s72 ; "Warp Engines shut down at sector %d, %d due to bad navigation.\n\n"
  swp b
  push b
  call printf
  add sp, 6
; --- END FUNCTION CALL
; i = n + 1; 
  lea d, [bp + -1] ; $i
  push d
  lea d, [bp + -7] ; $n
  mov b, [d]
  mov c, 0
; --- START TERMS
  push a
  mov a, b
  mov32 cb, $00000001
  add b, a
  pop a
; --- END TERMS
  pop d
  mov [d], b
  jmp _if128_exit
_if128_exit:
_for89_update:
  lea d, [bp + -1] ; $i
  mov b, [d]
  mov c, 0
  mov a, b
  inc b
  lea d, [bp + -1] ; $i
  mov [d], b
  mov b, a
  jmp _for89_cond
_for89_exit:
; complete_maneuver(warp, n); 
; --- START FUNCTION CALL
  lea d, [bp + -7] ; $n
  mov b, [d]
  mov c, 0
  swp b
  push b
  lea d, [bp + -5] ; $warp
  mov b, [d]
  mov c, 0
  swp b
  push b
  call complete_maneuver
  add sp, 4
; --- END FUNCTION CALL
  leave
  ret

complete_maneuver:
  enter 0 ; (push bp; mov bp, sp)
; unsigned int         time_used; 
  sub sp, 2
; place_ship(); 
; --- START FUNCTION CALL
  call place_ship
; maneuver_energy(n); 
; --- START FUNCTION CALL
  lea d, [bp + 7] ; $n
  mov b, [d]
  mov c, 0
  swp b
  push b
  call maneuver_energy
  add sp, 2
; --- END FUNCTION CALL
; time_used = TO_FIXED(1); 
  lea d, [bp + -1] ; $time_used
  push d
; --- START FUNCTION CALL
  mov32 cb, $00000001
  swp b
  push b
  call TO_FIXED
  add sp, 2
; --- END FUNCTION CALL
  pop d
  mov [d], b
; if (warp < 100) 
_if129_cond:
  lea d, [bp + 5] ; $warp
  mov b, [d]
  mov c, 0
; --- START RELATIONAL
  push a
  mov a, b
  mov32 cb, $00000064
  cmp a, b
  slu ; < (unsigned)
  pop a
; --- END RELATIONAL
  cmp b, 0
  je _if129_exit
_if129_TRUE:
; time_used = TO_FIXED(FROM_FIXED00(warp)); 
  lea d, [bp + -1] ; $time_used
  push d
; --- START FUNCTION CALL
; --- START FUNCTION CALL
  lea d, [bp + 5] ; $warp
  mov b, [d]
  mov c, 0
  swp b
  push b
  call FROM_FIXED00
  add sp, 2
; --- END FUNCTION CALL
  swp b
  push b
  call TO_FIXED
  add sp, 2
; --- END FUNCTION CALL
  pop d
  mov [d], b
  jmp _if129_exit
_if129_exit:
; stardate = stardate + time_used; 
  mov d, _stardate ; $stardate
  push d
  mov d, _stardate ; $stardate
  mov b, [d]
  mov c, 0
; --- START TERMS
  push a
  mov a, b
  lea d, [bp + -1] ; $time_used
  mov b, [d]
  mov c, 0
  add b, a
  pop a
; --- END TERMS
  pop d
  mov [d], b
; if (FROM_FIXED(stardate) > time_start + time_up) 
_if130_cond:
; --- START FUNCTION CALL
  mov d, _stardate ; $stardate
  mov b, [d]
  mov c, 0
  swp b
  push b
  call FROM_FIXED
  add sp, 2
; --- END FUNCTION CALL
; --- START RELATIONAL
  push a
  mov a, b
  mov d, _time_start ; $time_start
  mov b, [d]
  mov c, 0
; --- START TERMS
  push a
  mov a, b
  mov d, _time_up ; $time_up
  mov b, [d]
  mov c, 0
  add b, a
  pop a
; --- END TERMS
  cmp a, b
  sgt ; >
  pop a
; --- END RELATIONAL
  cmp b, 0
  je _if130_exit
_if130_TRUE:
; end_of_time(); 
; --- START FUNCTION CALL
  call end_of_time
  jmp _if130_exit
_if130_exit:
; short_range_scan(); 
; --- START FUNCTION CALL
  call short_range_scan
  leave
  ret

maneuver_energy:
  enter 0 ; (push bp; mov bp, sp)
; energy = energy - n + 10; 
  mov d, _energy ; $energy
  push d
  mov d, _energy ; $energy
  mov b, [d]
  mov c, 0
; --- START TERMS
  push a
  mov a, b
  lea d, [bp + 5] ; $n
  mov b, [d]
  mov c, 0
  sub a, b
  mov b, a
  mov a, b
  mov32 cb, $0000000a
  add b, a
  pop a
; --- END TERMS
  pop d
  mov [d], b
; if (energy >= 0) 
_if131_cond:
  mov d, _energy ; $energy
  mov b, [d]
  mov c, 0
; --- START RELATIONAL
  push a
  mov a, b
  mov32 cb, $00000000
  cmp a, b
  sge ; >=
  pop a
; --- END RELATIONAL
  cmp b, 0
  je _if131_exit
_if131_TRUE:
; return; 
  leave
  ret
  jmp _if131_exit
_if131_exit:
; puts("Shield Control supplies energy to complete maneuver.\n"); 
; --- START FUNCTION CALL
  mov b, _s73 ; "Shield Control supplies energy to complete maneuver.\n"
  swp b
  push b
  call puts
  add sp, 2
; --- END FUNCTION CALL
; shield = shield + energy; 
  mov d, _shield ; $shield
  push d
  mov d, _shield ; $shield
  mov b, [d]
  mov c, 0
; --- START TERMS
  push a
  mov a, b
  mov d, _energy ; $energy
  mov b, [d]
  mov c, 0
  add b, a
  pop a
; --- END TERMS
  pop d
  mov [d], b
; energy = 0; 
  mov d, _energy ; $energy
  push d
  mov32 cb, $00000000
  pop d
  mov [d], b
; if (shield <= 0) 
_if132_cond:
  mov d, _shield ; $shield
  mov b, [d]
  mov c, 0
; --- START RELATIONAL
  push a
  mov a, b
  mov32 cb, $00000000
  cmp a, b
  sle ; <= (signed)
  pop a
; --- END RELATIONAL
  cmp b, 0
  je _if132_exit
_if132_TRUE:
; shield = 0; 
  mov d, _shield ; $shield
  push d
  mov32 cb, $00000000
  pop d
  mov [d], b
  jmp _if132_exit
_if132_exit:
  leave
  ret

short_range_scan:
  enter 0 ; (push bp; mov bp, sp)
; int i, j; 
  sub sp, 2
  sub sp, 2
; char *sC = "GREEN"; 
  sub sp, 2
; --- START LOCAL VAR INITIALIZATION
  lea d, [bp + -5] ; $sC
  push d
  mov b, _s74 ; "GREEN"
  pop d
  mov [d], b
; --- END LOCAL VAR INITIALIZATION
; if (energy < energy0 / 10) 
_if133_cond:
  mov d, _energy ; $energy
  mov b, [d]
  mov c, 0
; --- START RELATIONAL
  push a
  mov a, b
  mov d, _energy0 ; $energy0
  mov b, [d]
  mov c, 0
; --- START FACTORS
  push a
  push g
  mov a, b
  mov g, c
  mov32 cb, $0000000a
  push g ; save 'g' as the div instruction uses it
  div a, b ; /, a: quotient, b: remainder
  pop g
  mov c, g
  mov b, a
  pop g
  pop a
; --- END FACTORS
  cmp a, b
  slt ; < (signed)
  pop a
; --- END RELATIONAL
  cmp b, 0
  je _if133_exit
_if133_TRUE:
; sC = "YELLOW"; 
  lea d, [bp + -5] ; $sC
  push d
  mov b, _s75 ; "YELLOW"
  pop d
  mov [d], b
  jmp _if133_exit
_if133_exit:
; if (klingons > 0) 
_if136_cond:
  mov d, _klingons ; $klingons
  mov bl, [d]
  mov bh, 0
  mov c, 0
; --- START RELATIONAL
  push a
  mov a, b
  mov32 cb, $00000000
  cmp a, b
  sgu ; > (unsigned)
  pop a
; --- END RELATIONAL
  cmp b, 0
  je _if136_exit
_if136_TRUE:
; sC = "*RED*"; 
  lea d, [bp + -5] ; $sC
  push d
  mov b, _s76 ; "*RED*"
  pop d
  mov [d], b
  jmp _if136_exit
_if136_exit:
; docked = 0; 
  mov d, _docked ; $docked
  push d
  mov32 cb, $00000000
  pop d
  mov [d], bl
; for (i = (int) (FROM_FIXED00(ship_y) - 1); i <= (int) (FROM_FIXED00(ship_y) + 1); i++) 
_for137_init:
  lea d, [bp + -1] ; $i
  push d
; --- START FUNCTION CALL
  mov d, _ship_y ; $ship_y
  mov b, [d]
  mov c, 0
  swp b
  push b
  call FROM_FIXED00
  add sp, 2
; --- END FUNCTION CALL
; --- START TERMS
  push a
  mov a, b
  mov32 cb, $00000001
  sub a, b
  mov b, a
  pop a
; --- END TERMS
  pop d
  mov [d], b
_for137_cond:
  lea d, [bp + -1] ; $i
  mov b, [d]
  mov c, 0
; --- START RELATIONAL
  push a
  mov a, b
; --- START FUNCTION CALL
  mov d, _ship_y ; $ship_y
  mov b, [d]
  mov c, 0
  swp b
  push b
  call FROM_FIXED00
  add sp, 2
; --- END FUNCTION CALL
; --- START TERMS
  push a
  mov a, b
  mov32 cb, $00000001
  add b, a
  pop a
; --- END TERMS
  cmp a, b
  sle ; <= (signed)
  pop a
; --- END RELATIONAL
  cmp b, 0
  je _for137_exit
_for137_block:
; for (j = (int) (FROM_FIXED00(ship_x) - 1); j <= (int) (FROM_FIXED00(ship_x) + 1); j++) 
_for138_init:
  lea d, [bp + -3] ; $j
  push d
; --- START FUNCTION CALL
  mov d, _ship_x ; $ship_x
  mov b, [d]
  mov c, 0
  swp b
  push b
  call FROM_FIXED00
  add sp, 2
; --- END FUNCTION CALL
; --- START TERMS
  push a
  mov a, b
  mov32 cb, $00000001
  sub a, b
  mov b, a
  pop a
; --- END TERMS
  pop d
  mov [d], b
_for138_cond:
  lea d, [bp + -3] ; $j
  mov b, [d]
  mov c, 0
; --- START RELATIONAL
  push a
  mov a, b
; --- START FUNCTION CALL
  mov d, _ship_x ; $ship_x
  mov b, [d]
  mov c, 0
  swp b
  push b
  call FROM_FIXED00
  add sp, 2
; --- END FUNCTION CALL
; --- START TERMS
  push a
  mov a, b
  mov32 cb, $00000001
  add b, a
  pop a
; --- END TERMS
  cmp a, b
  sle ; <= (signed)
  pop a
; --- END RELATIONAL
  cmp b, 0
  je _for138_exit
_for138_block:
; if (i >= 1 && i <= 8 && j >= 1 && j <= 8) { 
_if139_cond:
  lea d, [bp + -1] ; $i
  mov b, [d]
  mov c, 0
; --- START RELATIONAL
  push a
  mov a, b
  mov32 cb, $00000001
  cmp a, b
  sge ; >=
  pop a
; --- END RELATIONAL
; --- START LOGICAL AND
  push a
  mov a, b
  lea d, [bp + -1] ; $i
  mov b, [d]
  mov c, 0
; --- START RELATIONAL
  push a
  mov a, b
  mov32 cb, $00000008
  cmp a, b
  sle ; <= (signed)
  pop a
; --- END RELATIONAL
  sand a, b
  mov a, b
  lea d, [bp + -3] ; $j
  mov b, [d]
  mov c, 0
; --- START RELATIONAL
  push a
  mov a, b
  mov32 cb, $00000001
  cmp a, b
  sge ; >=
  pop a
; --- END RELATIONAL
  sand a, b
  mov a, b
  lea d, [bp + -3] ; $j
  mov b, [d]
  mov c, 0
; --- START RELATIONAL
  push a
  mov a, b
  mov32 cb, $00000008
  cmp a, b
  sle ; <= (signed)
  pop a
; --- END RELATIONAL
  sand a, b
  pop a
; --- END LOGICAL AND
  cmp b, 0
  je _if139_exit
_if139_TRUE:
; if (quad[i+-1][j+-1] == 		2      ) { 
_if140_cond:
  mov d, _quad_data ; $quad
  push a
  push d
  lea d, [bp + -1] ; $i
  mov b, [d]
  mov c, 0
; --- START TERMS
  push a
  mov a, b
  mov32 cb, $ffffffff
  add b, a
  pop a
; --- END TERMS
  pop d
  mma 8 ; mov a, 8; mul a, b; add d, b
  push d
  lea d, [bp + -3] ; $j
  mov b, [d]
  mov c, 0
; --- START TERMS
  push a
  mov a, b
  mov32 cb, $ffffffff
  add b, a
  pop a
; --- END TERMS
  pop d
  add d, b
  pop a
  mov bl, [d]
  mov bh, 0
  mov c, 0
; --- START RELATIONAL
  push a
  mov a, b
  mov32 cb, $00000002
  cmp a, b
  seq ; ==
  pop a
; --- END RELATIONAL
  cmp b, 0
  je _if140_exit
_if140_TRUE:
; docked = 1; 
  mov d, _docked ; $docked
  push d
  mov32 cb, $00000001
  pop d
  mov [d], bl
; sC = "DOCKED"; 
  lea d, [bp + -5] ; $sC
  push d
  mov b, _s77 ; "DOCKED"
  pop d
  mov [d], b
; energy = energy0; 
  mov d, _energy ; $energy
  push d
  mov d, _energy0 ; $energy0
  mov b, [d]
  mov c, 0
  pop d
  mov [d], b
; torps = torps0; 
  mov d, _torps ; $torps
  push d
  mov d, _torps0 ; $torps0
  mov bl, [d]
  mov bh, 0
  mov c, 0
  pop d
  mov [d], bl
; puts("Shields dropped for docking purposes."); 
; --- START FUNCTION CALL
  mov b, _s78 ; "Shields dropped for docking purposes."
  swp b
  push b
  call puts
  add sp, 2
; --- END FUNCTION CALL
; shield = 0; 
  mov d, _shield ; $shield
  push d
  mov32 cb, $00000000
  pop d
  mov [d], b
  jmp _if140_exit
_if140_exit:
  jmp _if139_exit
_if139_exit:
_for138_update:
  lea d, [bp + -3] ; $j
  mov b, [d]
  mov c, 0
  mov a, b
  inc b
  lea d, [bp + -3] ; $j
  mov [d], b
  mov b, a
  jmp _for138_cond
_for138_exit:
_for137_update:
  lea d, [bp + -1] ; $i
  mov b, [d]
  mov c, 0
  mov a, b
  inc b
  lea d, [bp + -1] ; $i
  mov [d], b
  mov b, a
  jmp _for137_cond
_for137_exit:
; if (damage[2] < 0) { 
_if141_cond:
  mov d, _damage_data ; $damage
  push a
  push d
  mov32 cb, $00000002
  pop d
  mma 2 ; mov a, 2; mul a, b; add d, b
  pop a
  mov b, [d]
  mov c, 0
; --- START RELATIONAL
  push a
  mov a, b
  mov32 cb, $00000000
  cmp a, b
  slt ; < (signed)
  pop a
; --- END RELATIONAL
  cmp b, 0
  je _if141_exit
_if141_TRUE:
; puts("\n*** Short Range Sensors are out ***"); 
; --- START FUNCTION CALL
  mov b, _s79 ; "\n*** Short Range Sensors are out ***"
  swp b
  push b
  call puts
  add sp, 2
; --- END FUNCTION CALL
; return; 
  leave
  ret
  jmp _if141_exit
_if141_exit:
; puts(srs_1); 
; --- START FUNCTION CALL
  mov d, _srs_1 ; $srs_1
  mov b, [d]
  mov c, 0
  swp b
  push b
  call puts
  add sp, 2
; --- END FUNCTION CALL
; for (i = 0; i < 8; i++) { 
_for142_init:
  lea d, [bp + -1] ; $i
  push d
  mov32 cb, $00000000
  pop d
  mov [d], b
_for142_cond:
  lea d, [bp + -1] ; $i
  mov b, [d]
  mov c, 0
; --- START RELATIONAL
  push a
  mov a, b
  mov32 cb, $00000008
  cmp a, b
  slt ; < (signed)
  pop a
; --- END RELATIONAL
  cmp b, 0
  je _for142_exit
_for142_block:
; for (j = 0; j < 8; j++) 
_for143_init:
  lea d, [bp + -3] ; $j
  push d
  mov32 cb, $00000000
  pop d
  mov [d], b
_for143_cond:
  lea d, [bp + -3] ; $j
  mov b, [d]
  mov c, 0
; --- START RELATIONAL
  push a
  mov a, b
  mov32 cb, $00000008
  cmp a, b
  slt ; < (signed)
  pop a
; --- END RELATIONAL
  cmp b, 0
  je _for143_exit
_for143_block:
; puts(tilestr[quad[i][j]]); 
; --- START FUNCTION CALL
  mov d, _tilestr_data ; $tilestr
  push a
  push d
  mov d, _quad_data ; $quad
  push a
  push d
  lea d, [bp + -1] ; $i
  mov b, [d]
  mov c, 0
  pop d
  mma 8 ; mov a, 8; mul a, b; add d, b
  push d
  lea d, [bp + -3] ; $j
  mov b, [d]
  mov c, 0
  pop d
  add d, b
  pop a
  mov bl, [d]
  mov bh, 0
  mov c, 0
  pop d
  mma 2 ; mov a, 2; mul a, b; add d, b
  pop a
  mov b, [d]
  mov c, 0
  swp b
  push b
  call puts
  add sp, 2
; --- END FUNCTION CALL
_for143_update:
  lea d, [bp + -3] ; $j
  mov b, [d]
  mov c, 0
  mov a, b
  inc b
  lea d, [bp + -3] ; $j
  mov [d], b
  mov b, a
  jmp _for143_cond
_for143_exit:
; if (i == 0) 
_if144_cond:
  lea d, [bp + -1] ; $i
  mov b, [d]
  mov c, 0
; --- START RELATIONAL
  push a
  mov a, b
  mov32 cb, $00000000
  cmp a, b
  seq ; ==
  pop a
; --- END RELATIONAL
  cmp b, 0
  je _if144_exit
_if144_TRUE:
; printf("    Stardate            %d\n", FROM_FIXED(stardate)); 
; --- START FUNCTION CALL
; --- START FUNCTION CALL
  mov d, _stardate ; $stardate
  mov b, [d]
  mov c, 0
  swp b
  push b
  call FROM_FIXED
  add sp, 2
; --- END FUNCTION CALL
  swp b
  push b
  mov b, _s80 ; "    Stardate            %d\n"
  swp b
  push b
  call printf
  add sp, 4
; --- END FUNCTION CALL
  jmp _if144_exit
_if144_exit:
; if (i == 1) 
_if145_cond:
  lea d, [bp + -1] ; $i
  mov b, [d]
  mov c, 0
; --- START RELATIONAL
  push a
  mov a, b
  mov32 cb, $00000001
  cmp a, b
  seq ; ==
  pop a
; --- END RELATIONAL
  cmp b, 0
  je _if145_exit
_if145_TRUE:
; printf("    Condition           %s\n", sC); 
; --- START FUNCTION CALL
  lea d, [bp + -5] ; $sC
  mov b, [d]
  mov c, 0
  swp b
  push b
  mov b, _s81 ; "    Condition           %s\n"
  swp b
  push b
  call printf
  add sp, 4
; --- END FUNCTION CALL
  jmp _if145_exit
_if145_exit:
; if (i == 2) 
_if146_cond:
  lea d, [bp + -1] ; $i
  mov b, [d]
  mov c, 0
; --- START RELATIONAL
  push a
  mov a, b
  mov32 cb, $00000002
  cmp a, b
  seq ; ==
  pop a
; --- END RELATIONAL
  cmp b, 0
  je _if146_exit
_if146_TRUE:
; printf("    Quadrant            %d, %d\n", quad_y, quad_x); 
; --- START FUNCTION CALL
  mov d, _quad_x ; $quad_x
  mov b, [d]
  mov c, 0
  swp b
  push b
  mov d, _quad_y ; $quad_y
  mov b, [d]
  mov c, 0
  swp b
  push b
  mov b, _s82 ; "    Quadrant            %d, %d\n"
  swp b
  push b
  call printf
  add sp, 6
; --- END FUNCTION CALL
  jmp _if146_exit
_if146_exit:
; if (i == 3) 
_if147_cond:
  lea d, [bp + -1] ; $i
  mov b, [d]
  mov c, 0
; --- START RELATIONAL
  push a
  mov a, b
  mov32 cb, $00000003
  cmp a, b
  seq ; ==
  pop a
; --- END RELATIONAL
  cmp b, 0
  je _if147_exit
_if147_TRUE:
; printf("    Sector              %d, %d\n", FROM_FIXED00(ship_y), FROM_FIXED00(ship_x)); 
; --- START FUNCTION CALL
; --- START FUNCTION CALL
  mov d, _ship_x ; $ship_x
  mov b, [d]
  mov c, 0
  swp b
  push b
  call FROM_FIXED00
  add sp, 2
; --- END FUNCTION CALL
  swp b
  push b
; --- START FUNCTION CALL
  mov d, _ship_y ; $ship_y
  mov b, [d]
  mov c, 0
  swp b
  push b
  call FROM_FIXED00
  add sp, 2
; --- END FUNCTION CALL
  swp b
  push b
  mov b, _s83 ; "    Sector              %d, %d\n"
  swp b
  push b
  call printf
  add sp, 6
; --- END FUNCTION CALL
  jmp _if147_exit
_if147_exit:
; if (i == 4) 
_if148_cond:
  lea d, [bp + -1] ; $i
  mov b, [d]
  mov c, 0
; --- START RELATIONAL
  push a
  mov a, b
  mov32 cb, $00000004
  cmp a, b
  seq ; ==
  pop a
; --- END RELATIONAL
  cmp b, 0
  je _if148_exit
_if148_TRUE:
; printf("    Photon Torpedoes    %d\n", torps); 
; --- START FUNCTION CALL
  mov d, _torps ; $torps
  mov bl, [d]
  mov bh, 0
  mov c, 0
  swp b
  push b
  mov b, _s84 ; "    Photon Torpedoes    %d\n"
  swp b
  push b
  call printf
  add sp, 3
; --- END FUNCTION CALL
  jmp _if148_exit
_if148_exit:
; if (i == 5) 
_if149_cond:
  lea d, [bp + -1] ; $i
  mov b, [d]
  mov c, 0
; --- START RELATIONAL
  push a
  mov a, b
  mov32 cb, $00000005
  cmp a, b
  seq ; ==
  pop a
; --- END RELATIONAL
  cmp b, 0
  je _if149_exit
_if149_TRUE:
; printf("    Total Energy        %d\n", energy + shield); 
; --- START FUNCTION CALL
  mov d, _energy ; $energy
  mov b, [d]
  mov c, 0
; --- START TERMS
  push a
  mov a, b
  mov d, _shield ; $shield
  mov b, [d]
  mov c, 0
  add b, a
  pop a
; --- END TERMS
  swp b
  push b
  mov b, _s85 ; "    Total Energy        %d\n"
  swp b
  push b
  call printf
  add sp, 4
; --- END FUNCTION CALL
  jmp _if149_exit
_if149_exit:
; if (i == 6) 
_if150_cond:
  lea d, [bp + -1] ; $i
  mov b, [d]
  mov c, 0
; --- START RELATIONAL
  push a
  mov a, b
  mov32 cb, $00000006
  cmp a, b
  seq ; ==
  pop a
; --- END RELATIONAL
  cmp b, 0
  je _if150_exit
_if150_TRUE:
; printf("    Shields             %d\n", shield); 
; --- START FUNCTION CALL
  mov d, _shield ; $shield
  mov b, [d]
  mov c, 0
  swp b
  push b
  mov b, _s86 ; "    Shields             %d\n"
  swp b
  push b
  call printf
  add sp, 4
; --- END FUNCTION CALL
  jmp _if150_exit
_if150_exit:
; if (i == 7) 
_if151_cond:
  lea d, [bp + -1] ; $i
  mov b, [d]
  mov c, 0
; --- START RELATIONAL
  push a
  mov a, b
  mov32 cb, $00000007
  cmp a, b
  seq ; ==
  pop a
; --- END RELATIONAL
  cmp b, 0
  je _if151_exit
_if151_TRUE:
; printf("    Klingons Remaining  %d\n", klingons_left); 
; --- START FUNCTION CALL
  mov d, _klingons_left ; $klingons_left
  mov bl, [d]
  mov bh, 0
  mov c, 0
  swp b
  push b
  mov b, _s87 ; "    Klingons Remaining  %d\n"
  swp b
  push b
  call printf
  add sp, 3
; --- END FUNCTION CALL
  jmp _if151_exit
_if151_exit:
_for142_update:
  lea d, [bp + -1] ; $i
  mov b, [d]
  mov c, 0
  mov a, b
  inc b
  lea d, [bp + -1] ; $i
  mov [d], b
  mov b, a
  jmp _for142_cond
_for142_exit:
; puts(srs_1); 
; --- START FUNCTION CALL
  mov d, _srs_1 ; $srs_1
  mov b, [d]
  mov c, 0
  swp b
  push b
  call puts
  add sp, 2
; --- END FUNCTION CALL
; putchar('\n'); 
; --- START FUNCTION CALL
  mov32 cb, $0000000a
  push bl
  call putchar
  add sp, 1
; --- END FUNCTION CALL
; return; 
  leave
  ret

put1bcd:
  enter 0 ; (push bp; mov bp, sp)
; v = v & 0x0F; 
  lea d, [bp + 5] ; $v
  push d
  lea d, [bp + 5] ; $v
  mov bl, [d]
  mov bh, 0
  mov c, 0
  push a
  mov a, b
  mov32 cb, $0000000f
  and b, a ; &
  pop a
  pop d
  mov [d], bl
; putchar('0' + v); 
; --- START FUNCTION CALL
  mov32 cb, $00000030
; --- START TERMS
  push a
  mov a, b
  lea d, [bp + 5] ; $v
  mov bl, [d]
  mov bh, 0
  mov c, 0
  add b, a
  pop a
; --- END TERMS
  push bl
  call putchar
  add sp, 1
; --- END FUNCTION CALL
  leave
  ret

putbcd:
  enter 0 ; (push bp; mov bp, sp)
; put1bcd(x >> 8); 
; --- START FUNCTION CALL
  lea d, [bp + 5] ; $x
  mov b, [d]
  mov c, 0
; --- START SHIFT
  push a
  mov a, b
  mov32 cb, $00000008
  mov c, b
  shr a, cl
  mov b, a
  pop a
; --- END SHIFT
  push bl
  call put1bcd
  add sp, 1
; --- END FUNCTION CALL
; put1bcd(x >> 4); 
; --- START FUNCTION CALL
  lea d, [bp + 5] ; $x
  mov b, [d]
  mov c, 0
; --- START SHIFT
  push a
  mov a, b
  mov32 cb, $00000004
  mov c, b
  shr a, cl
  mov b, a
  pop a
; --- END SHIFT
  push bl
  call put1bcd
  add sp, 1
; --- END FUNCTION CALL
; put1bcd(x); 
; --- START FUNCTION CALL
  lea d, [bp + 5] ; $x
  mov b, [d]
  mov c, 0
  push bl
  call put1bcd
  add sp, 1
; --- END FUNCTION CALL
  leave
  ret

long_range_scan:
  enter 0 ; (push bp; mov bp, sp)
; int i, j; 
  sub sp, 2
  sub sp, 2
; if (inoperable(3)) 
_if152_cond:
; --- START FUNCTION CALL
  mov32 cb, $00000003
  push bl
  call inoperable
  add sp, 1
; --- END FUNCTION CALL
  cmp b, 0
  je _if152_exit
_if152_TRUE:
; return; 
  leave
  ret
  jmp _if152_exit
_if152_exit:
; printf("Long Range Scan for Quadrant %d, %d\n\n", quad_y, quad_x); 
; --- START FUNCTION CALL
  mov d, _quad_x ; $quad_x
  mov b, [d]
  mov c, 0
  swp b
  push b
  mov d, _quad_y ; $quad_y
  mov b, [d]
  mov c, 0
  swp b
  push b
  mov b, _s88 ; "Long Range Scan for Quadrant %d, %d\n\n"
  swp b
  push b
  call printf
  add sp, 6
; --- END FUNCTION CALL
; for (i = quad_y - 1; i <= quad_y + 1; i++) { 
_for153_init:
  lea d, [bp + -1] ; $i
  push d
  mov d, _quad_y ; $quad_y
  mov b, [d]
  mov c, 0
; --- START TERMS
  push a
  mov a, b
  mov32 cb, $00000001
  sub a, b
  mov b, a
  pop a
; --- END TERMS
  pop d
  mov [d], b
_for153_cond:
  lea d, [bp + -1] ; $i
  mov b, [d]
  mov c, 0
; --- START RELATIONAL
  push a
  mov a, b
  mov d, _quad_y ; $quad_y
  mov b, [d]
  mov c, 0
; --- START TERMS
  push a
  mov a, b
  mov32 cb, $00000001
  add b, a
  pop a
; --- END TERMS
  cmp a, b
  sle ; <= (signed)
  pop a
; --- END RELATIONAL
  cmp b, 0
  je _for153_exit
_for153_block:
; printf("%s:", lrs_1); 
; --- START FUNCTION CALL
  mov d, _lrs_1 ; $lrs_1
  mov b, [d]
  mov c, 0
  swp b
  push b
  mov b, _s89 ; "%s:"
  swp b
  push b
  call printf
  add sp, 4
; --- END FUNCTION CALL
; for (j = quad_x - 1; j <= quad_x + 1; j++) { 
_for154_init:
  lea d, [bp + -3] ; $j
  push d
  mov d, _quad_x ; $quad_x
  mov b, [d]
  mov c, 0
; --- START TERMS
  push a
  mov a, b
  mov32 cb, $00000001
  sub a, b
  mov b, a
  pop a
; --- END TERMS
  pop d
  mov [d], b
_for154_cond:
  lea d, [bp + -3] ; $j
  mov b, [d]
  mov c, 0
; --- START RELATIONAL
  push a
  mov a, b
  mov d, _quad_x ; $quad_x
  mov b, [d]
  mov c, 0
; --- START TERMS
  push a
  mov a, b
  mov32 cb, $00000001
  add b, a
  pop a
; --- END TERMS
  cmp a, b
  sle ; <= (signed)
  pop a
; --- END RELATIONAL
  cmp b, 0
  je _for154_exit
_for154_block:
; putchar(' '); 
; --- START FUNCTION CALL
  mov32 cb, $00000020
  push bl
  call putchar
  add sp, 1
; --- END FUNCTION CALL
; if (i > 0 && i <= 8 && j > 0 && j <= 8) { 
_if155_cond:
  lea d, [bp + -1] ; $i
  mov b, [d]
  mov c, 0
; --- START RELATIONAL
  push a
  mov a, b
  mov32 cb, $00000000
  cmp a, b
  sgt ; >
  pop a
; --- END RELATIONAL
; --- START LOGICAL AND
  push a
  mov a, b
  lea d, [bp + -1] ; $i
  mov b, [d]
  mov c, 0
; --- START RELATIONAL
  push a
  mov a, b
  mov32 cb, $00000008
  cmp a, b
  sle ; <= (signed)
  pop a
; --- END RELATIONAL
  sand a, b
  mov a, b
  lea d, [bp + -3] ; $j
  mov b, [d]
  mov c, 0
; --- START RELATIONAL
  push a
  mov a, b
  mov32 cb, $00000000
  cmp a, b
  sgt ; >
  pop a
; --- END RELATIONAL
  sand a, b
  mov a, b
  lea d, [bp + -3] ; $j
  mov b, [d]
  mov c, 0
; --- START RELATIONAL
  push a
  mov a, b
  mov32 cb, $00000008
  cmp a, b
  sle ; <= (signed)
  pop a
; --- END RELATIONAL
  sand a, b
  pop a
; --- END LOGICAL AND
  cmp b, 0
  je _if155_else
_if155_TRUE:
; map[i][j] = map[i][j] |  0x1000		           ; 
  mov d, _map_data ; $map
  push a
  push d
  lea d, [bp + -1] ; $i
  mov b, [d]
  mov c, 0
  pop d
  mma 18 ; mov a, 18; mul a, b; add d, b
  push d
  lea d, [bp + -3] ; $j
  mov b, [d]
  mov c, 0
  pop d
  mma 2 ; mov a, 2; mul a, b; add d, b
  pop a
  push d
  mov d, _map_data ; $map
  push a
  push d
  lea d, [bp + -1] ; $i
  mov b, [d]
  mov c, 0
  pop d
  mma 18 ; mov a, 18; mul a, b; add d, b
  push d
  lea d, [bp + -3] ; $j
  mov b, [d]
  mov c, 0
  pop d
  mma 2 ; mov a, 2; mul a, b; add d, b
  pop a
  mov b, [d]
  mov c, 0
  push a
  mov a, b
  mov32 cb, $00001000
  or b, a ; |
  pop a
  pop d
  mov [d], b
; putbcd(map[i][j]); 
; --- START FUNCTION CALL
  mov d, _map_data ; $map
  push a
  push d
  lea d, [bp + -1] ; $i
  mov b, [d]
  mov c, 0
  pop d
  mma 18 ; mov a, 18; mul a, b; add d, b
  push d
  lea d, [bp + -3] ; $j
  mov b, [d]
  mov c, 0
  pop d
  mma 2 ; mov a, 2; mul a, b; add d, b
  pop a
  mov b, [d]
  mov c, 0
  swp b
  push b
  call putbcd
  add sp, 2
; --- END FUNCTION CALL
  jmp _if155_exit
_if155_else:
; puts("***"); 
; --- START FUNCTION CALL
  mov b, _s90 ; "***"
  swp b
  push b
  call puts
  add sp, 2
; --- END FUNCTION CALL
_if155_exit:
; puts(" :"); 
; --- START FUNCTION CALL
  mov b, _s91 ; " :"
  swp b
  push b
  call puts
  add sp, 2
; --- END FUNCTION CALL
_for154_update:
  lea d, [bp + -3] ; $j
  mov b, [d]
  mov c, 0
  mov a, b
  inc b
  lea d, [bp + -3] ; $j
  mov [d], b
  mov b, a
  jmp _for154_cond
_for154_exit:
; putchar('\n'); 
; --- START FUNCTION CALL
  mov32 cb, $0000000a
  push bl
  call putchar
  add sp, 1
; --- END FUNCTION CALL
_for153_update:
  lea d, [bp + -1] ; $i
  mov b, [d]
  mov c, 0
  mov a, b
  inc b
  lea d, [bp + -1] ; $i
  mov [d], b
  mov b, a
  jmp _for153_cond
_for153_exit:
; printf("%s\n", lrs_1); 
; --- START FUNCTION CALL
  mov d, _lrs_1 ; $lrs_1
  mov b, [d]
  mov c, 0
  swp b
  push b
  mov b, _s92 ; "%s\n"
  swp b
  push b
  call printf
  add sp, 4
; --- END FUNCTION CALL
  leave
  ret

no_klingon:
  enter 0 ; (push bp; mov bp, sp)
; if (klingons <= 0) { 
_if156_cond:
  mov d, _klingons ; $klingons
  mov bl, [d]
  mov bh, 0
  mov c, 0
; --- START RELATIONAL
  push a
  mov a, b
  mov32 cb, $00000000
  cmp a, b
  sleu ; <= (unsigned)
  pop a
; --- END RELATIONAL
  cmp b, 0
  je _if156_exit
_if156_TRUE:
; puts("Science Officer Spock reports:\n  'Sensors show no enemy ships in this quadrant'\n"); 
; --- START FUNCTION CALL
  mov b, _s93 ; "Science Officer Spock reports:\n  'Sensors show no enemy ships in this quadrant'\n"
  swp b
  push b
  call puts
  add sp, 2
; --- END FUNCTION CALL
; return 1; 
  mov32 cb, $00000001
  leave
  ret
  jmp _if156_exit
_if156_exit:
; return 0; 
  mov32 cb, $00000000
  leave
  ret

wipe_klingon:
  enter 0 ; (push bp; mov bp, sp)
; quad[k->y+-1][k->x+-1] = 		0       ; 
  mov d, _quad_data ; $quad
  push a
  push d
  lea d, [bp + 5] ; $k
  mov d, [d]
  add d, 0
  mov bl, [d]
  mov bh, 0
  mov c, 0
; --- START TERMS
  push a
  mov a, b
  mov32 cb, $ffffffff
  add b, a
  pop a
; --- END TERMS
  pop d
  mma 8 ; mov a, 8; mul a, b; add d, b
  push d
  lea d, [bp + 5] ; $k
  mov d, [d]
  add d, 1
  mov bl, [d]
  mov bh, 0
  mov c, 0
; --- START TERMS
  push a
  mov a, b
  mov32 cb, $ffffffff
  add b, a
  pop a
; --- END TERMS
  pop d
  add d, b
  pop a
  push d
  mov32 cb, $00000000
  pop d
  mov [d], bl
  leave
  ret
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
