stanley-fork/sol-1/general_docs/5.25_floppy_drive/romWBW_scottbaker/rc2014_baker/fd (1).asm

; Floppy Disk Driver from N8VEM project RomWBW
; Modifications to work with zasm, and to separate it from the rest of N8VEM
;
; Original Readme Banner:
;
; ************************************************************
; ***                     R o m W B W                      ***
; ***                                                      ***
; ***       System Software for N8VEM Z80 Projects         ***
; ************************************************************
;
; Builders: Wayne Warthen (wwarthen@gmail.com)
;           Douglas Goodall (douglas_goodall@mac.com)
;           David Giles (vk5dg@internode.on.net)
;
; Updated: 2015-04-07
; Version: 2.7.1
;
; Original Copyright Notice:
;
; Copyright 2015, Wayne Warthen, GNU GPL v3

;
;==================================================================================================
;   FLOPPY DISK DRIVER
;==================================================================================================
;
; TODO:
;
;
; PORTS
;


#IF (FDMODE == FDMODE_SCOTT1)
FDC_MSR:	.EQU	050H		; 8272 MAIN STATUS REGISTER
FDC_DATA:	.EQU	051H		; 8272 DATA PORT
FDC_DOR:	.EQU	058H		; DIGITAL OUTPUT REGISTER (LATCH)
#ENDIF
#IF ((FDMODE == FDMODE_DIO) | (FDMODE == FDMODE_ZETA) | (FDMODE == FDMODE_DIO3))
FDC_MSR:	.EQU	036H		; 8272 MAIN STATUS REGISTER
FDC_DATA:	.EQU	037H		; 8272 DATA PORT
FDC_DIR:	.EQU	038H		; DATA INPUT REGISTER
FDC_DOR:	.EQU	03AH		; DIGITAL OUTPUT REGISTER (LATCH)
FDC_DMA:	.EQU	03CH		; PSEUDO DMA DATA PORT
#ENDIF
#IF (FDMODE == FDMODE_SCOTT2)
FDC_MSR:	.EQU	050H		; 8272 MAIN STATUS REGISTER
FDC_DATA:	.EQU	051H		; 8272 DATA PORT
FDC_DOR:	.EQU	058H		; DIGITAL OUTPUT REGISTER
FDC_DCR:	.EQU	048H		; CONFIGURATION CONTROL REGISTER
FDC_TC		.EQU	058H		; TERMINAL COUNT (W/ DACK)
#ENDIF
#IF (FDMODE == FDMODE_ZETA2)
FDC_MSR:	.EQU	030H		; 8272 MAIN STATUS REGISTER
FDC_DATA:	.EQU	031H		; 8272 DATA PORT
FDC_DOR:	.EQU	038H		; DIGITAL OUTPUT REGISTER
FDC_DCR:	.EQU	028H		; CONFIGURATION CONTROL REGISTER
FDC_TC		.EQU	038H		; TERMINAL COUNT (W/ DACK)
#ENDIF
#IF (FDMODE == FDMODE_DIDE)
FDC_BID:	.EQU	00100000B		; IO RANGE 20H-3FH
FDC_MSR:	.EQU	FDC_BID | 01010B	; 8272 MAIN STATUS REGISTER
FDC_DATA:	.EQU	FDC_BID | 01011B	; 8272 DATA PORT
FDC_DOR:	.EQU	FDC_BID | 01100B	; DOR
FDC_DCR:	.EQU	FDC_BID | 01101B	; DCR
FDC_DACK:	.EQU	FDC_BID | 11100B	; DACK
FDC_TC		.EQU	FDC_BID | 11101B	; TERMINAL COUNT (W/ DACK)
FDC_DMA:	.EQU	03CH			; NOT USED BY DIDE
#ENDIF
#IF (FDMODE == FDMODE_N8)
FDC_MSR:	.EQU	08CH	; 8272 MAIN STATUS REGISTER
FDC_DATA:	.EQU	08DH	; 8272 DATA PORT
FDC_DOR:	.EQU	092H	; DOR
FDC_DCR:	.EQU	091H	; DCR
FDC_DACK:	.EQU	090H	; DACK
FDC_TC		.EQU	093H	; TERMINAL COUNT (W/ DACK)
FDC_DMA:	.EQU	03CH	; NOT USED BY N8
#ENDIF
;
; FDC RESULT CODES
;
FRC_OK		.EQU	0		; 00
FRC_NOTIMPL	.EQU	-01H		; FF
FRC_CMDERR	.EQU	-02H		; FE
FRC_ERROR	.EQU	-03H		; FD
FRC_ABORT	.EQU	-04H		; FC
FRC_BUFMAX	.EQU	-05H		; FB
FRC_ABTERM	.EQU	-08H		; F8
FRC_INVCMD	.EQU	-09H		; F7
FRC_DSKCHG	.EQU	-0AH		; F6
FRC_ENDCYL	.EQU	-0BH		; F5
FRC_DATAERR	.EQU	-0CH		; F4
FRC_OVERRUN	.EQU	-0DH		; F3
FRC_NODATA	.EQU	-0EH		; F2
FRC_NOTWRIT	.EQU	-0FH		; F1
FRC_MISADR	.EQU	-10H		; F0
FRC_TOFDCRDY	.EQU	-11H		; EF
FRC_TOSNDCMD	.EQU	-12H		; EE
FRC_TOGETRES	.EQU	-13H		; ED
FRC_TOEXEC	.EQU	-14H		; EC
FRC_TOSEEKWT	.EQU	-15H		; EB
;
#IF (FDTRACE > 0)
;
; FDC STATUS CODE STRINGS
;
FSS_OK		.TEXT	"OK$"
FSS_NOTIMPL	.TEXT	"NOT IMPLEMENTED$"
FSS_CMDERR	.TEXT	"COMMAND ERROR$"
FSS_ERROR	.TEXT	"ERROR$"
FSS_ABORT	.TEXT	"ABORT$"
FSS_BUFMAX	.TEXT	"BUFFER EXCEEDED$"
FSS_ABTERM	.TEXT	"ABNORMAL TERMINATION$"
FSS_INVCMD	.TEXT	"INVALID COMMAND$"
FSS_DSKCHG	.TEXT	"DISK CHANGE$"
FSS_ENDCYL	.TEXT	"END OF CYLINDER$"
FSS_DATAERR	.TEXT	"DATA ERROR$"
FSS_OVERRUN	.TEXT	"OVERRUN$"
FSS_NODATA	.TEXT	"NO DATA$"
FSS_NOTWRIT	.TEXT	"NOT WRITABLE$"
FSS_MISADR	.TEXT	"MISSING ADDRESS MARK$"
FSS_TOFDCRDY	.TEXT	"FDC READY TIMEOUT$"
FSS_TOSNDCMD	.TEXT	"SENDCMD TIMEOUT$"
FSS_TOGETRES	.TEXT	"GET RESULTS TIMEOUT$"
FSS_TOEXEC	.TEXT	"EXEC TIMEOUT$"
FSS_TOSEEKWT	.TEXT	"SEEK WAIT TIMEOUT$"
;
; FDC STATUS STRING TABLE
;
FSST:		.DB 	FRC_OK
                .DW	FSS_OK
FSST_ENTSIZ	.EQU	$ - FSST
		.DB 	FRC_NOTIMPL
                .DW	FSS_NOTIMPL
		.DB	FRC_CMDERR
                .DW	FSS_CMDERR
		.DB	FRC_ERROR
                .DW	FSS_ERROR
		.DB	FRC_ABORT
                .DW	FSS_ABORT
		.DB	FRC_BUFMAX
                .DW	FSS_BUFMAX
		.DB	FRC_ABTERM
                .DW	FSS_ABTERM
		.DB	FRC_INVCMD
                .DW	FSS_INVCMD
		.DB	FRC_DSKCHG
                .DW	FSS_DSKCHG
		.DB	FRC_ENDCYL
                .DW	FSS_ENDCYL
		.DB	FRC_DATAERR
                .DW	FSS_DATAERR
		.DB	FRC_OVERRUN
                .DW	FSS_OVERRUN
		.DB	FRC_NODATA
                .DW	FSS_NODATA
		.DB	FRC_NOTWRIT
                .DW	FSS_NOTWRIT
		.DB	FRC_MISADR
                .DW	FSS_MISADR
		.DB	FRC_TOFDCRDY
                .DW	FSS_TOFDCRDY
		.DB	FRC_TOSNDCMD
                .DW	FSS_TOSNDCMD
		.DB	FRC_TOGETRES
                .DW	FSS_TOGETRES
		.DB	FRC_TOEXEC
                .DW	FSS_TOEXEC
		.DB	FRC_TOSEEKWT
                .DW	FSS_TOSEEKWT
FSST_COUNT	.EQU	(($ - FSST) / FSST_ENTSIZ)	; # ENTRIES IN TABLE
#ENDIF
;
; FDC COMMANDS
;
CMD_READ	.EQU	00000110B	; CMD,HDS/DS,C,H,R,N,EOT,GPL,DTL --> ST0,ST1,ST2,C,H,R,N
CMD_READDEL	.EQU	00001100B	; CMD,HDS/DS,C,H,R,N,EOT,GPL,DTL --> ST0,ST1,ST2,C,H,R,N
CMD_WRITE	.EQU	00000101B	; CMD,HDS/DS,C,H,R,N,EOT,GPL,DTL --> ST0,ST1,ST2,C,H,R,N
CMD_WRITEDEL	.EQU	00001001B	; CMD,HDS/DS,C,H,R,N,EOT,GPL,DTL --> ST0,ST1,ST2,C,H,R,N
CMD_READTRK	.EQU	00000010B	; CMD,HDS/DS,C,H,R,N,EOT,GPL,DTL --> ST0,ST1,ST2,C,H,R,N
CMD_READID	.EQU	00001010B	; CMD,HDS/DS --> ST0,ST1,ST2,C,H,R,N
CMD_FMTTRK	.EQU	00001101B	; CMD,HDS/DS,N,SC,GPL,D --> ST0,ST1,ST2,C,H,R,N
CMD_SCANEQ	.EQU	00010001B	; CMD,HDS/DS,C,H,R,N,EOT,GPL,STP --> ST0,ST1,ST2,C,H,R,N
CMD_SCANLOEQ	.EQU	00011001B	; CMD,HDS/DS,C,H,R,N,EOT,GPL,STP --> ST0,ST1,ST2,C,H,R,N
CMD_SCANHIEQ	.EQU	00011101B	; CMD,HDS/DS,C,H,R,N,EOT,GPL,STP --> ST0,ST1,ST2,C,H,R,N
CMD_RECAL	.EQU	00000111B	; CMD,DS --> <EMPTY>
CMD_SENSEINT	.EQU	00001000B	; CMD --> ST0,PCN
CMD_SPECIFY	.EQU	00000011B	; CMD,SRT/HUT,HLT/ND --> <EMPTY>
CMD_DRVSTAT	.EQU	00000100B	; CMD,HDS/DS --> ST3
CMD_SEEK	.EQU	00001111B	; CMD,HDS/DS --> <EMPTY>
CMD_VERSION	.EQU	00010000B	; CMD --> ST0
;
;
; Specify Command:
; +-----+-----+-----+-----+-----+-----+-----+-----+-----+
; |Byte |  7  |  6  |  5  |  4  |  3  |  2  |  1  |  0  |
; +-----+-----+-----+-----+-----+-----+-----+-----+-----+
; |  0  |  0  |  0  |  0  |  0  |  0  |  0  |  1  |  1  |
; |  1  | ----- STEP RATE ----- | -- HEAD UNLOAD TIME - |
; |  2  | ------------ HEAD LOAD TIME ----------- | NDM |
; +-----+-----+-----+-----+-----+-----+-----+-----+-----+
;
;
; Step Rate (milliseconds):              Head Unload Time (milliseconds):       Head Load Time (milliseconds):
; +------+------+------+------+------+   +------+------+------+------+------+   +------+------+------+------+------+
; |      |         BITRATE           |   |      |         BITRATE           |   |      |         BITRATE           |
; |  VAL | 1.0M | 500K | 300K | 250K |   |  VAL | 1.0M | 500K | 300K | 250K |   |  VAL | 1.0M | 500K | 300K | 250K |
; +------+------+------+------+------+   +------+------+------+------+------+   +------+------+------+------+------+
; |    0 |  8.0 | 16.0 | 26.7 | 32.0 |   |    0 |  128 |  256 |  426 |  512 |   |    0 |  128 |  256 |  426 |  512 |
; |    1 |  7.5 | 15.0 | 25.0 | 30.0 |   |    1 |    8 |   16 | 26.7 |   32 |   |    1 |    1 |    2 |  3.3 |    4 |
; |    2 |  7.0 | 14.0 | 23.3 | 28.0 |   |    2 |   16 |   32 | 53.3 |   64 |   |    2 |    2 |    4 |  6.7 |    8 |
; |  ... |  ... |  ... |  ... |  ... |   |  ... |  ... |  ... |  ... |  ... |   |  ... |  ... |  ... |  ... |  ... |
; |   14 |  1.0 |  2.0 |  3.3 |  4.0 |   |   14 |  112 |  224 |  373 |  448 |   |  126 |  126 |  252 |  420 |  504 |
; |   15 |  0.5 |  1.0 |  1.7 |  2.0 |   |   15 |  120 |  240 |  400 |  480 |   |  127 |  127 |  254 |  423 |  508 |
; +------+------+------+------+------+   +------+------+------+------+------+   +------+------+------+------+------+
;
; IBM PS/2 CALLS FOR:
;   STEP RATE: 3ms (6ms FOR ALL 41mm OR 720K DRIVES)
;   HEAD LOAD TIME: 15ms
;
; STATIC CONFIGURATION, NEVER CHANGES (PRIVATE)
;
FCD_MT		.EQU	000H		; MULTI-TRACK, WE DON'T USE, SET TO 0
FCD_MFM		.EQU	001H		; MFM, 0=FM, 1=MFM, WE USE MFM ALWAYS
FCD_SK		.EQU	000H		; SKIP MODE, WE DON'T USE, SET TO 0
FCD_N		.EQU	002H		; SECTOR SIZE, N=2 FOR 512 BYTES
FCD_DTL		.EQU	0FFH		; DATA LENGTH (WHEN N=0, SET TO FF OTHERWISE)
FCD_STP		.EQU	001H		; SECTOR SCAN TYPE, 1=CONTIG, 2=ALTERNATING
;
FCD_PC720	.DB	050H		; NUMBER OF CYLINDERS
		.DB	002H		; NUMBER OF HEADS
		.DB	009H		; NUMBER OF SECTORS
		.DB	001H		; START OF TRACK (ID OF FIRST SECTOR, USUALLY 1)
		.DB	009H		; SECTOR COUNT
		.DW	200H		; SECTOR SIZE IN BYTES
		.DB	02AH		; GAP LENGTH (R/W)
		.DB	050H		; GAP LENGTH (FORMAT)
		.DB	(13 << 4) | 0	; SRT = 6ms, HUT = 512ms
		.DB	(4 << 1) | 1	; HLT = 16ms, ND = YES
		.DB	DOR_BR250	; DOR
		.DB	DCR_BR250	; DCR
#assert	(($ - FCD_PC720) == FCD_LEN)
;
FCD_PC144	.DB	050H		; NUMBER OF CYLINDERS
		.DB	002H		; NUMBER OF HEADS
		.DB	012H		; NUMBER OF SECTORS
		.DB	001H		; START OF TRACK (ID OF FIRST SECTOR, USUALLY 1)
		.DB	012H		; SECTOR COUNT
		.DW	200H		; SECTOR SIZE IN BYTES
		.DB	01BH		; GAP LENGTH (R/W)
		.DB	06CH		; GAP LENGTH (FORMAT)
		.DB	(13 << 4) | 0	; SRT = 3ms, HUT = 256ms
		.DB	(8 << 1) | 1	; HLT = 16ms, ND = YES
		.DB	DOR_BR500	; DOR
		.DB	DCR_BR500	; DCR
#assert	(($ - FCD_PC144) == FCD_LEN)
;
FCD_PC360	.DB	028H		; NUMBER OF CYLINDERS
		.DB	002H		; NUMBER OF HEADS
		.DB	009H		; NUMBER OF SECTORS
		.DB	001H		; START OF TRACK (ID OF FIRST SECTOR, USUALLY 1)
		.DB	009H		; SECTOR COUNT
		.DW	200H		; SECTOR SIZE IN BYTES
		.DB	02AH		; GAP LENGTH (R/W)
		.DB	050H		; GAP LENGTH (FORMAT)
		.DB	(13 << 4) | 0	; SRT = 6ms, HUT = 512ms
		.DB	(4 << 1) | 1	; HLT = 16ms, ND = YES
		.DB	DOR_BR250	; DOR
		.DB	DCR_BR250	; DCR
#assert	(($ - FCD_PC360) == FCD_LEN)
;
FCD_PC120	.DB	050H		; NUMBER OF CYLINDERS
		.DB	002H		; NUMBER OF HEADS
		.DB	00FH		; NUMBER OF SECTORS
		.DB	001H		; START OF TRACK (ID OF FIRST SECTOR, USUALLY 1)
		.DB	00FH		; SECTOR COUNT
		.DW	200H		; SECTOR SIZE IN BYTES
		.DB	01BH		; GAP LENGTH (R/W)
		.DB	054H		; GAP LENGTH (FORMAT)
		.DB	(10 << 4) | 0	; SRT = 6ms, HUT = 256ms
		.DB	(8 << 1) | 1	; HLT = 16ms, ND = YES
		.DB	DOR_BR500	; DOR
		.DB	DCR_BR500	; DCR
#assert	(($ - FCD_PC120) == FCD_LEN)
;
FCD_PC111	.DB	04DH		; NUMBER OF CYLINDERS
		.DB	002H		; NUMBER OF HEADS
		.DB	00FH		; NUMBER OF SECTORS
		.DB	001H		; START OF TRACK (ID OF FIRST SECTOR, USUALLY 1)
		.DB	00FH		; SECTOR COUNT
		.DW	200H		; SECTOR SIZE IN BYTES
		.DB	01BH		; GAP LENGTH (R/W)
		.DB	054H		; GAP LENGTH (FORMAT)
		.DB	(13 << 4) | 0	; SRT = 3ms, HUT = 256ms
		.DB	(25 << 1) | 1	; HLT = 50ms, ND = YES
		.DB	DOR_BR500	; DOR
		.DB	DCR_BR500	; DCR
#assert	(($ - FCD_PC111) == FCD_LEN)
;
; FCD LOOKUP TABLE (CALLED TO SET HL TO ADDRESS OF MEDIA DATA ABOVE)
; ENTRIES BELOW MUST MATCH COUNT AND VALUES OF FDMXXX IN STD.ASM
;
FCD_TBL:
		LD	HL,FCD_PC720
                RET	; FDM720 = 0
		LD	HL,FCD_PC144
                RET	; FDM144 = 1
		LD	HL,FCD_PC360
                RET	; FDM360 = 2
		LD	HL,FCD_PC120
                RET	; FDM120 = 3
		LD	HL,FCD_PC111
                RET	; FDM111 = 4
;
; DOR BITS (3AH)
;
;	DISKIO			250KBPS		500KBPS
;	-------			-------		-------
;D7	/DC/RDY			1 (N/A)		1 (N/A)
;D6	/REDWC (DENSITY)	0 (DD)		1 (HD)
;D5	P0* (PRECOMP BIT 0)	1 \		0 \
;D4	P1* (PRECOMP BIT 1)	0 (125NS)	1 (125NS)
;D3	P2* (PRECOMP BIT 2)	0 /		0 /
;D2	MINI (BITRATE)		1 (250KBPS)	0 (500KBPS)
;D1	/MOTOR (ACTIVE LO)	1 (OFF)		1 (OFF)
;D0	TC (TERMINAL COUNT)	0 (OFF)		0 (OFF)
;
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
